jonw0224/PPMScope/Contributions/Dennis Waddell/Analog_Board.pdf

Analog Board

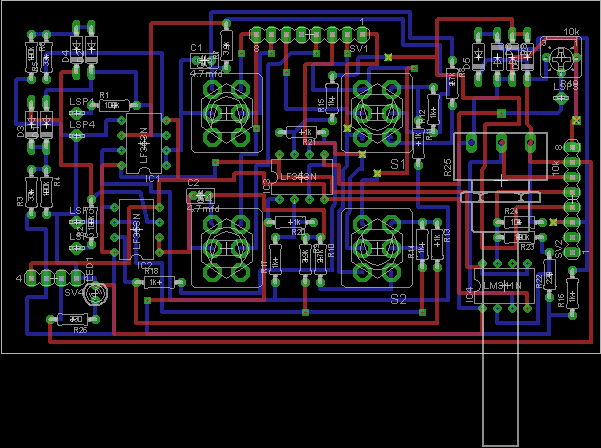
[picture p5: figure]

Note:
1. Board Size 4 x 2.35
2. Red traces on top side blue on bottom
3. R25 shows shaft horizontal is actually mounted vertical through front panel.
