jonw0224/PPMScope/Contributions/Dennis Waddell/Anlgsch.pdf

Analog Board Schematic

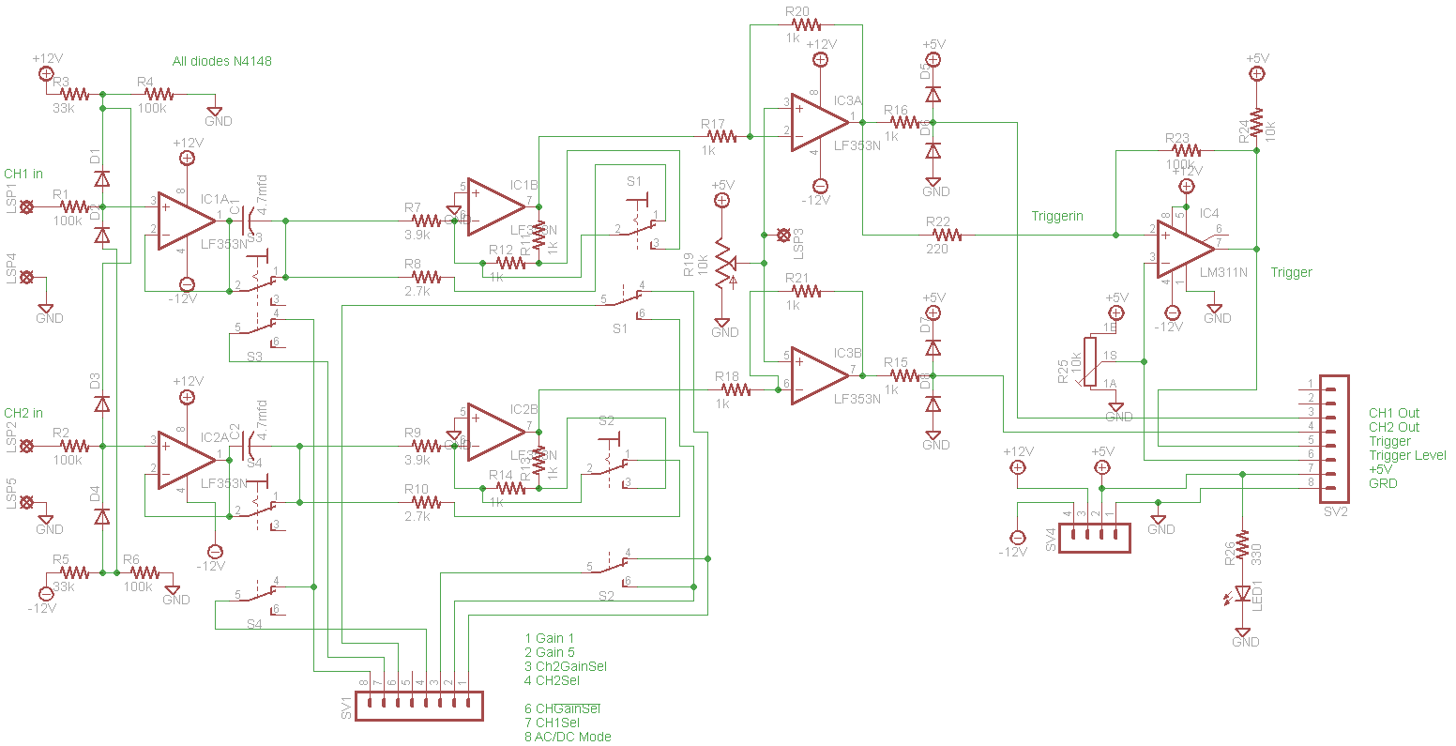
[picture p6: figure]

Note:
1. SV1 and SV2 headers mount on bottom side of board.
2. SV4 Rt. Angle header mount on top side of board.
