jonw0224/PPMScope/Contributions/Dennis Waddell/Power_Supply_Board.pdf

Power Supply Board

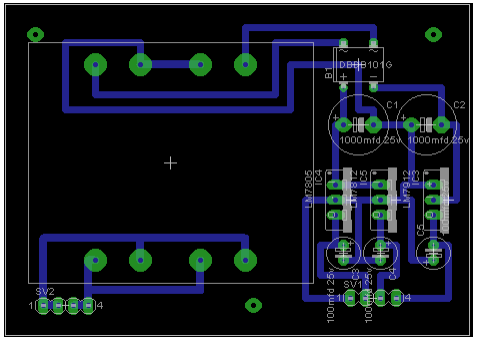
[picture p7: figure]
