jonw0224/PPMScope/Contributions/Dennis Waddell/Power_Supply_Schemati1.pdf

Power Supply Schematic

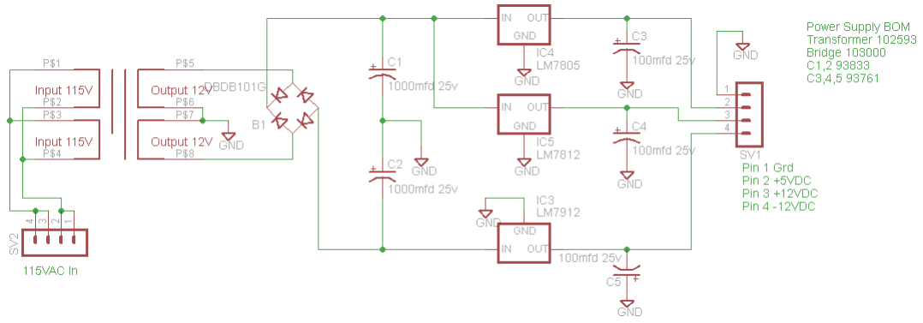
[picture p8: figure]
