jonw0224/PPMScope/Contributions/Dennis Waddell/Processor_Board.pdf

Processor Board

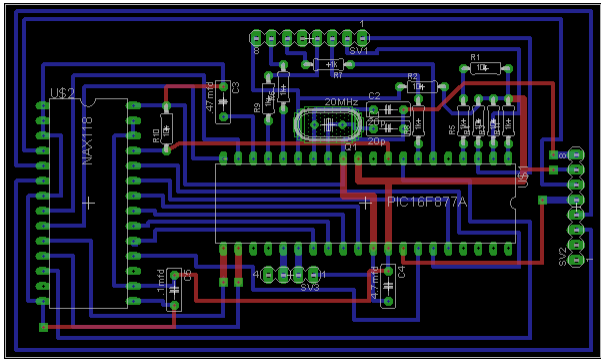
[picture p9: figure]

Note:
1. Board size 3.95 x 2.35
2. Red top side blue bottom.
