jonw0224/PPMScope/Contributions/Dennis Waddell/Processor_Board_Schemati1.pdf

Processor Board Schematic

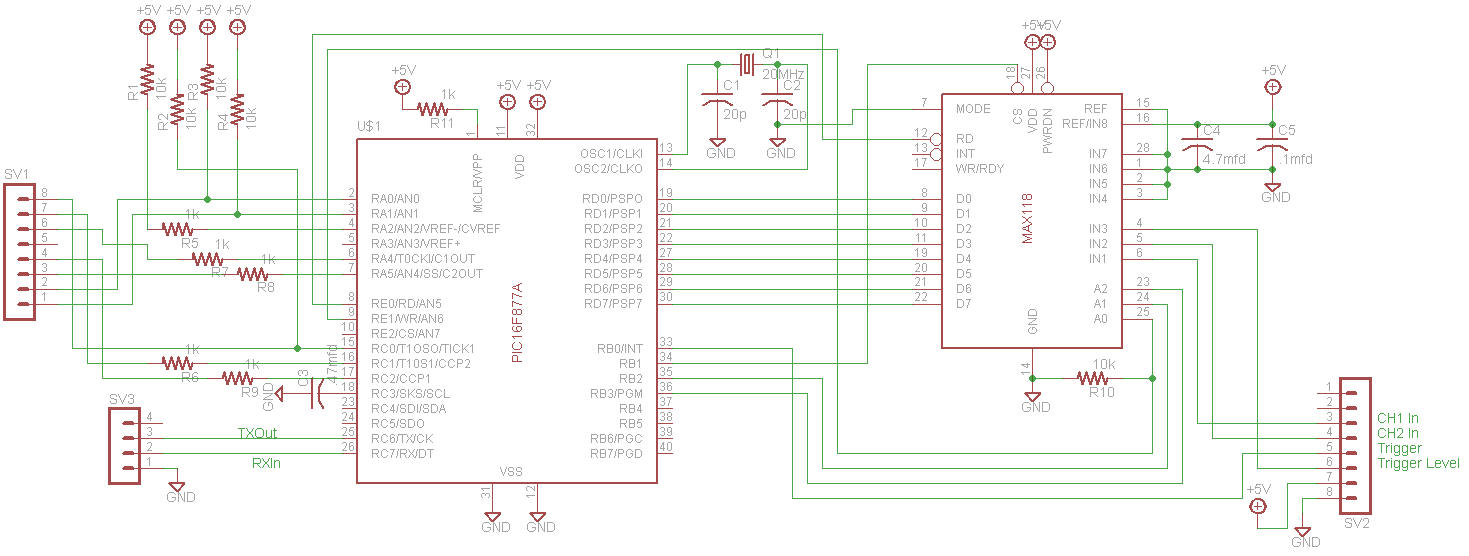
[picture p10: figure]
