jonw0224/PPMScope/PCB/Version 1.05/PCB.pdf

New_job (Current screen) Scale=1.00 Thu Dec 22 17:05:05 2011

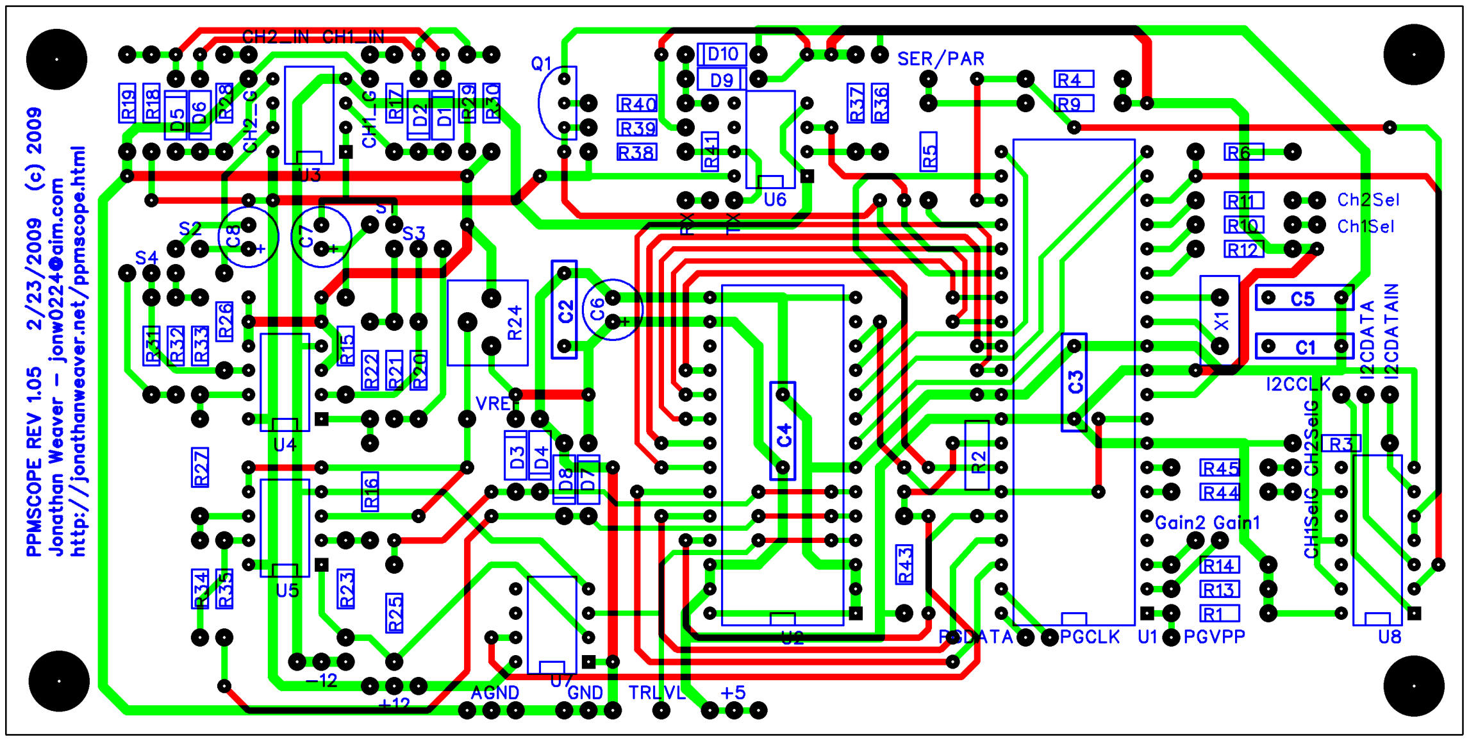
[picture p12: figure]
