jonw0224/PPMScope/PCB/Version 1.05/PCBBottom.pdf

New_job (Current screen) Scale=1.00 Thu Dec 22 17:06:14 2011

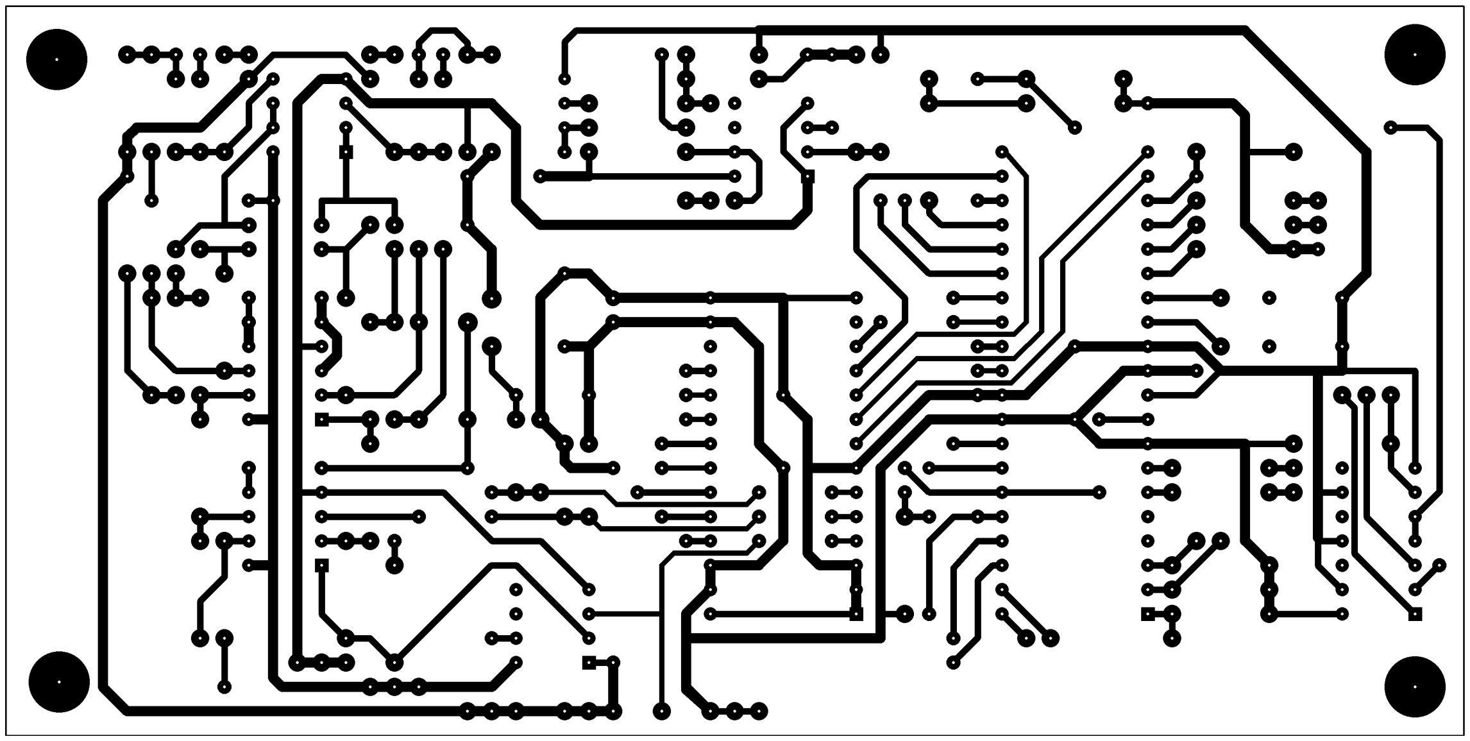
[picture p13: figure]
