jonw0224/PPMScope/PCB/Version 1.05/PCBTopMirrored.pdf

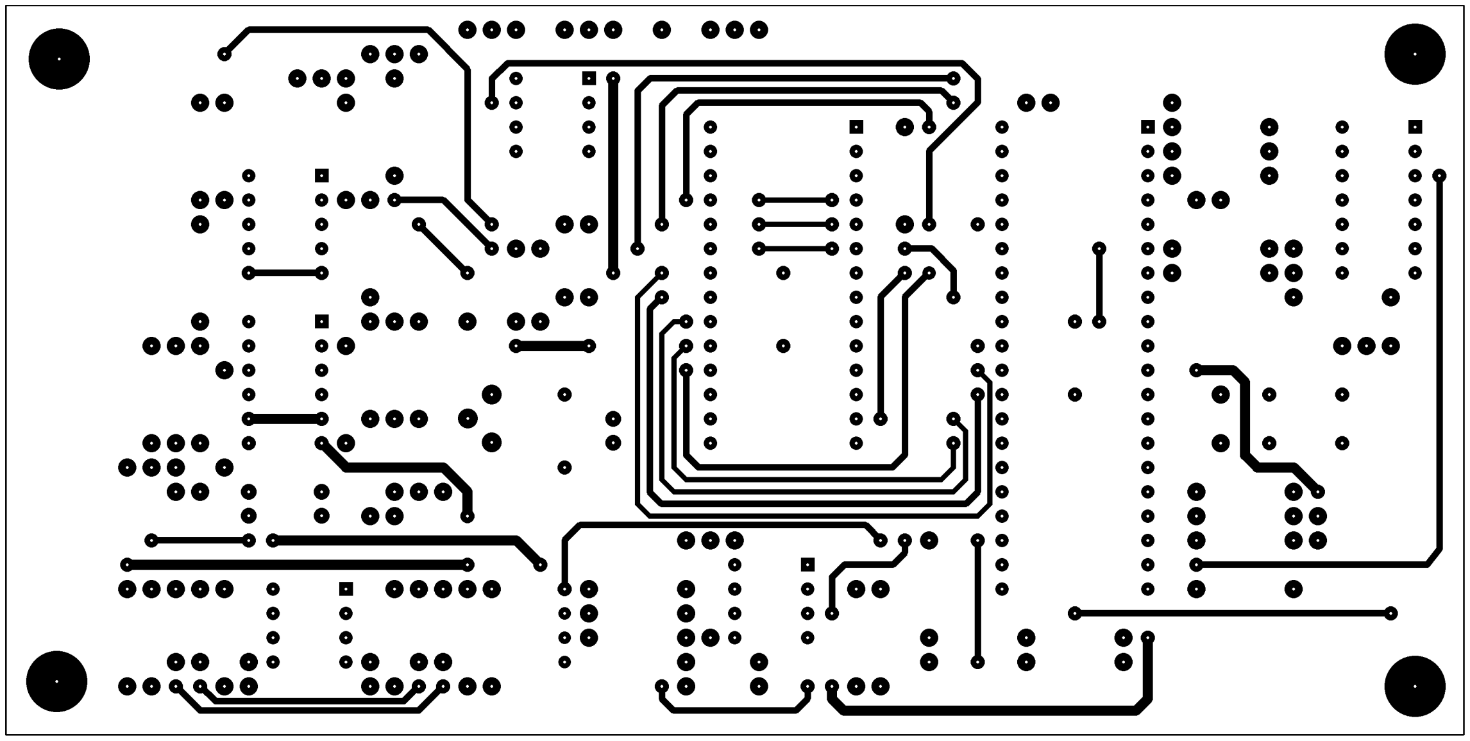
[picture p14: figure]

New_job (Current screen) Scale=1.00 Thu Dec 22 17:07:16 2011
