jonw0224/PPMScope/Contributions/Chris_PCB/bottom_copper.png

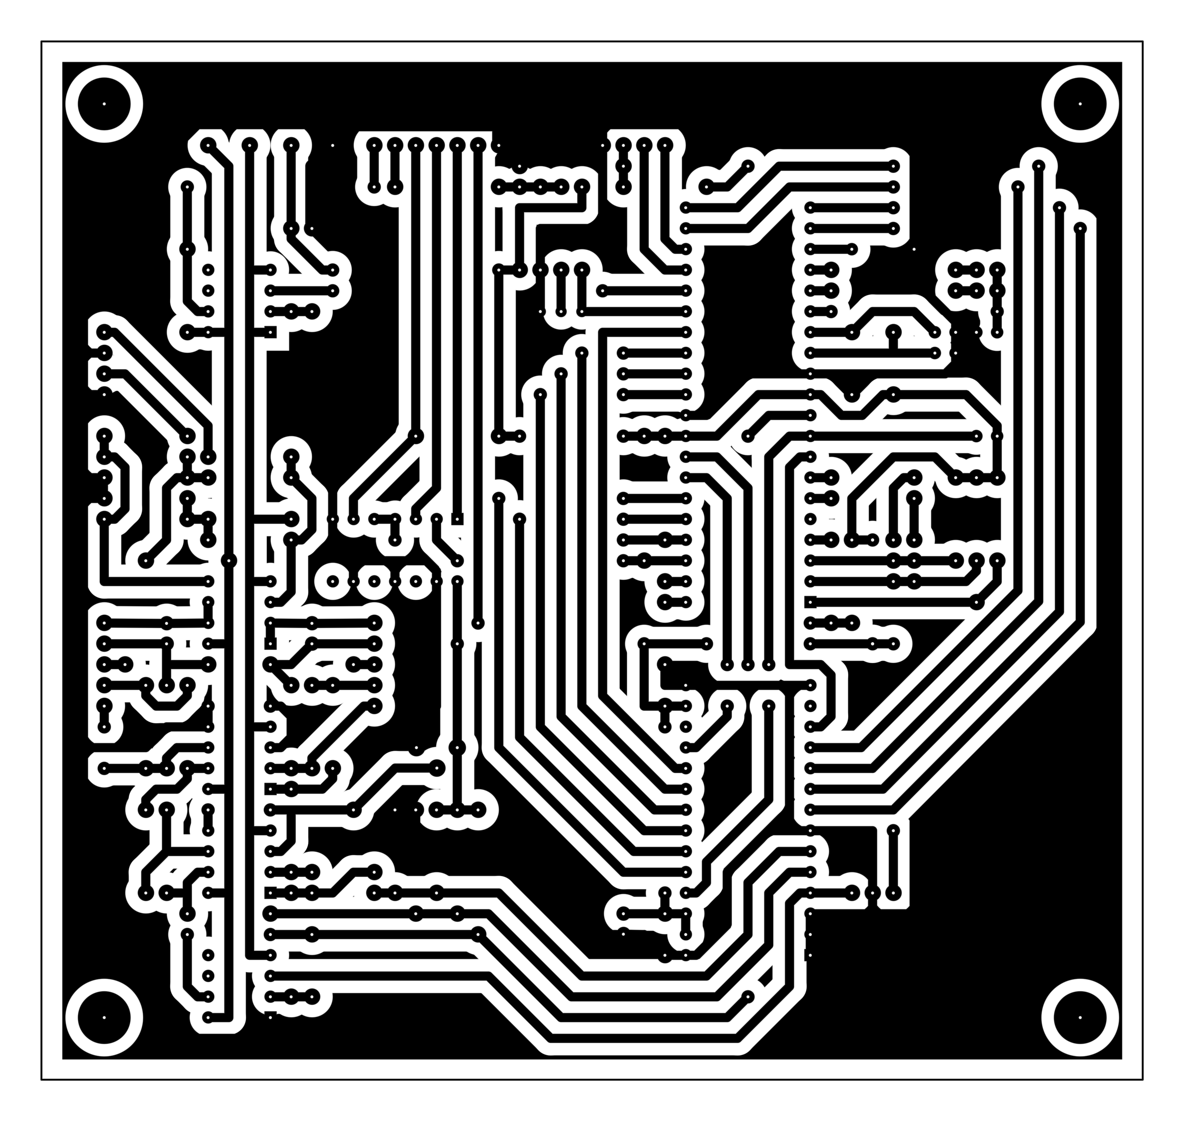
Contributions/Chris_PCB/bottom_copper.png
