jonw0224/PPMScope/Contributions/DaveDeBoer_Perfboard/PPmScope_1.05_bot.jpg

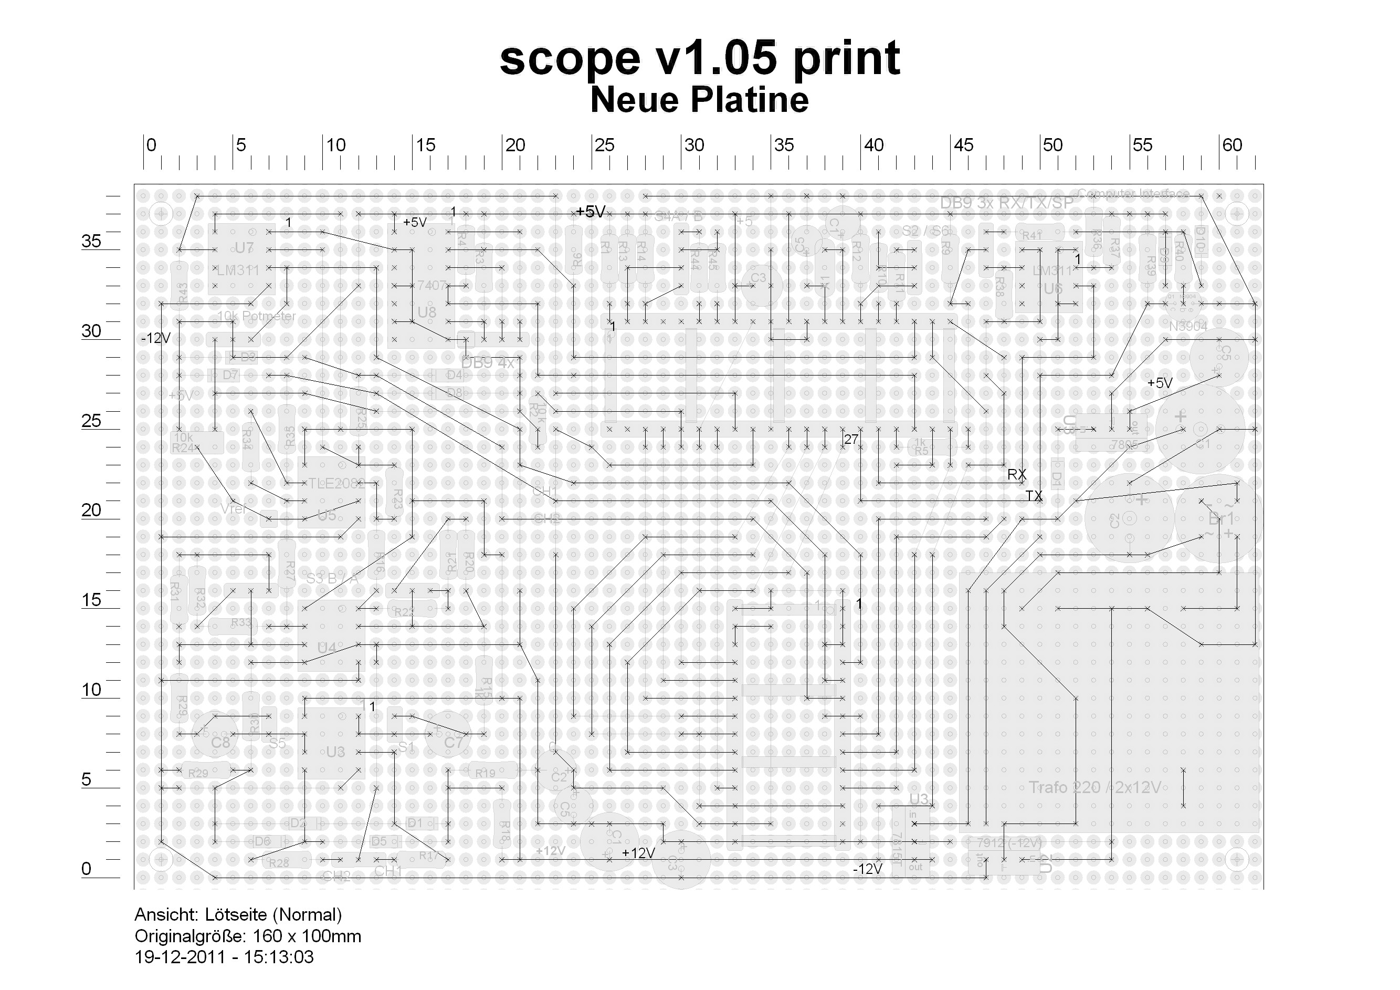
Contributions/DaveDeBoer_Perfboard/PPmScope_1.05_bot.jpg
