jonw0224/PPMScope/Contributions/DaveDeBoer_Perfboard/PPmScope_1.05_top.jpg

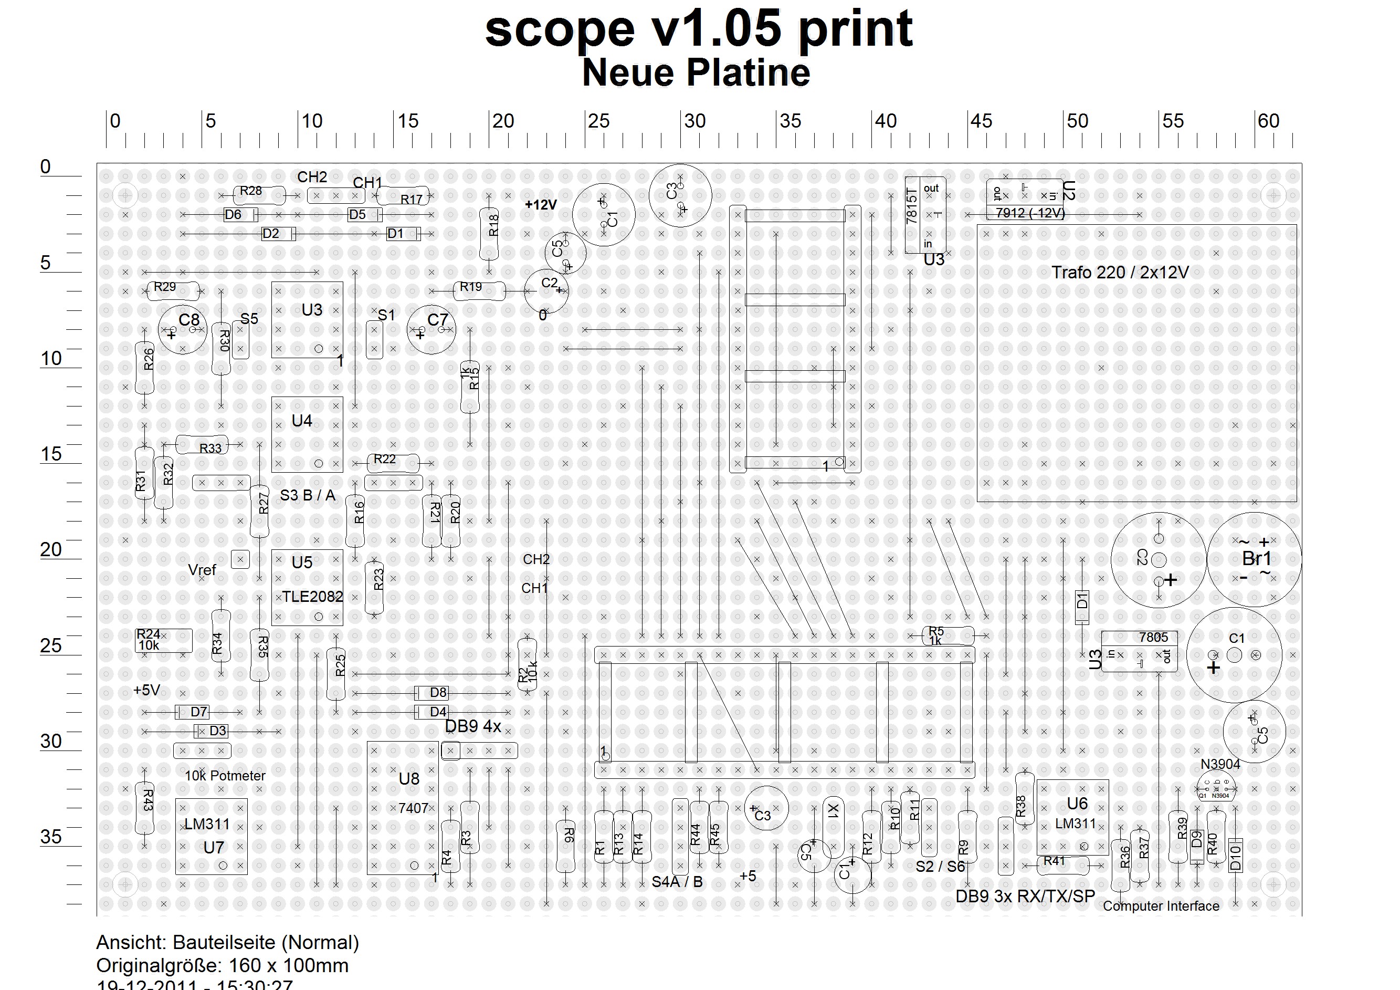
Contributions/DaveDeBoer_Perfboard/PPmScope_1.05_top.jpg
