jonw0224/PPMScope/Contributions/Dennis Waddell/01070001.JPG

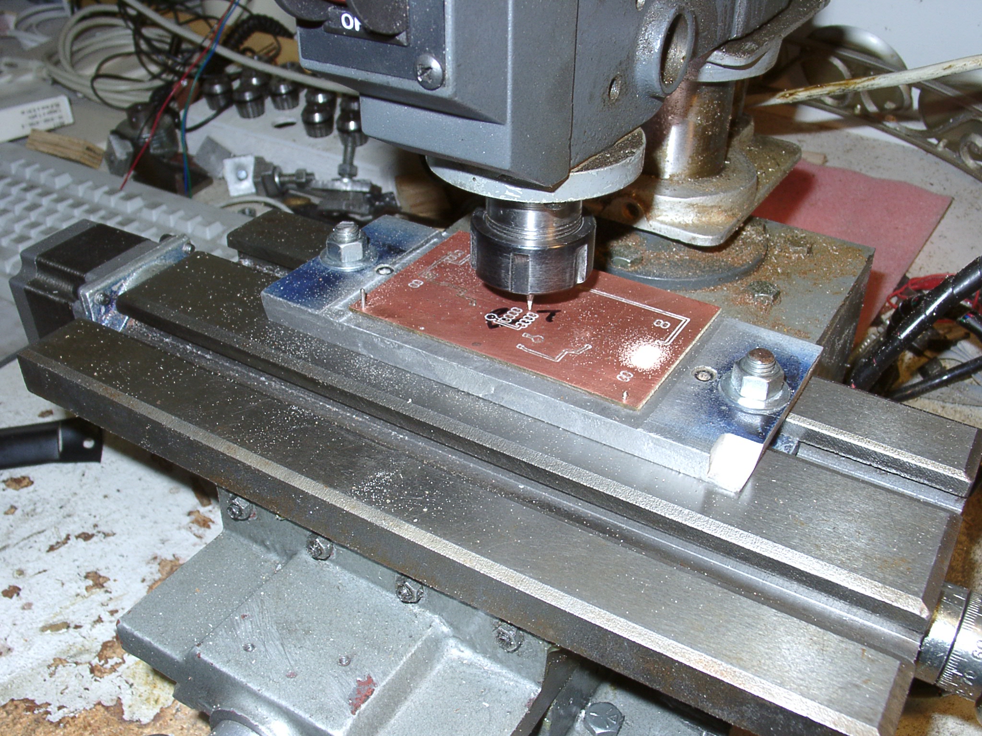
Contributions/Dennis Waddell/01070001.JPG
