jonw0224/PPMScope/Contributions/Dennis Waddell/01070002.JPG

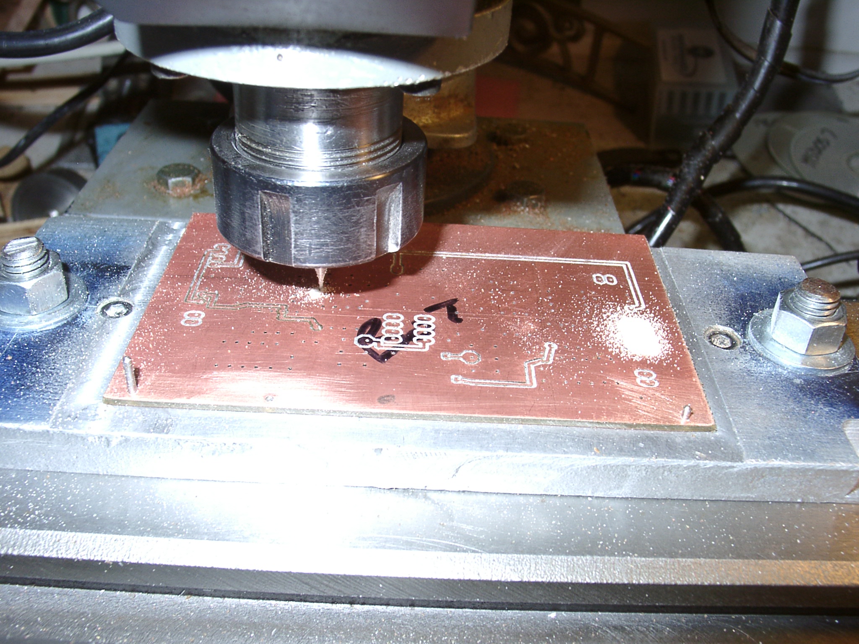
Contributions/Dennis Waddell/01070002.JPG
