jonw0224/PPMScope/Contributions/Dennis Waddell/02050001.JPG

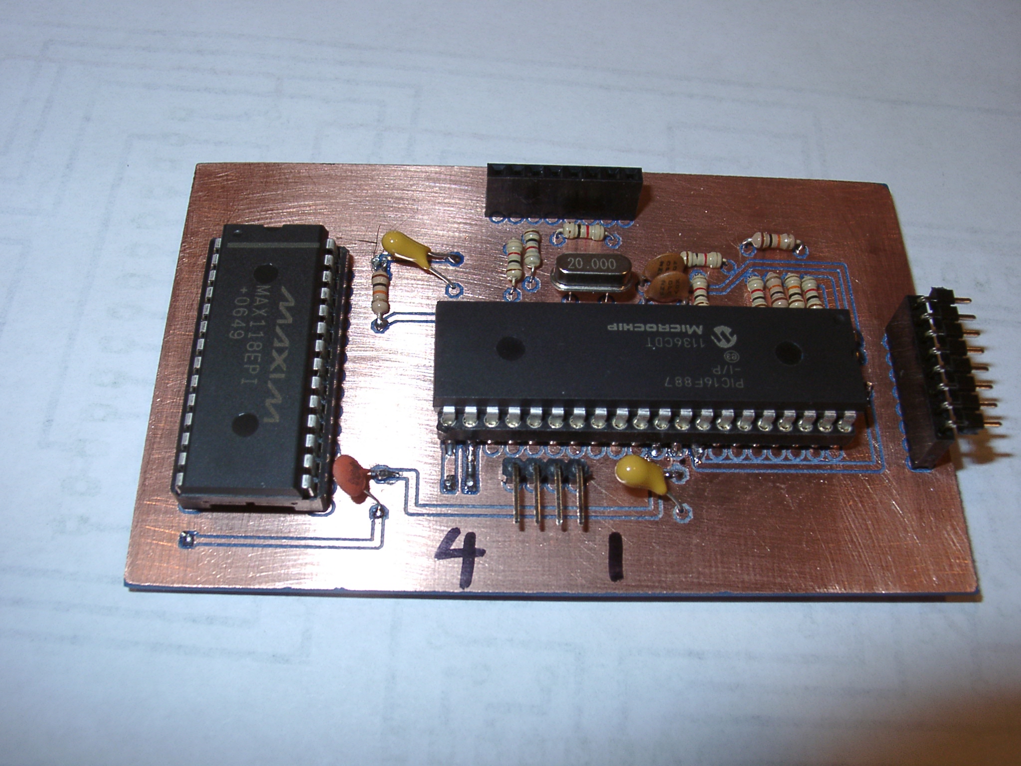
Contributions/Dennis Waddell/02050001.JPG
