jonw0224/PPMScope/Contributions/Dennis Waddell/02050003.JPG

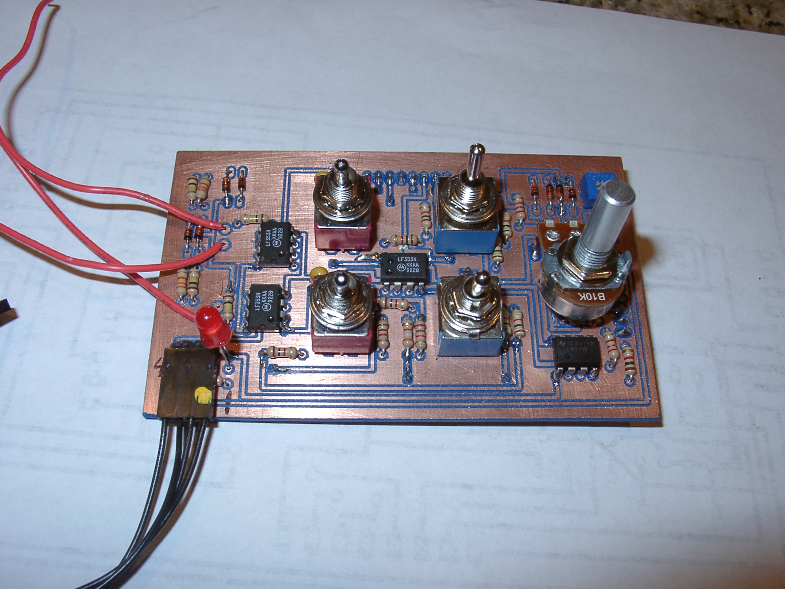
Contributions/Dennis Waddell/02050003.JPG
