jonw0224/PPMScope/Contributions/Dennis Waddell/02050004.JPG

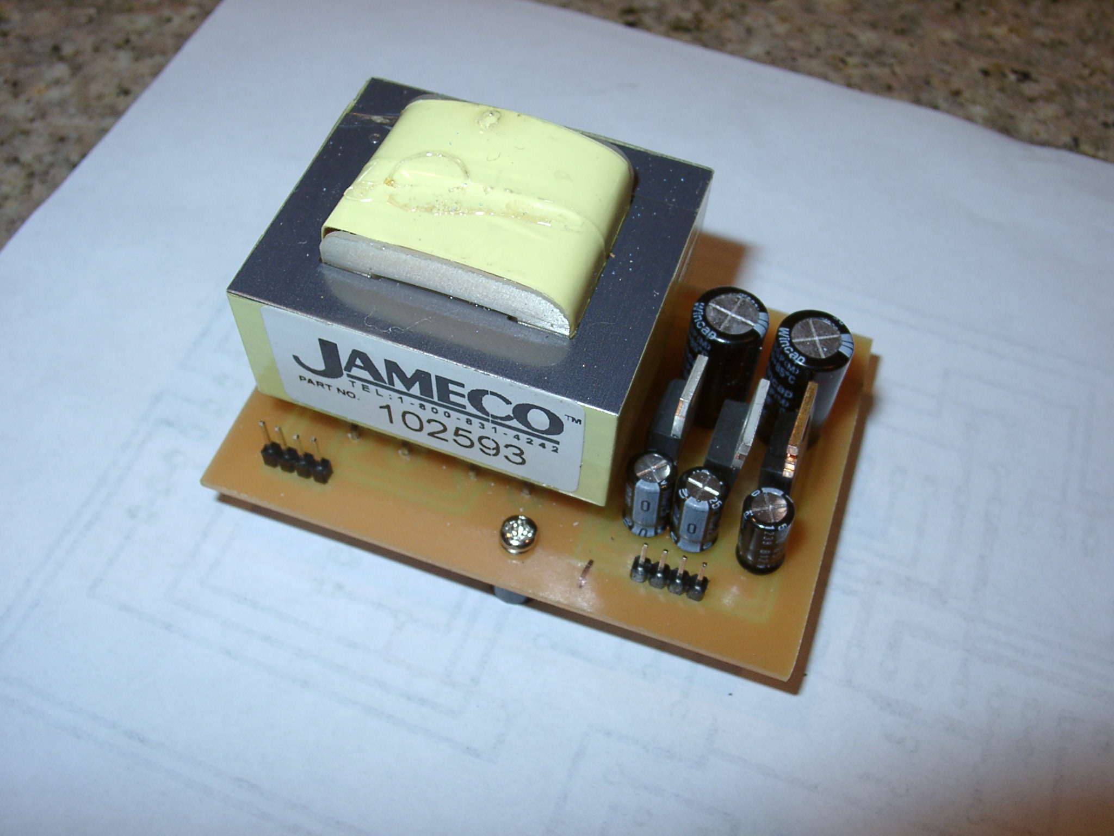
Contributions/Dennis Waddell/02050004.JPG
