jonw0224/PPMScope/Contributions/Dennis Waddell/02180001.JPG

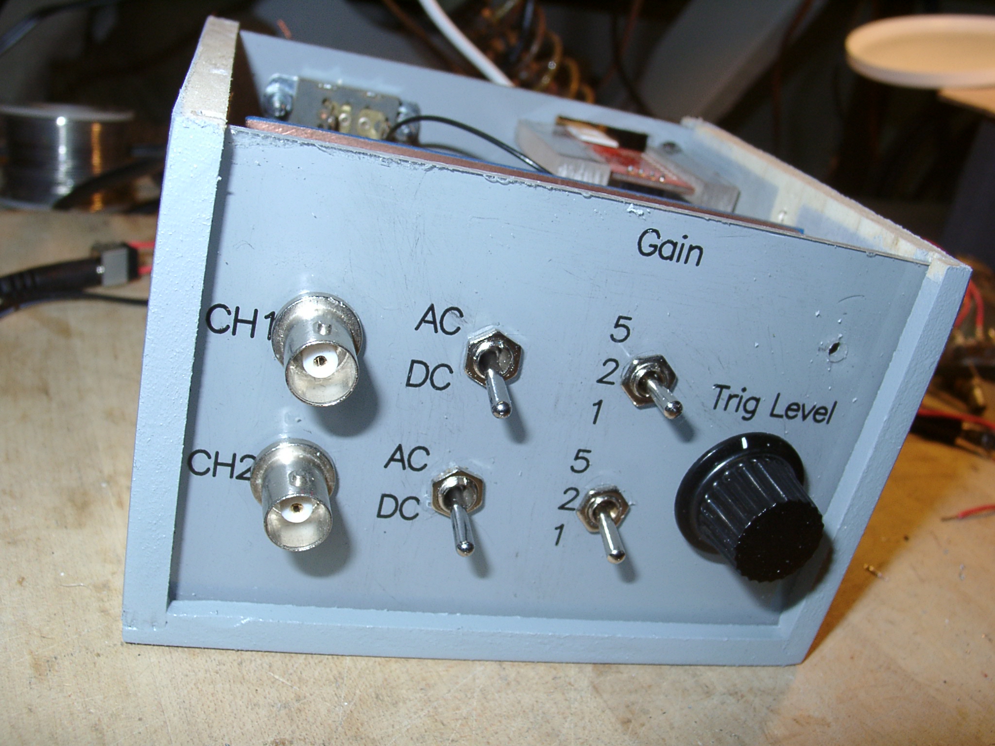
Contributions/Dennis Waddell/02180001.JPG
