jonw0224/PPMScope/Contributions/Dennis Waddell/02180002.JPG

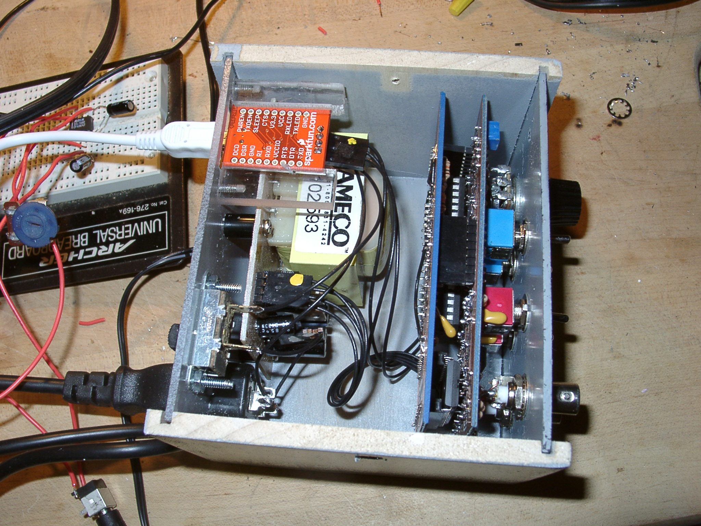
Contributions/Dennis Waddell/02180002.JPG
