jonw0224/PPMScope/Contributions/Dennis Waddell/02180003.JPG

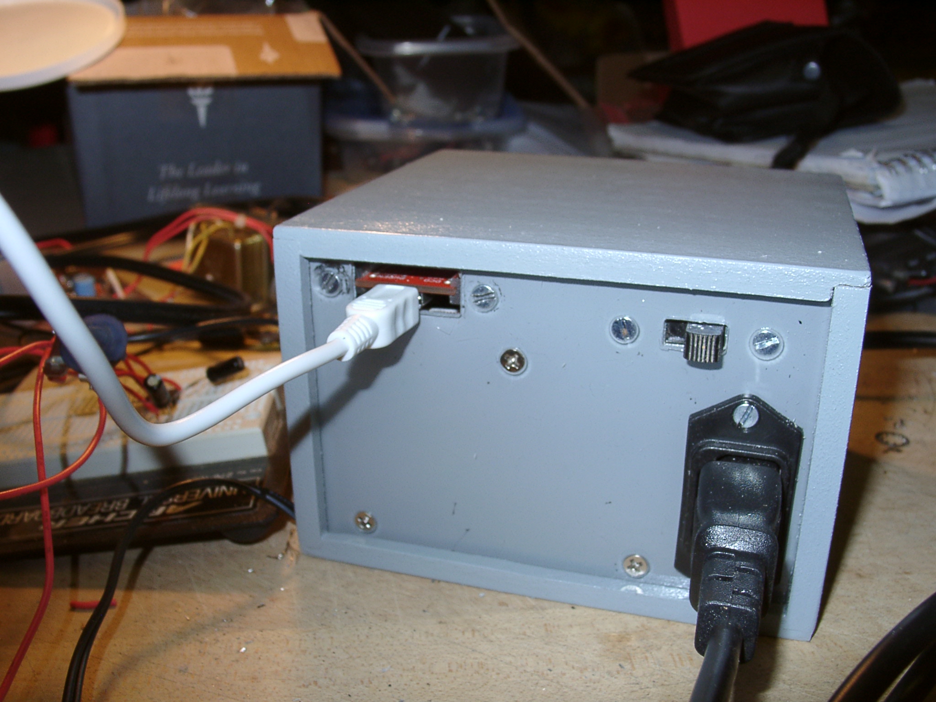
Contributions/Dennis Waddell/02180003.JPG
