jonw0224/PPMScope/Contributions/Dennis Waddell/02180005.JPG

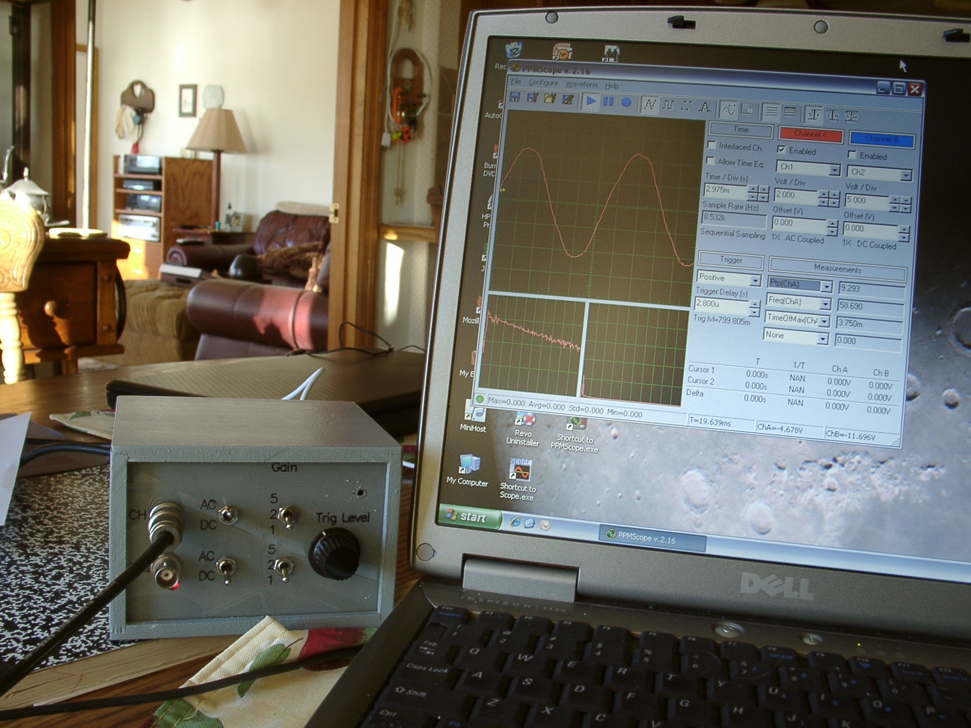
Contributions/Dennis Waddell/02180005.JPG
