jonw0224/PPMScope/Contributions/Paul Messer/DSOscope_A02/PCB/A02/CAM_DSOscope_AnalogBrd_A02/DSOscope_AnalogBrd_A02.JPG

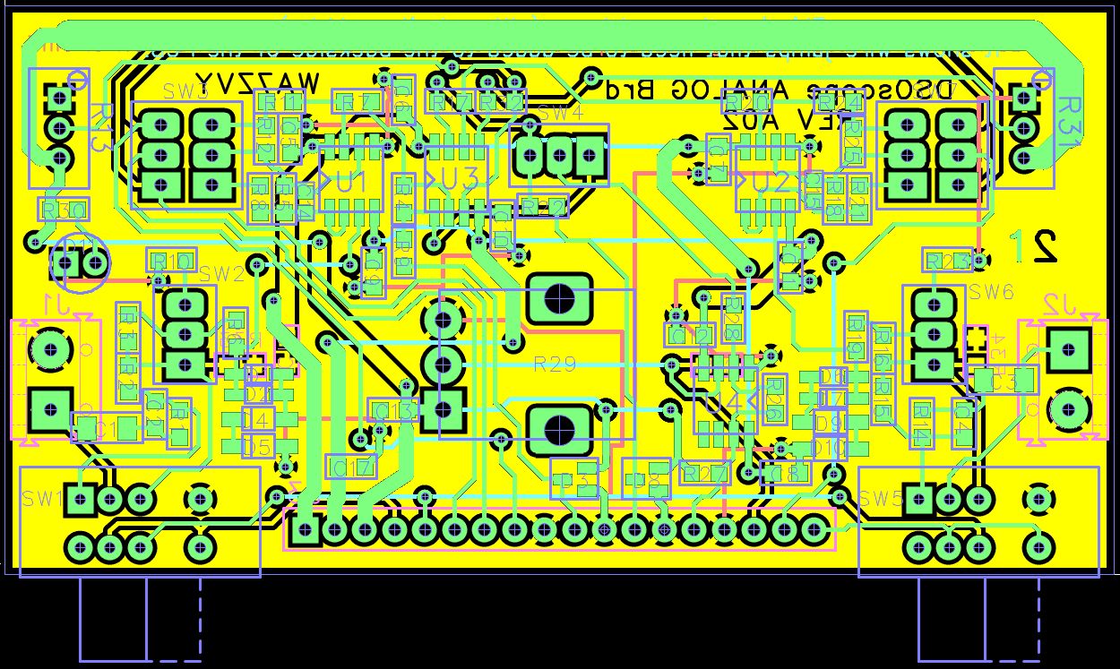
Contributions/Paul Messer/DSOscope_A02/PCB/A02/CAM_DSOscope_AnalogBrd_A02/DSOscope_AnalogBrd_A02.JPG
