jonw0224/PPMScope/Contributions/Paul Messer/DSOscope_A02/Photos/P1010014.JPG

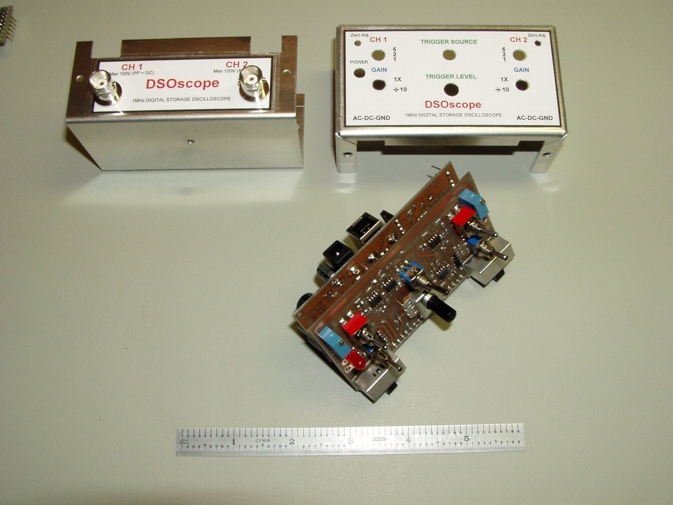
Contributions/Paul Messer/DSOscope_A02/Photos/P1010014.JPG
