jonw0224/PPMScope/Contributions/Paul Messer/DSOscope_A02/Photos/P1010017.JPG

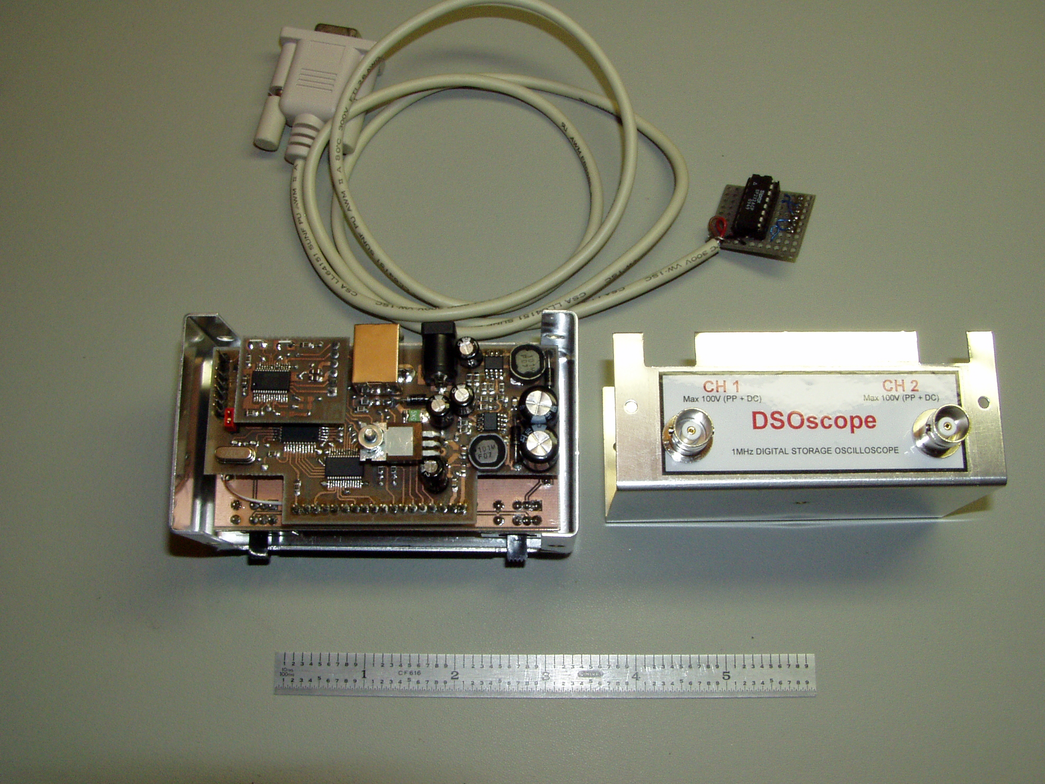
Contributions/Paul Messer/DSOscope_A02/Photos/P1010017.JPG
