jonw0224/PPMScope/Contributions/Paul Messer/DSOscope_A03/DSOscope_Rev_A03_20130113/PCB/A03/CAM_DSOscope_USBBrd_A03/DSOscope_USBBrd_A03_TOP.JPG

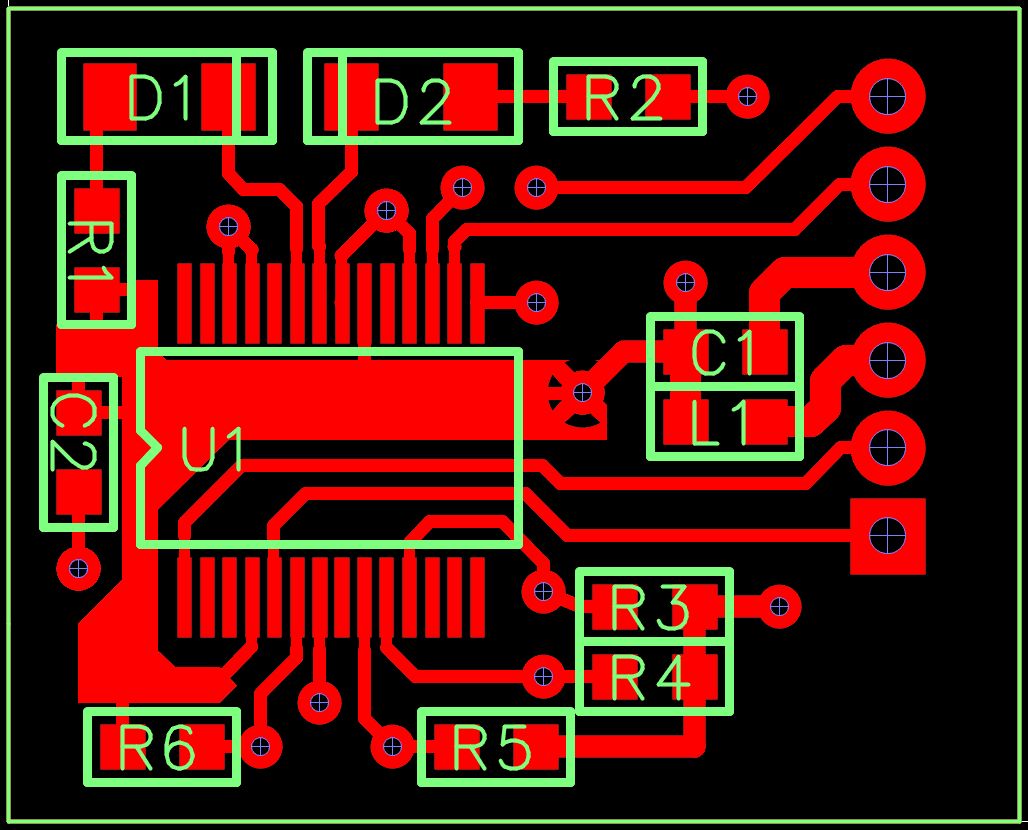
Contributions/Paul Messer/DSOscope_A03/DSOscope_Rev_A03_20130113/PCB/A03/CAM_DSOscope_USBBrd_A03/DSOscope_USBBrd_A03_TOP.JPG
