jonw0224/PPMScope/Contributions/Paul Messer/DSOscope_A03/DSOscope_Rev_A03_20130201/PCB/A03/AnalogBrd_A03_etch_bottom.jpg

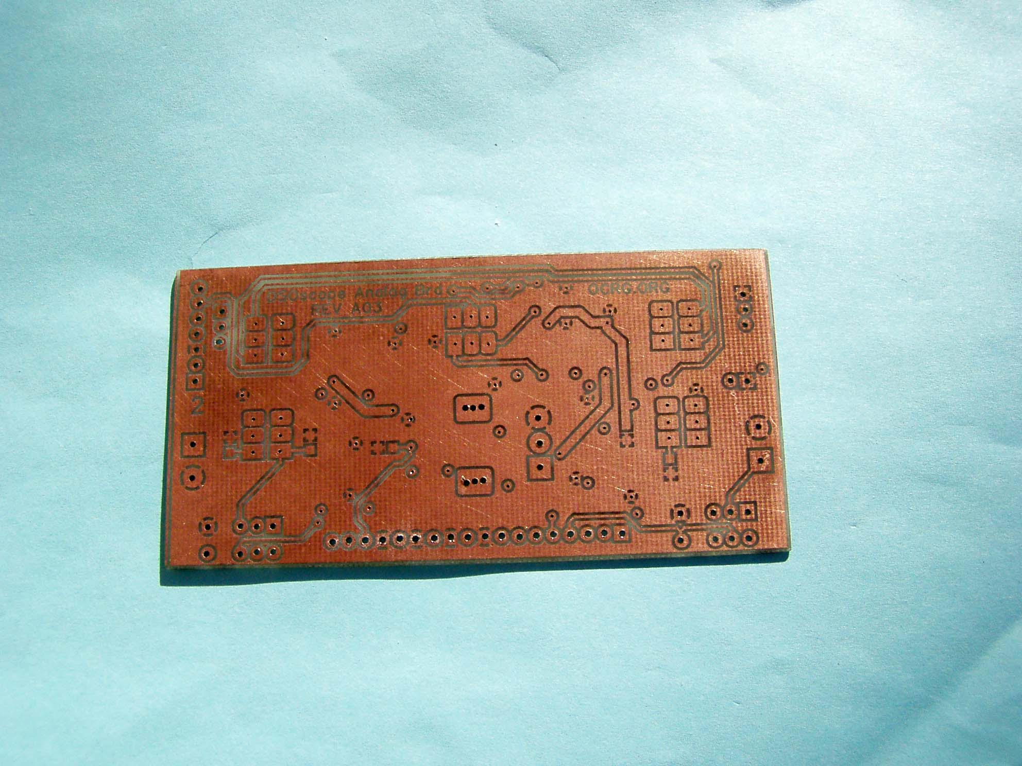
Contributions/Paul Messer/DSOscope_A03/DSOscope_Rev_A03_20130201/PCB/A03/AnalogBrd_A03_etch_bottom.jpg
