jonw0224/PPMScope/Contributions/Paul Messer/DSOscope_A03/DSOscope_Rev_A03_20130201/PCB/A03/CAM_DSOscope_AnalogBrd_A03/DSOscope_AnalogBrd_A03_TOP.JPG

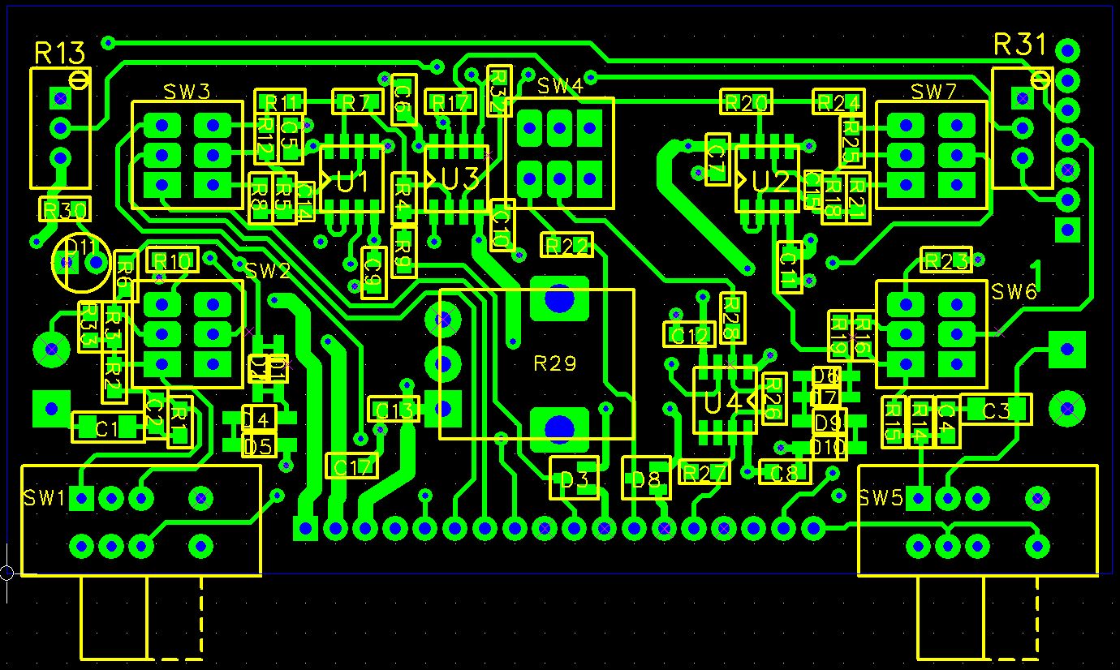
Contributions/Paul Messer/DSOscope_A03/DSOscope_Rev_A03_20130201/PCB/A03/CAM_DSOscope_AnalogBrd_A03/DSOscope_AnalogBrd_A03_TOP.JPG
