jonw0224/PPMScope/Contributions/Paul Messer/P1010008.JPG

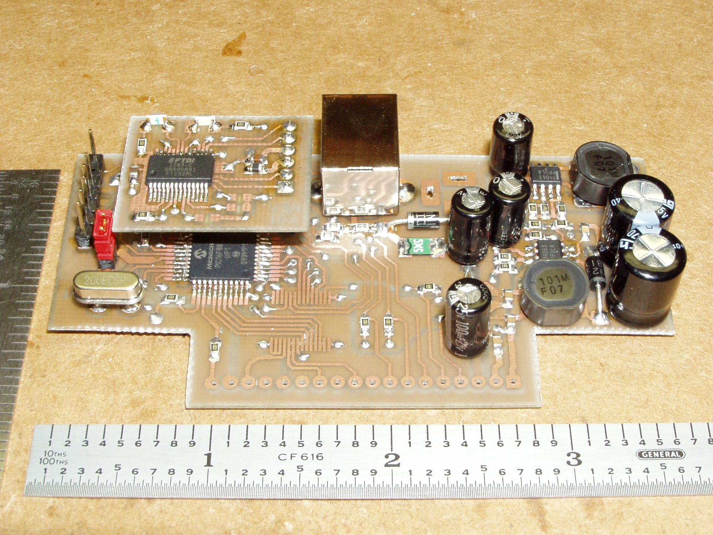
Contributions/Paul Messer/P1010008.JPG
