jonw0224/PPMScope/PCsource/Help/compile.jpg

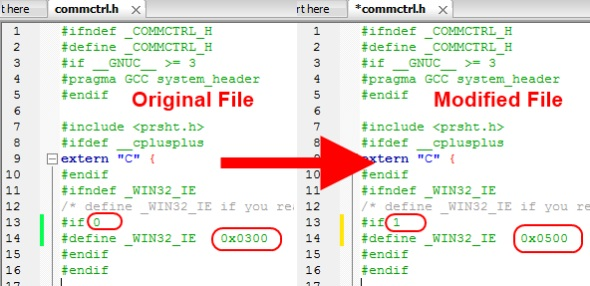
PCsource/Help/compile.jpg
