jonw0224/PPMScope/PCsource/Help/front.jpg

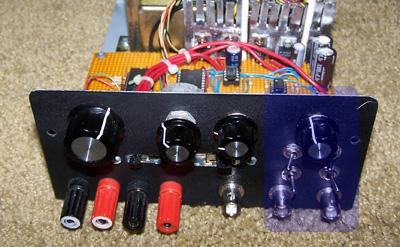
PCsource/Help/front.jpg
