jonw0224/PPMScope/PCsource/Help/library.jpg

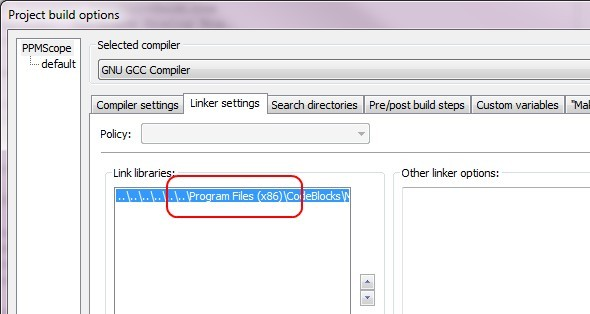
PCsource/Help/library.jpg
