jonw0224/PPMScope/PCsource/Help/parallel_conn_1.jpg

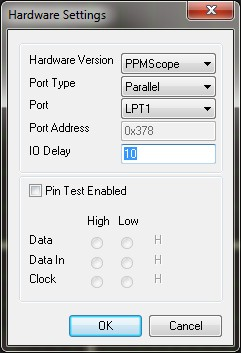
PCsource/Help/parallel_conn_1.jpg
