jonw0224/PPMScope/PCsource/Help/parallel_conn_2.jpg

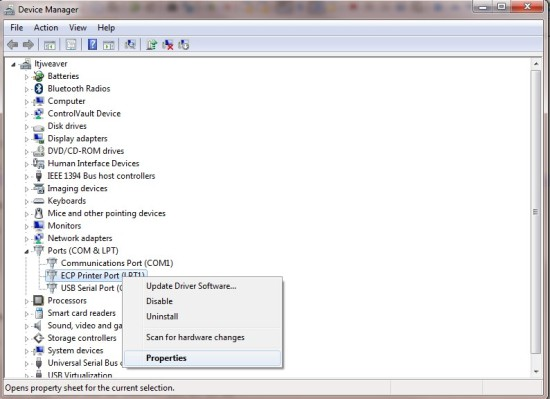
PCsource/Help/parallel_conn_2.jpg
