jonw0224/PPMScope/PCsource/Help/parallel_conn_3.jpg

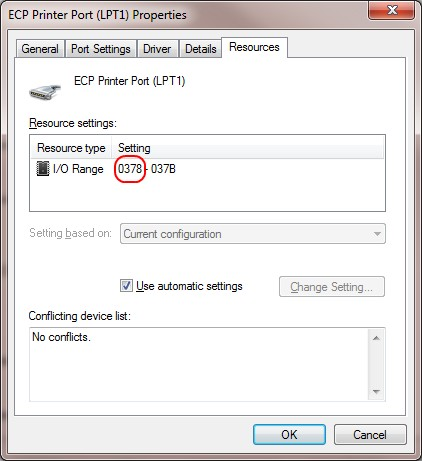
PCsource/Help/parallel_conn_3.jpg
