jonw0224/PPMScope/PCsource/Help/PCBBottom.jpg

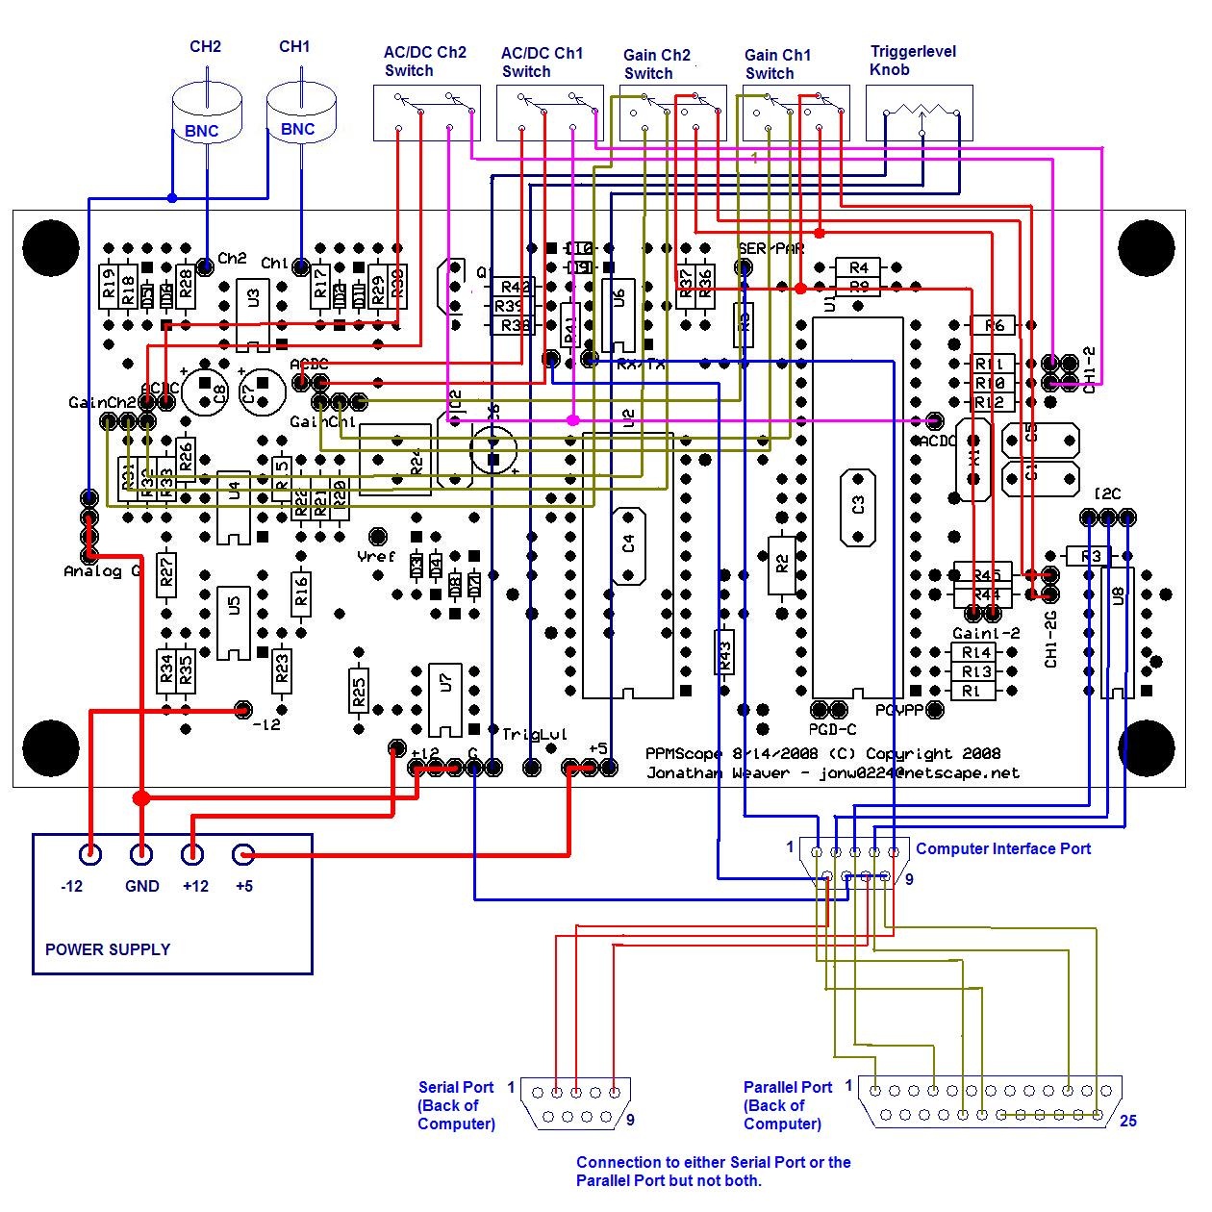
PCsource/Help/PCBBottom.jpg
