jonw0224/PPMScope/PCsource/Help/pp.gif

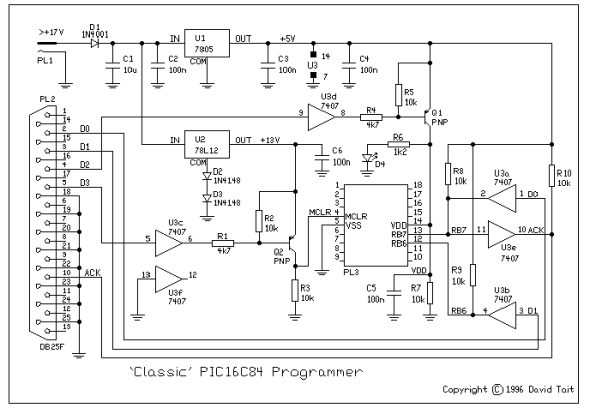
PCsource/Help/pp.gif
