jonw0224/PPMScope/PCsource/Help/proto.jpg

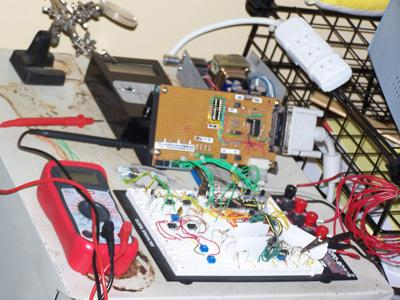
PCsource/Help/proto.jpg
