jonw0224/PPMScope/PCsource/Help/punchbd.jpg

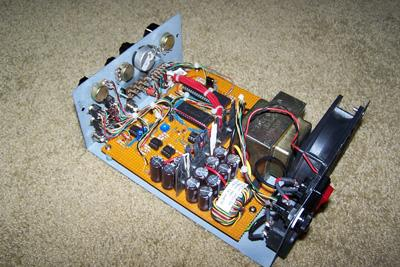
PCsource/Help/punchbd.jpg
