jonw0224/PPMScope/PCsource/Help/pwrsup.JPG

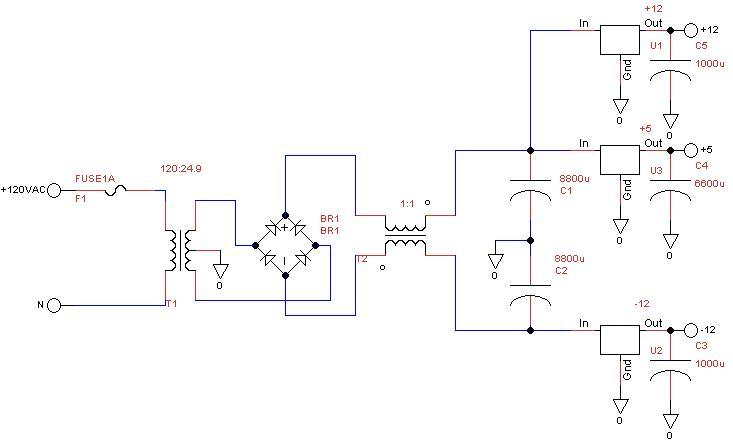
PCsource/Help/pwrsup.JPG
