jonw0224/PPMScope/PCsource/Help/screenkey.jpg

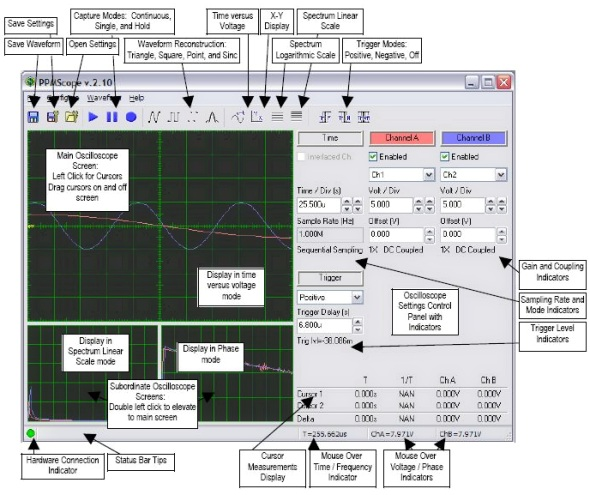
PCsource/Help/screenkey.jpg
