jonw0224/PPMScope/PCsource/Help/timeequsample.jpg

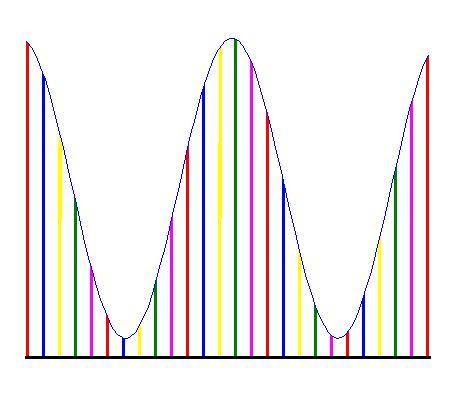
PCsource/Help/timeequsample.jpg
