jonw0224/PPMScope/PCsource/Help/usb_conn_1.jpg

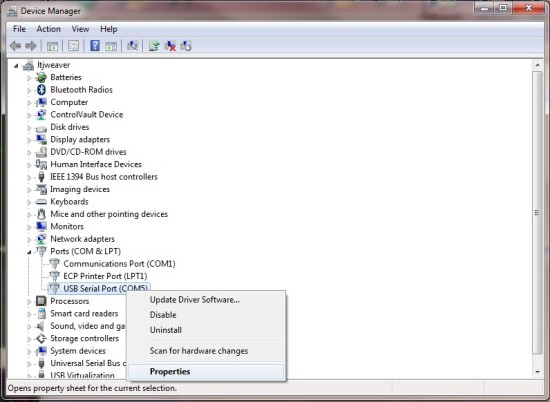
PCsource/Help/usb_conn_1.jpg
