jonw0224/PPMScope/PCsource/Help/usb_conn_2.jpg

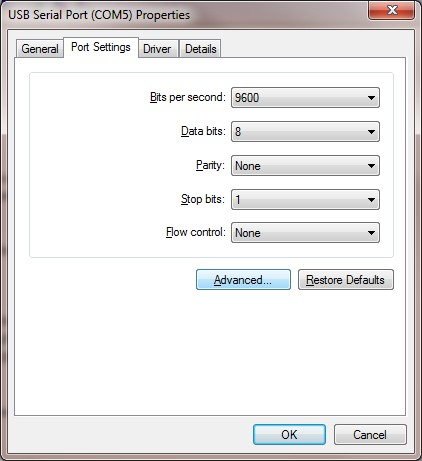
PCsource/Help/usb_conn_2.jpg
