jonw0224/PPMScope/PCsource/Help/usb_conn_3.jpg

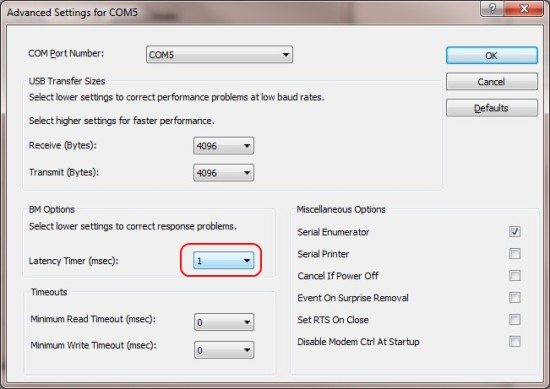
PCsource/Help/usb_conn_3.jpg
