jonw0224/PPMScope/PCsource/Help/WinPic800.gif

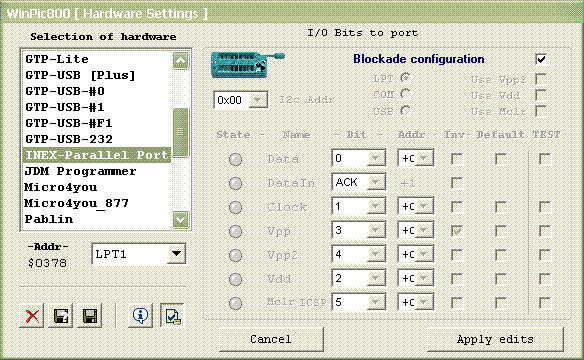
PCsource/Help/WinPic800.gif
