jonw0224/PPMScope/Pictures/20130627 AC to DC.jpg

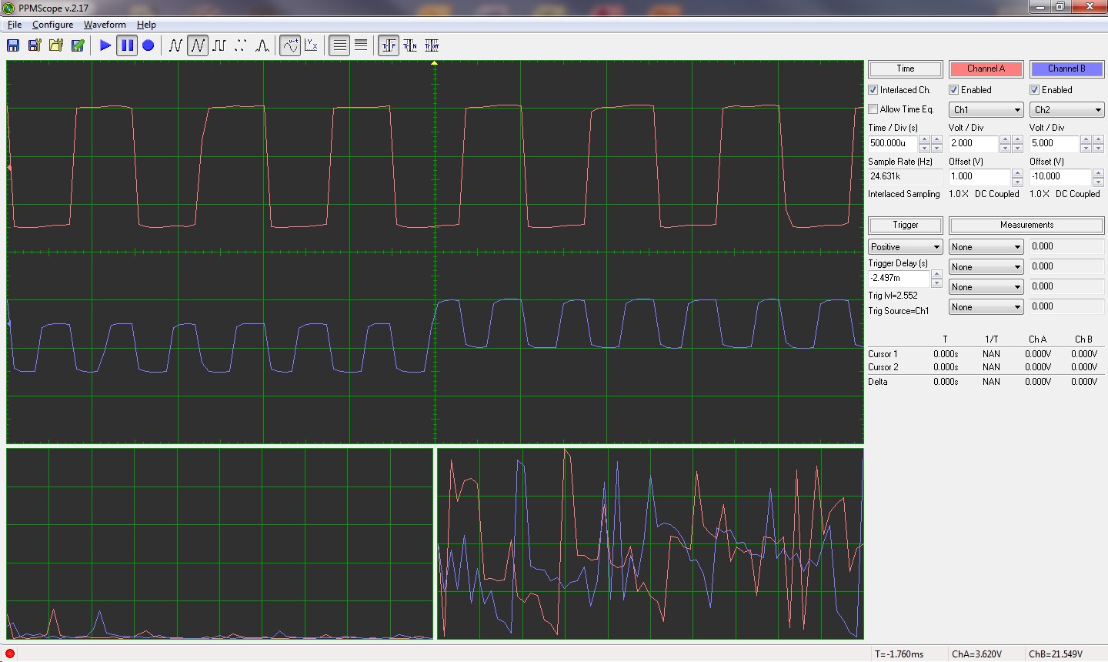
Pictures/20130627 AC to DC.jpg
