jonw0224/PPMScope/Pictures/20130627 GND to DC.jpg

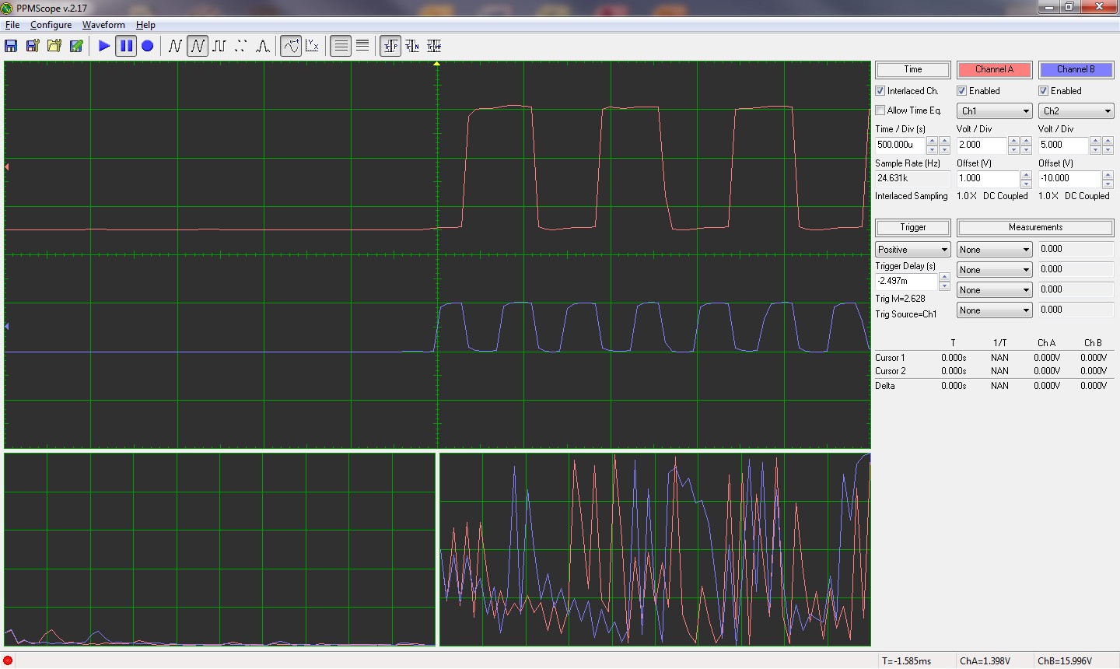
Pictures/20130627 GND to DC.jpg
