jonw0224/PPMScope/Pictures/0401112337-01.jpg

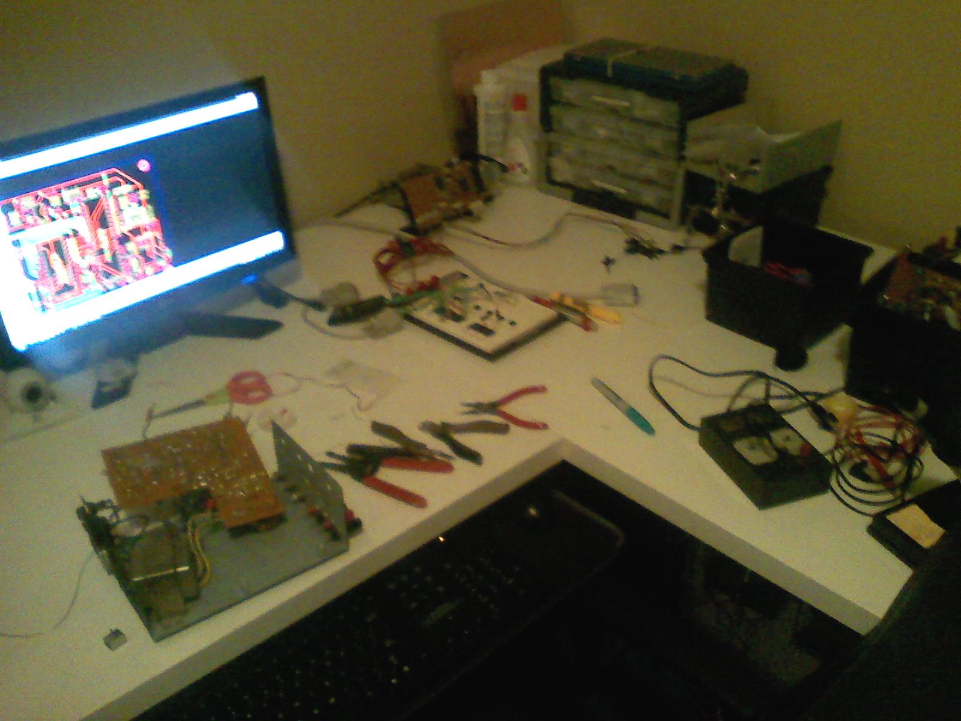
Pictures/0401112337-01.jpg
