jonw0224/PPMScope/Pictures/0426112234-00.jpg

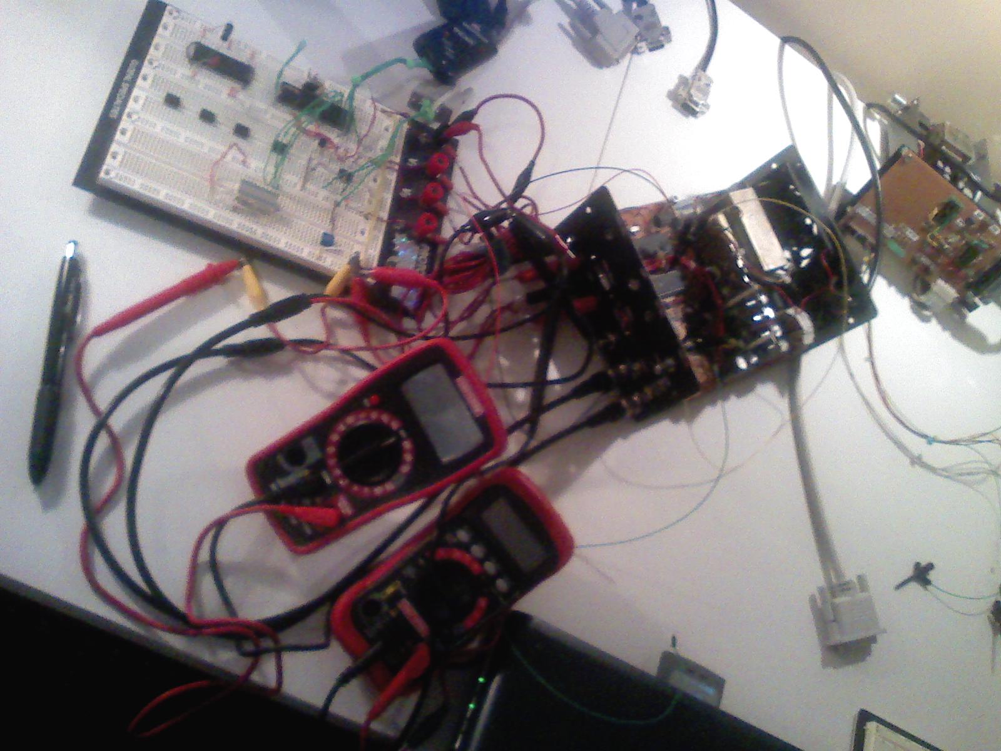
Pictures/0426112234-00.jpg
