jonw0224/PPMScope/Pictures/DavidDeBoer1.jpg

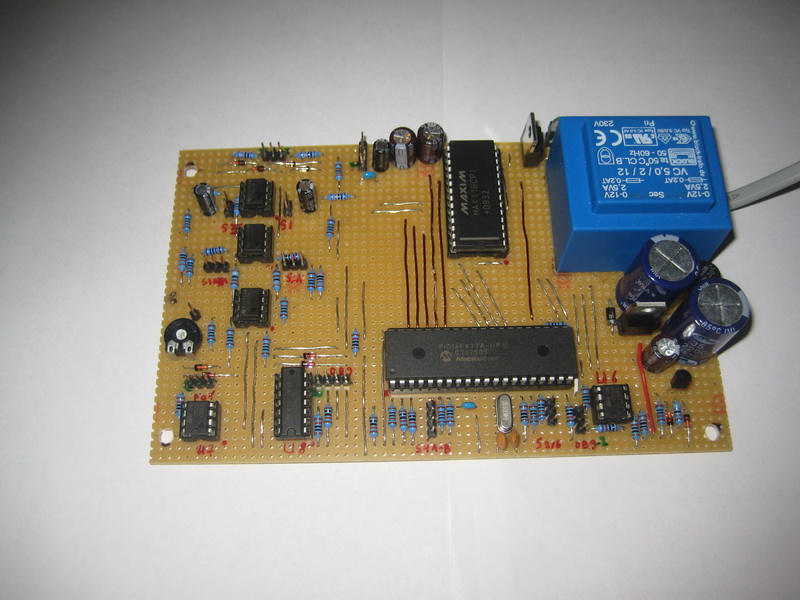
Pictures/DavidDeBoer1.jpg
