jonw0224/PPMScope/Pictures/DavidDeBoer3.jpg

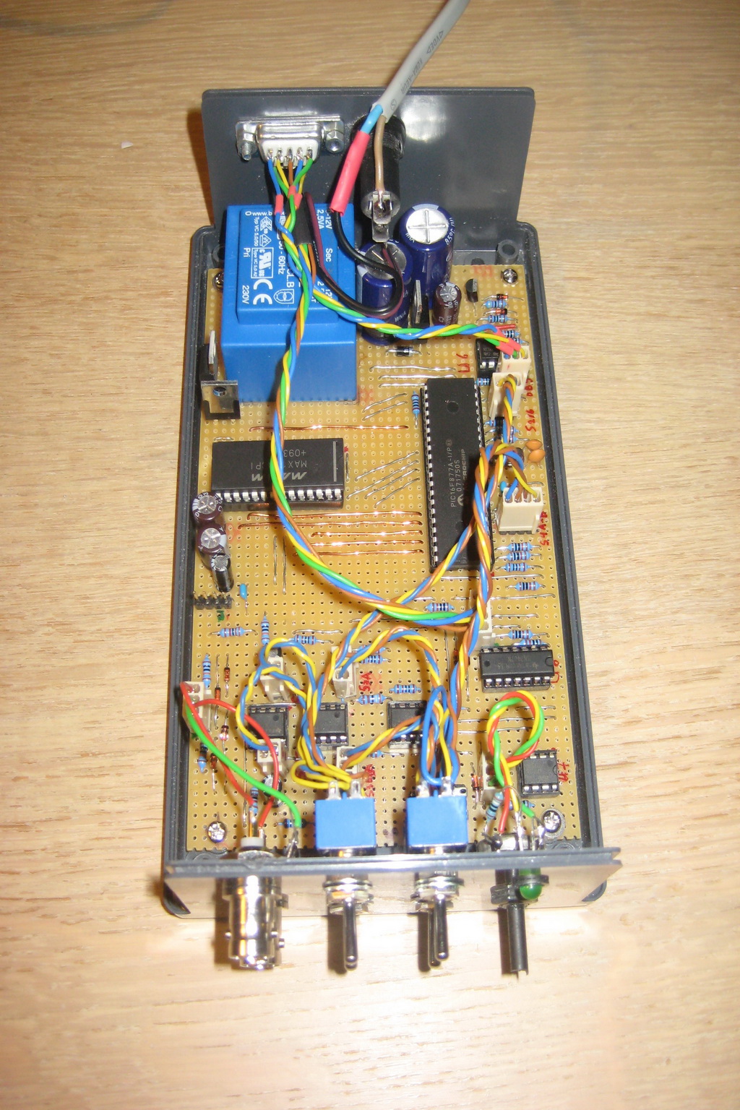
Pictures/DavidDeBoer3.jpg
