jonw0224/PPMScope/Pictures/GerVanDenHoek1.jpg

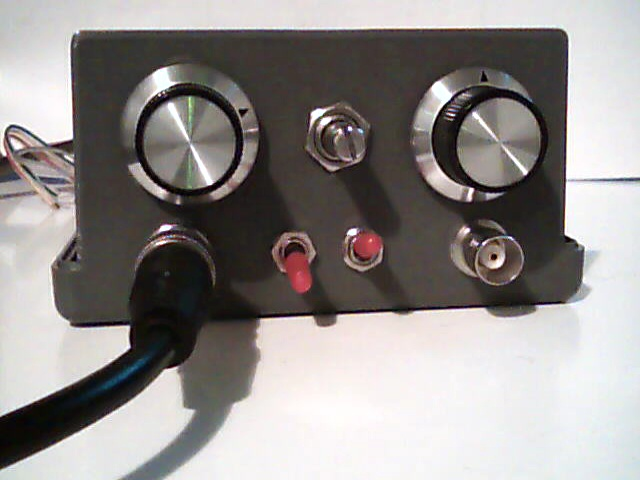
Pictures/GerVanDenHoek1.jpg
