jonw0224/PPMScope/Pictures/GerVanDenHoek2.jpg

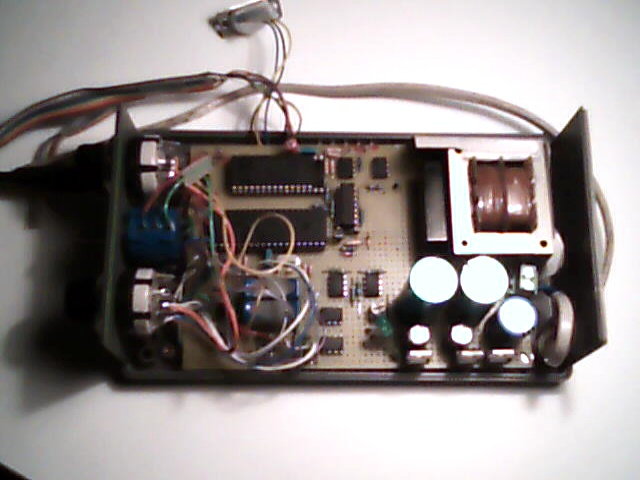
Pictures/GerVanDenHoek2.jpg
