jonw0224/PPMScope/Pictures/GerVanDenHoek3.jpg

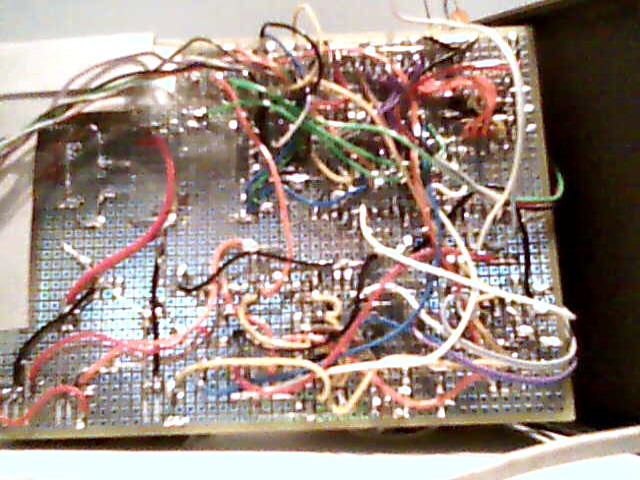
Pictures/GerVanDenHoek3.jpg
