jonw0224/PPMScope/Pictures/High Res Off Gain 1.jpg

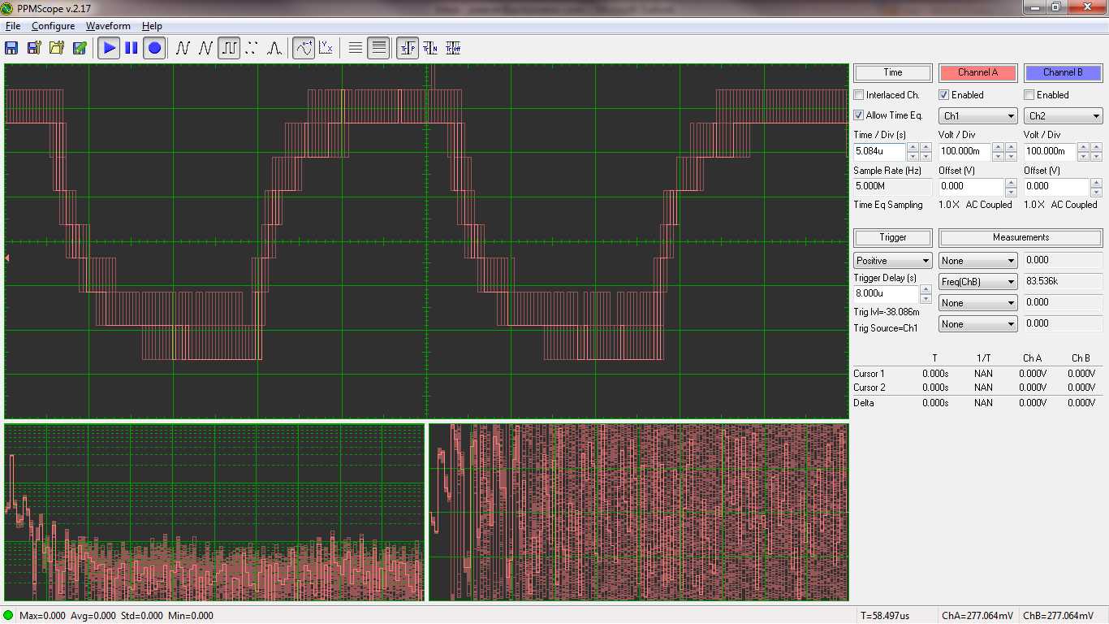
Pictures/High Res Off Gain 1.jpg
