jonw0224/PPMScope/Pictures/High Res Off Gain 5.jpg

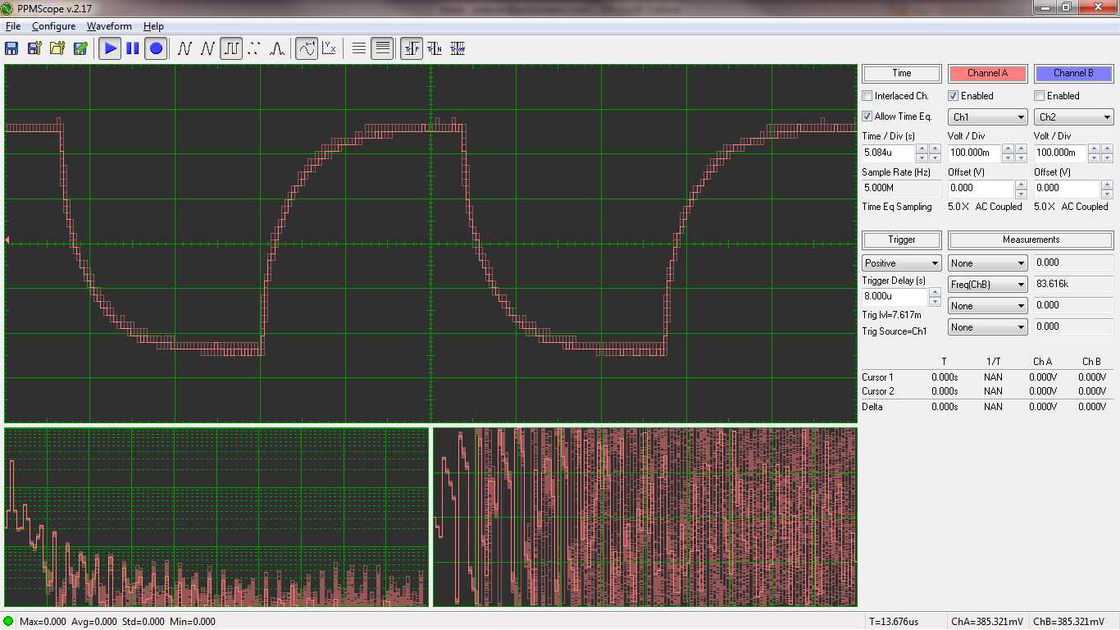
Pictures/High Res Off Gain 5.jpg
