jonw0224/PPMScope/Pictures/High Res On Gain 1.jpg

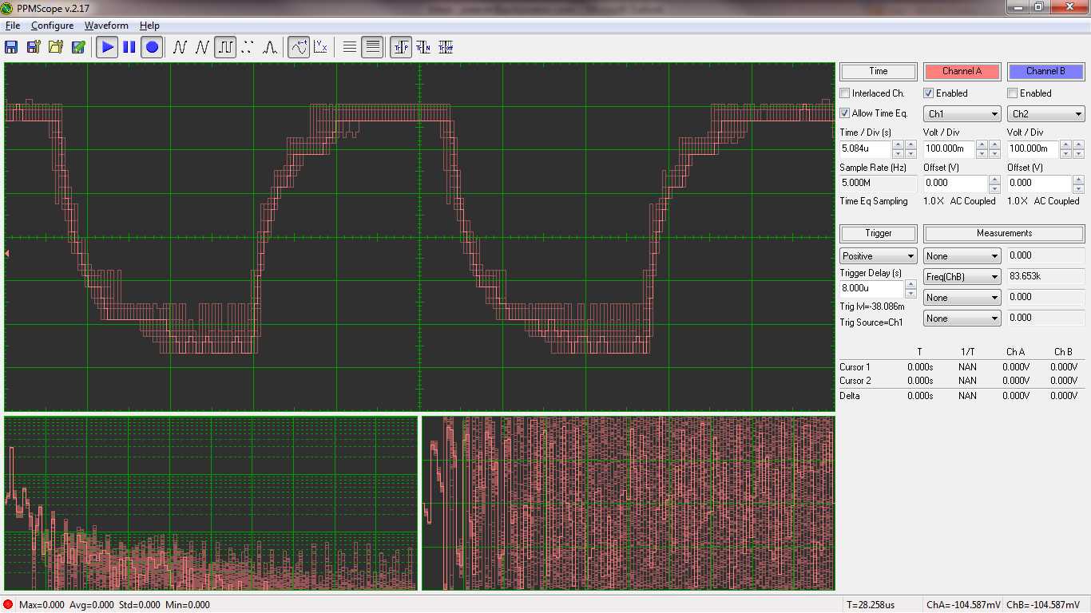
Pictures/High Res On Gain 1.jpg
