jonw0224/PPMScope/Pictures/High Res On Gain 5 Spline.jpg

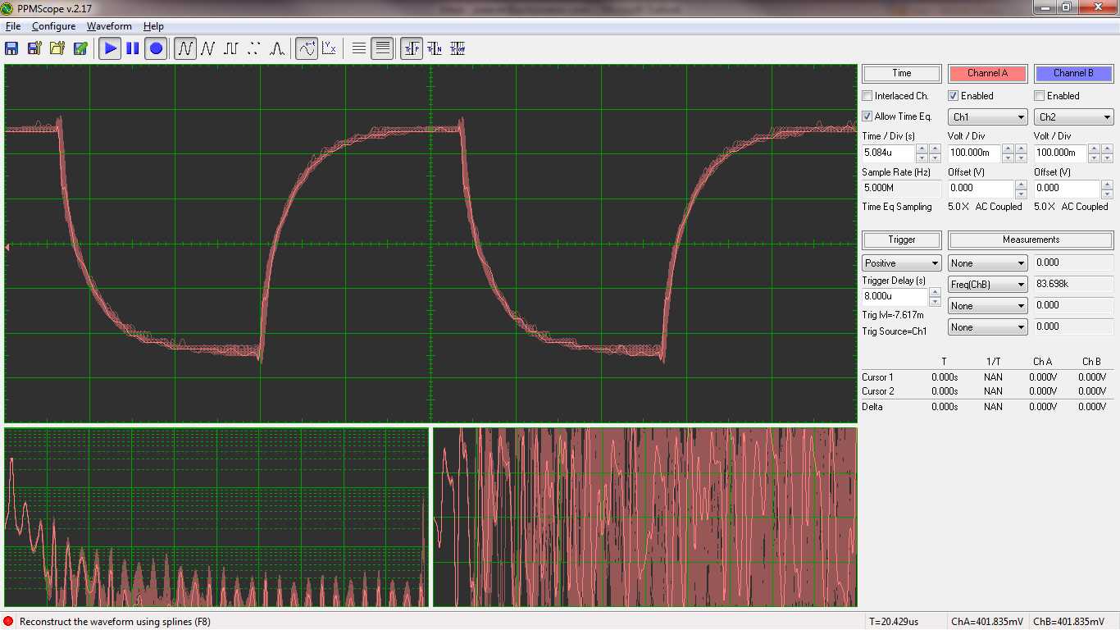
Pictures/High Res On Gain 5 Spline.jpg
