jonw0224/PPMScope/Pictures/IMG_0154.JPG

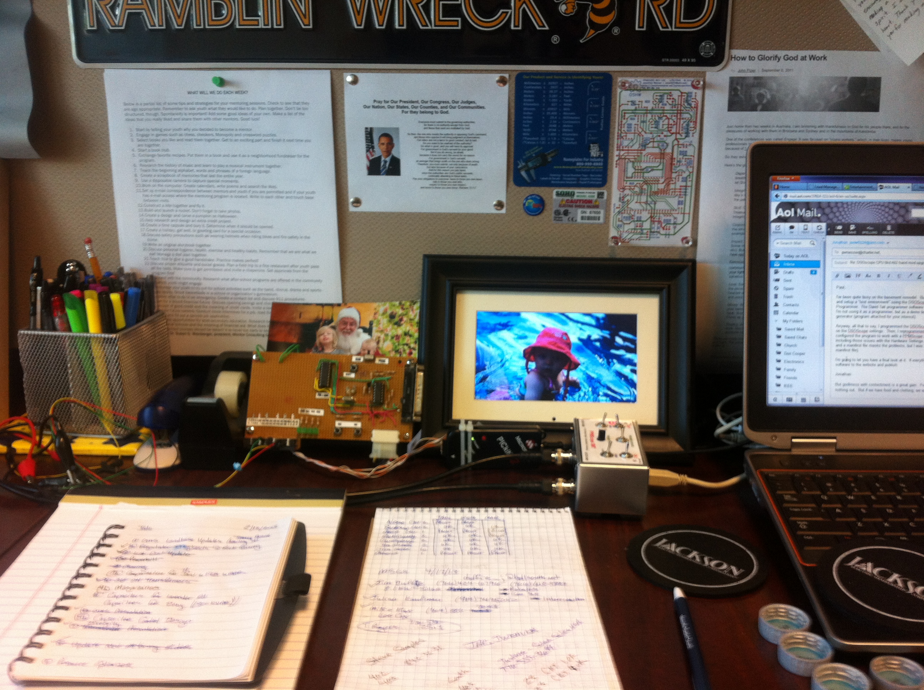
Pictures/IMG_0154.JPG
