jonw0224/PPMScope/Pictures/IMG_0191.JPG

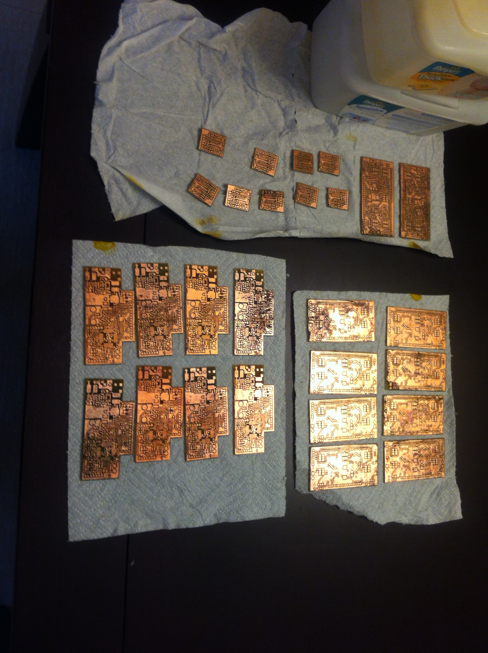
Pictures/IMG_0191.JPG
