jonw0224/PPMScope/Pictures/IMG_0192.JPG

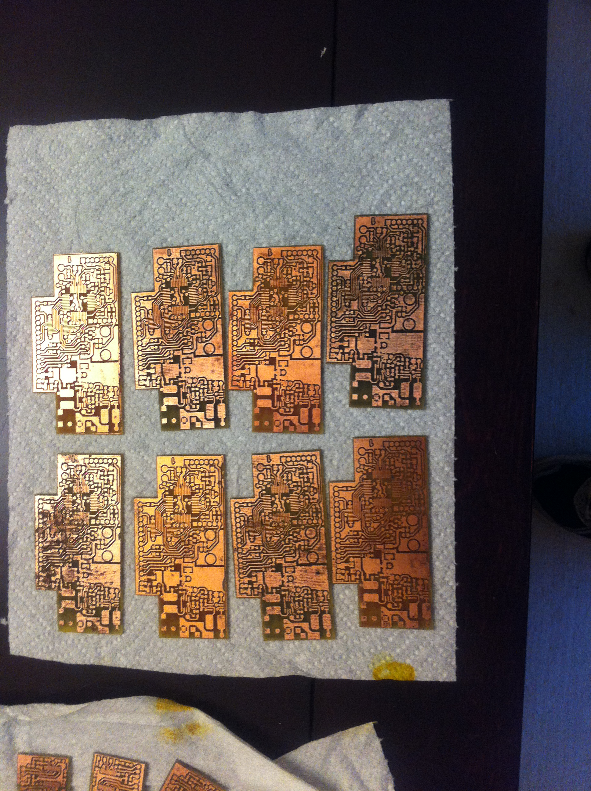
Pictures/IMG_0192.JPG
