jonw0224/PPMScope/Pictures/IMG_0193.JPG

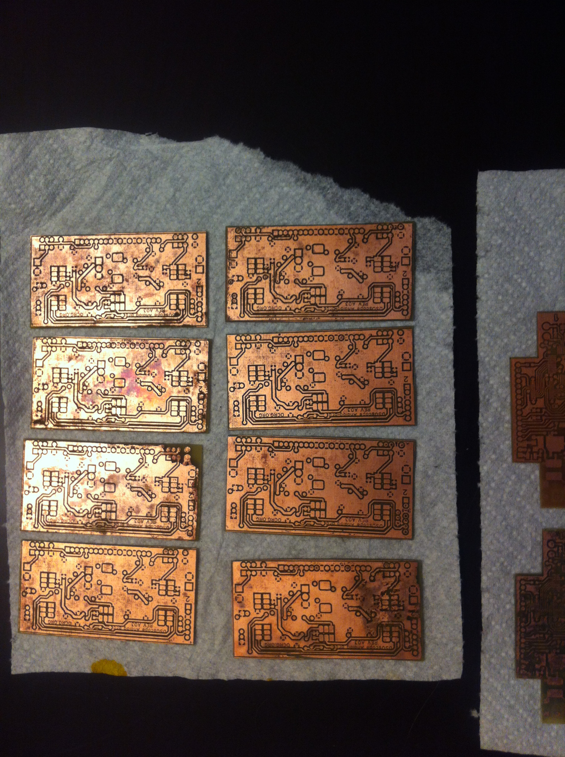
Pictures/IMG_0193.JPG
