jonw0224/PPMScope/Pictures/IMG_0194.JPG

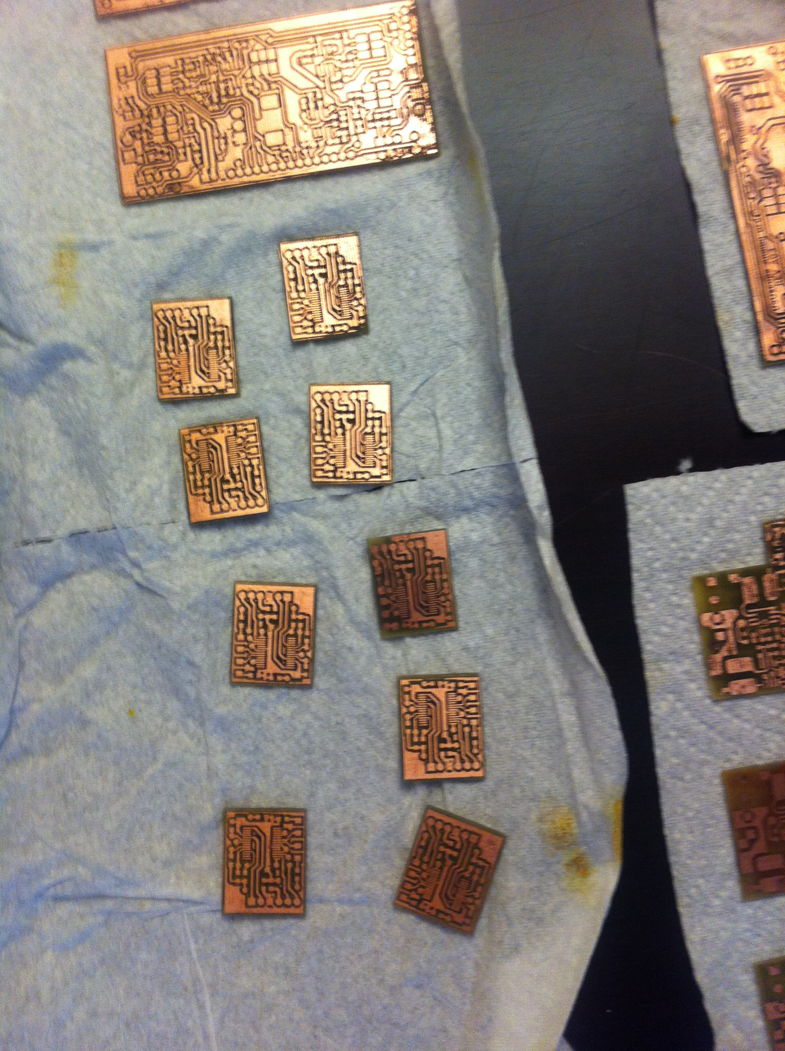
Pictures/IMG_0194.JPG
