jonw0224/PPMScope/Pictures/IMG_0195.JPG

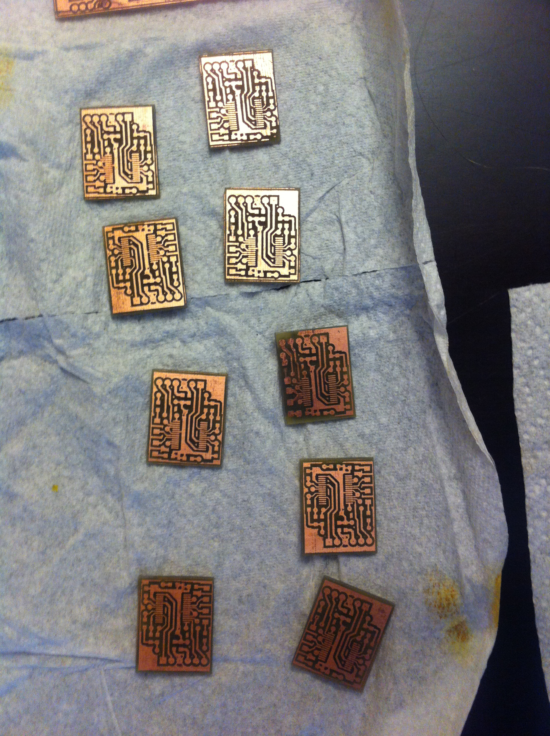
Pictures/IMG_0195.JPG
