jonw0224/PPMScope/Pictures/IMG_0230.JPG

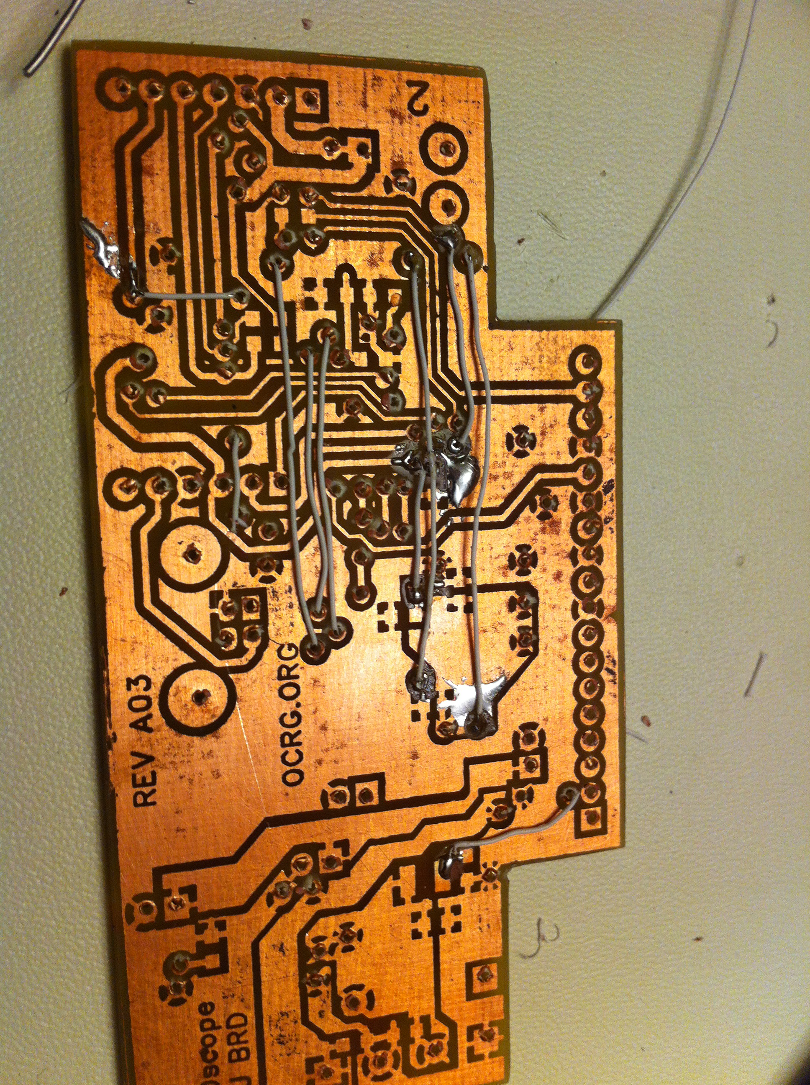
Pictures/IMG_0230.JPG
