jonw0224/PPMScope/Pictures/IMG_0278.JPG

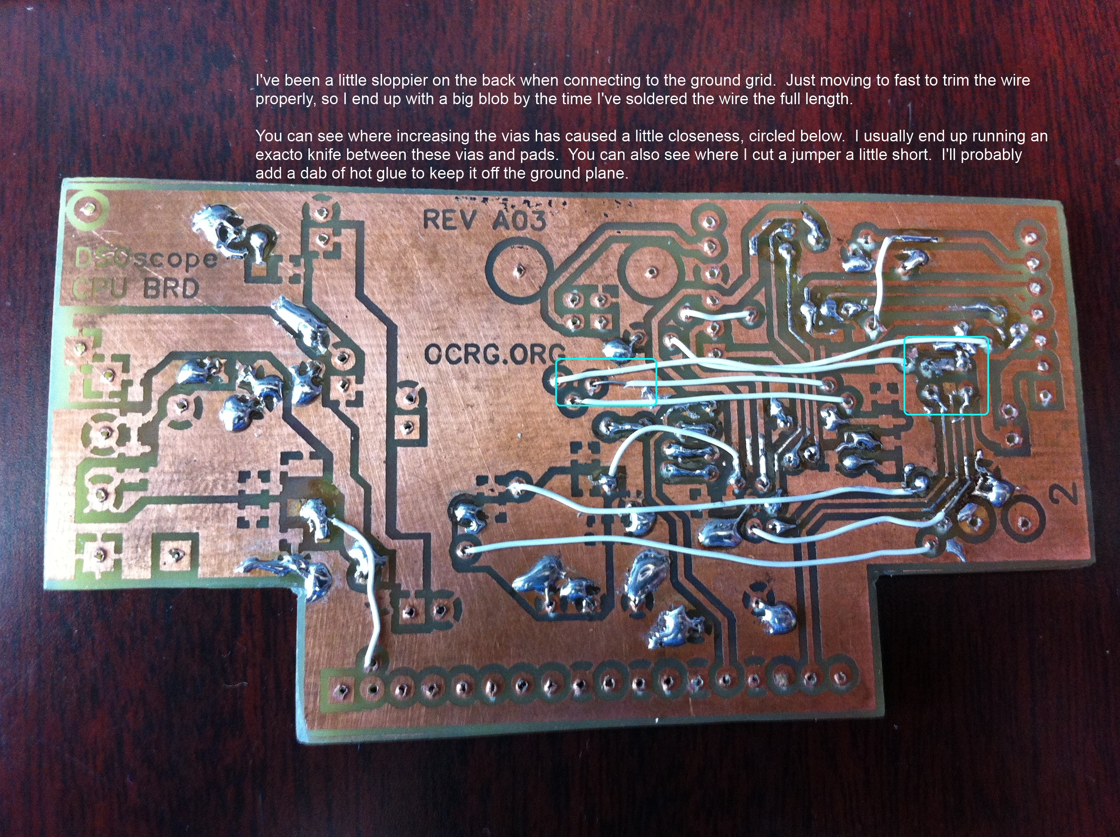
Pictures/IMG_0278.JPG
