jonw0224/PPMScope/Pictures/IMG_0279.JPG

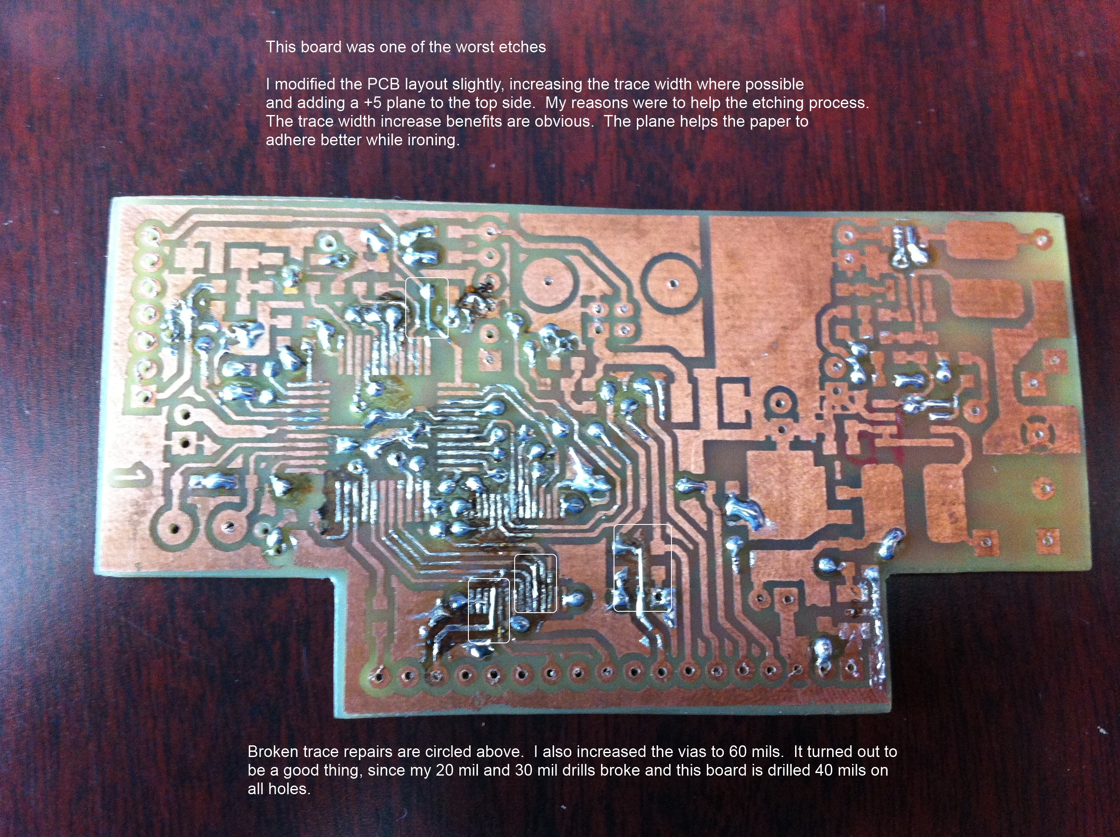
Pictures/IMG_0279.JPG
