jonw0224/PPMScope/Pictures/IMG_0402.JPG

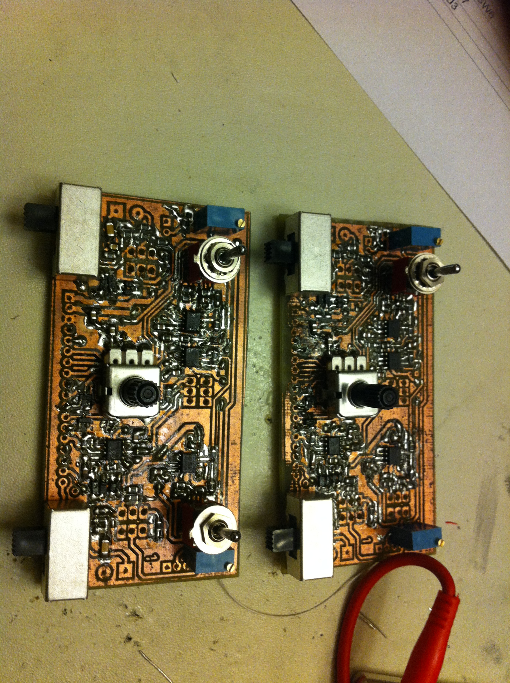
Pictures/IMG_0402.JPG
