jonw0224/PPMScope/Pictures/IvanAtlas1.jpg

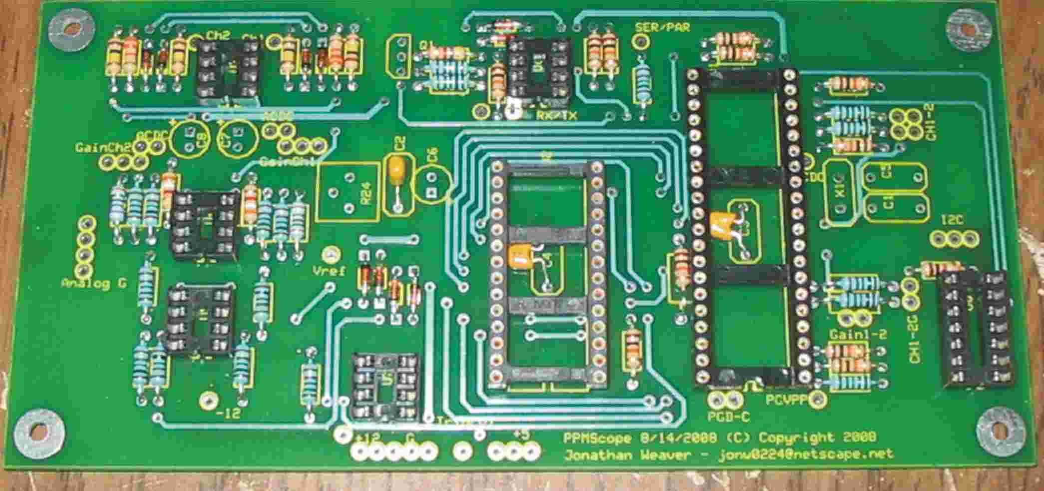
Pictures/IvanAtlas1.jpg
