jonw0224/PPMScope/Pictures/IvanAtlas2.jpg

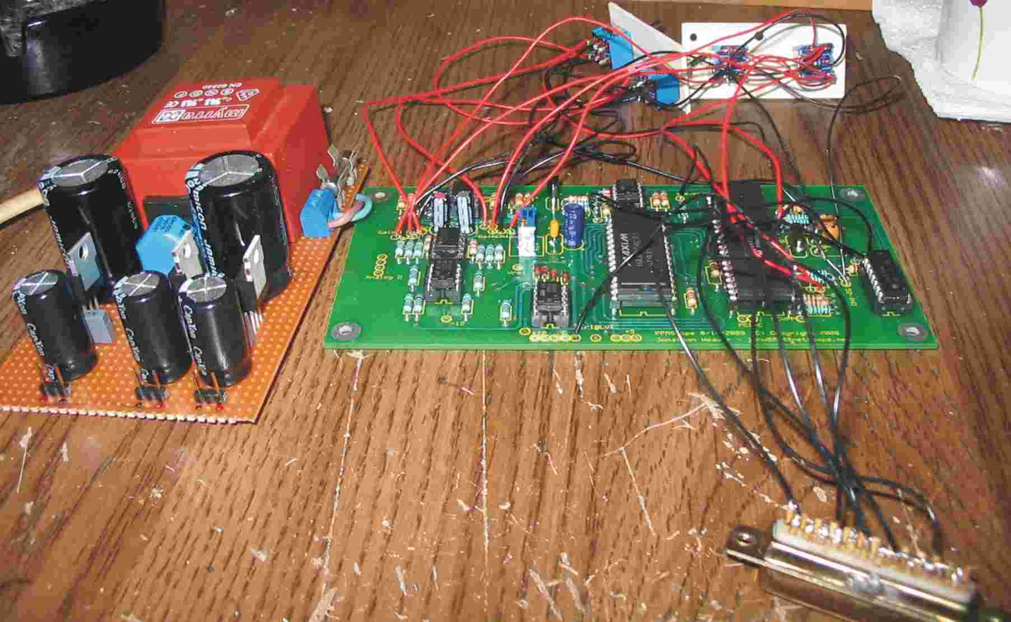
Pictures/IvanAtlas2.jpg
