jonw0224/PPMScope/Pictures/jonathanweaver1.JPG

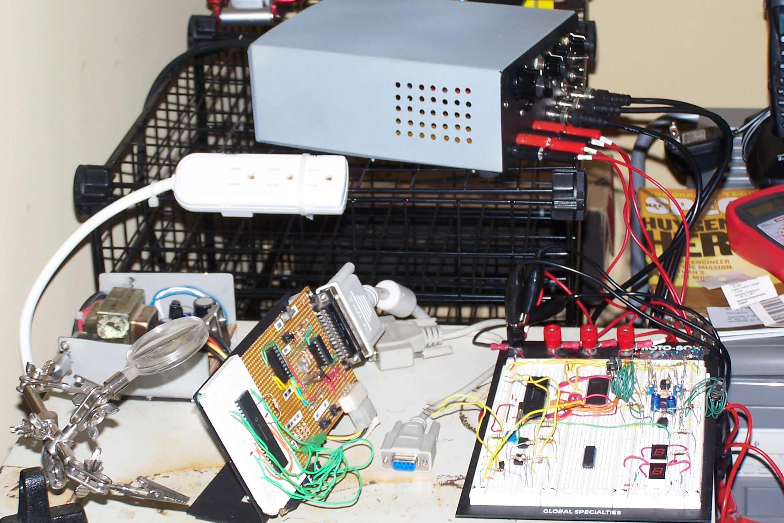
Pictures/jonathanweaver1.JPG
