jonw0224/PPMScope/Pictures/jonathanweaver3.jpg

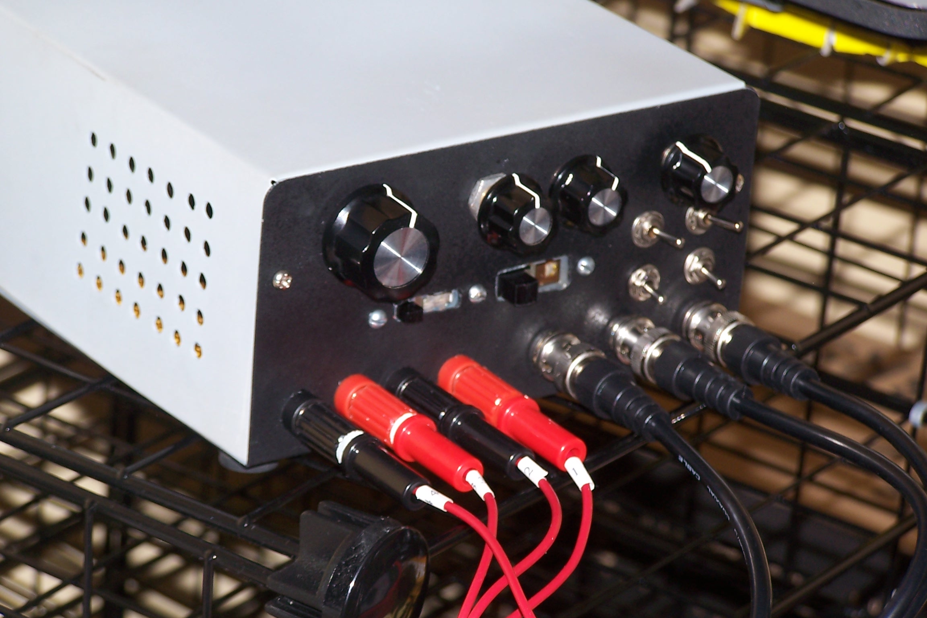
Pictures/jonathanweaver3.jpg
