jonw0224/PPMScope/Pictures/jonathanweaver4.jpg

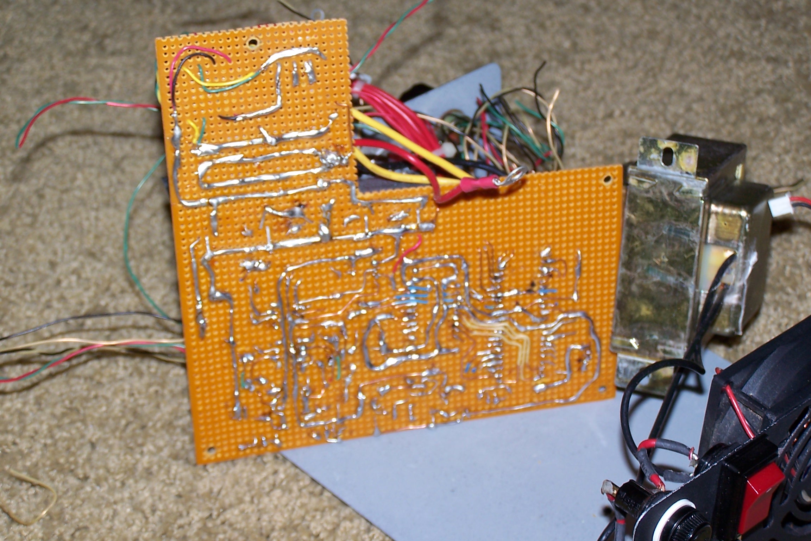
Pictures/jonathanweaver4.jpg
