jonw0224/PPMScope/Pictures/jonathanweaver5.jpg

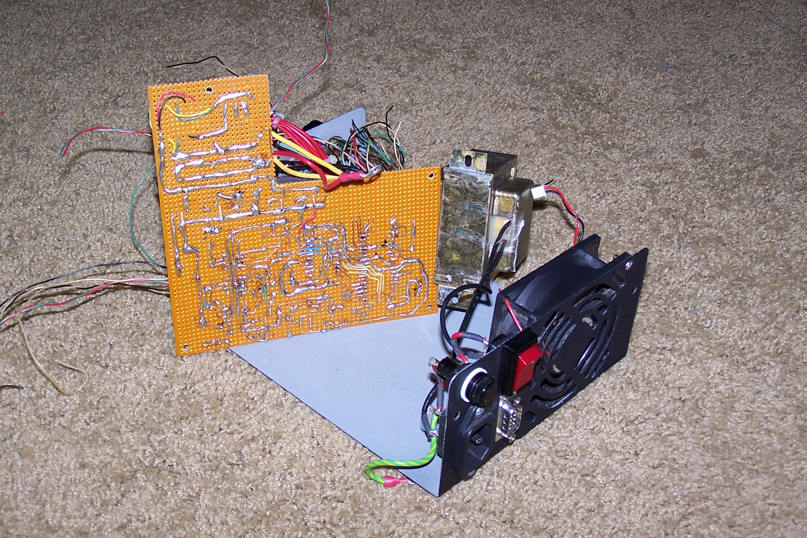
Pictures/jonathanweaver5.jpg
