jonw0224/PPMScope/Pictures/jonathanweaver6.jpg

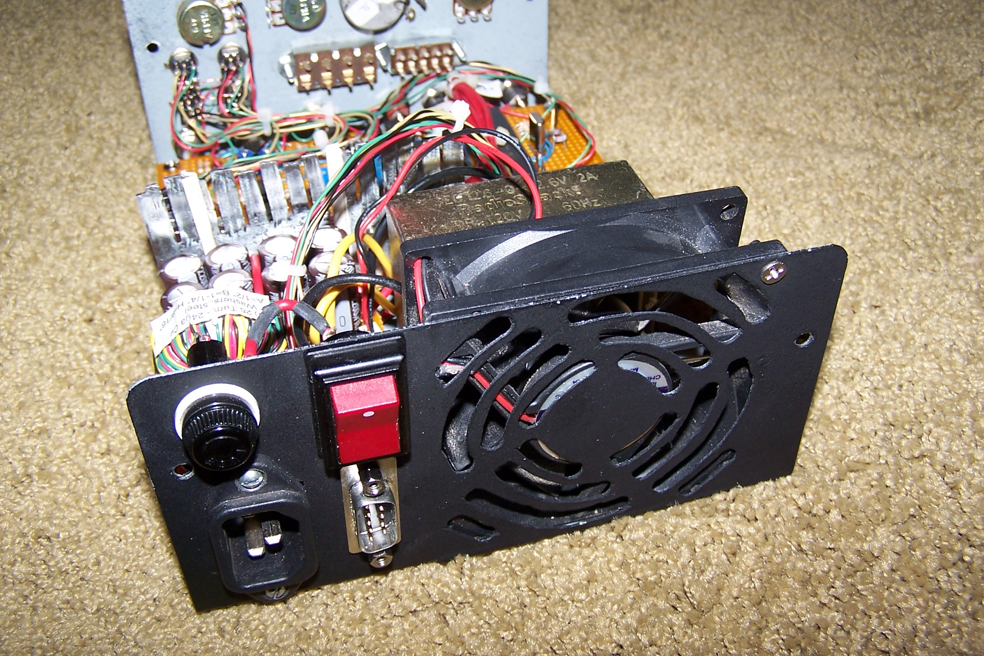
Pictures/jonathanweaver6.jpg
