jonw0224/PPMScope/Pictures/jonathanweaver8.jpg

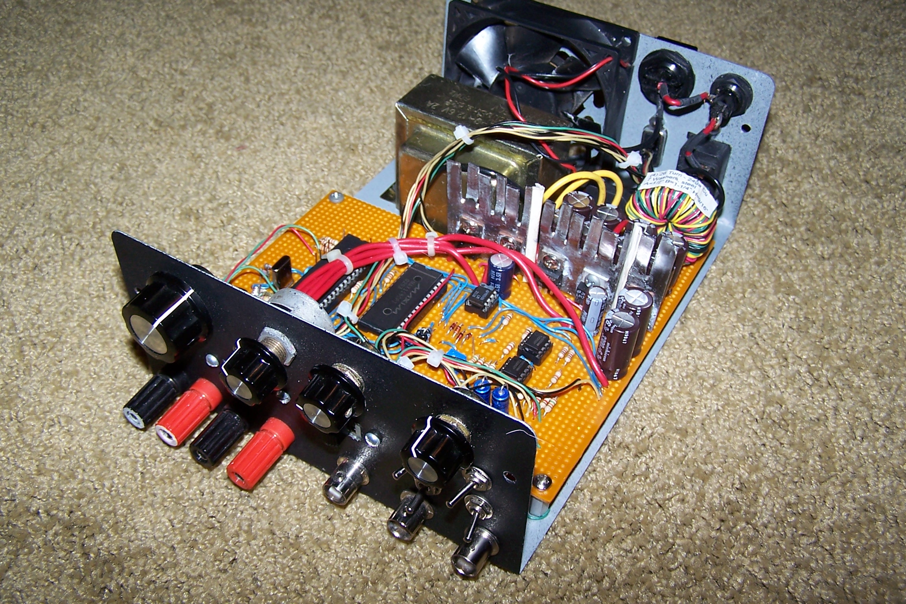
Pictures/jonathanweaver8.jpg
