jonw0224/PPMScope/Pictures/jonathanweaver9.jpg

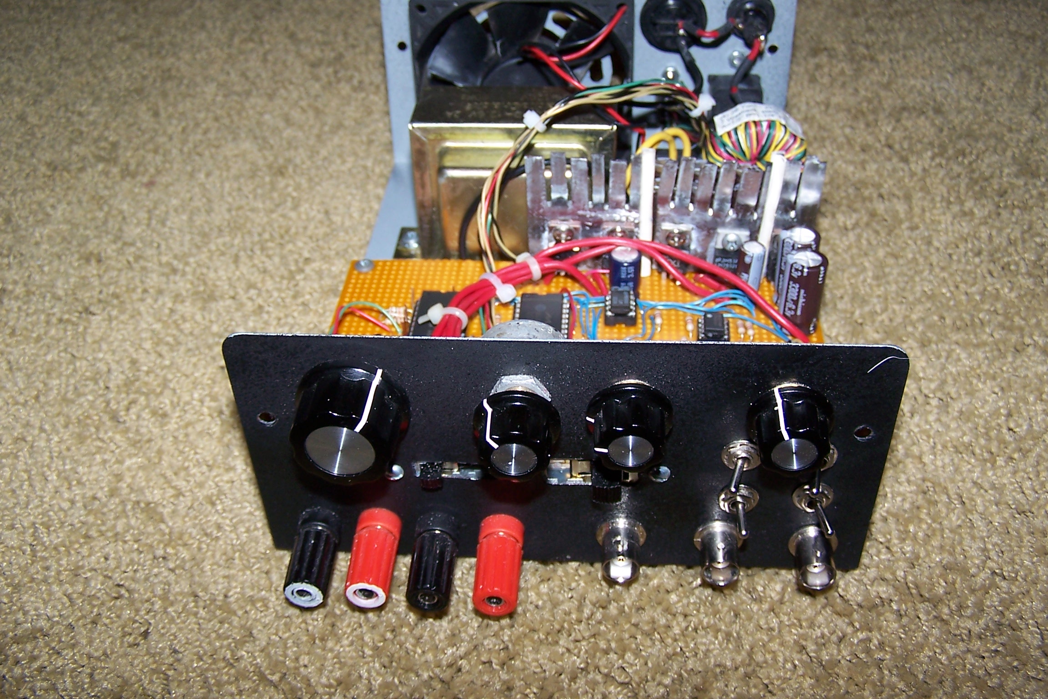
Pictures/jonathanweaver9.jpg
