jonw0224/PPMScope/Pictures/karolysimon1.JPG

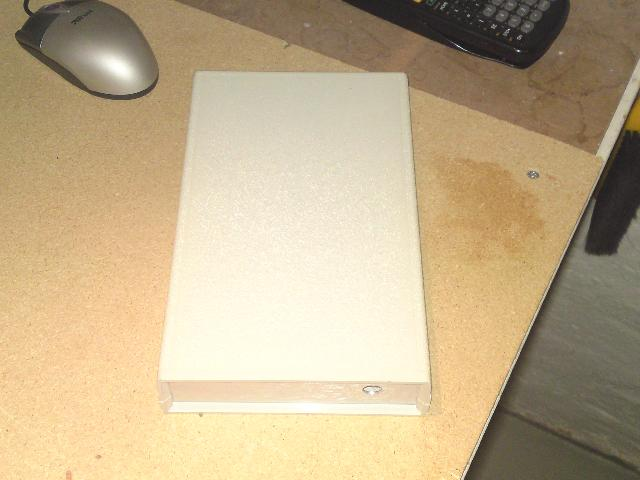
Pictures/karolysimon1.JPG
