jonw0224/PPMScope/Pictures/karolysimon2.jpg

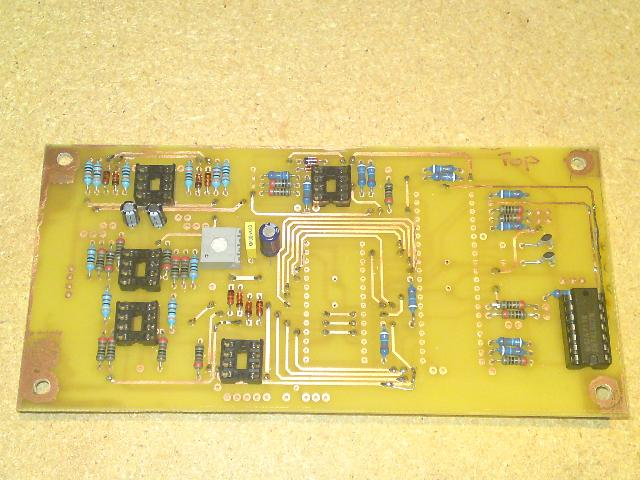
Pictures/karolysimon2.jpg
