jonw0224/PPMScope/Pictures/karolysimon4.jpg

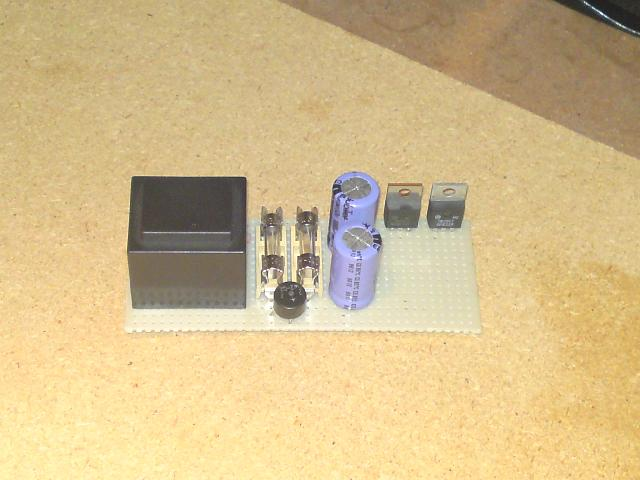
Pictures/karolysimon4.jpg
