jonw0224/PPMScope/Pictures/karolysimon5.JPG

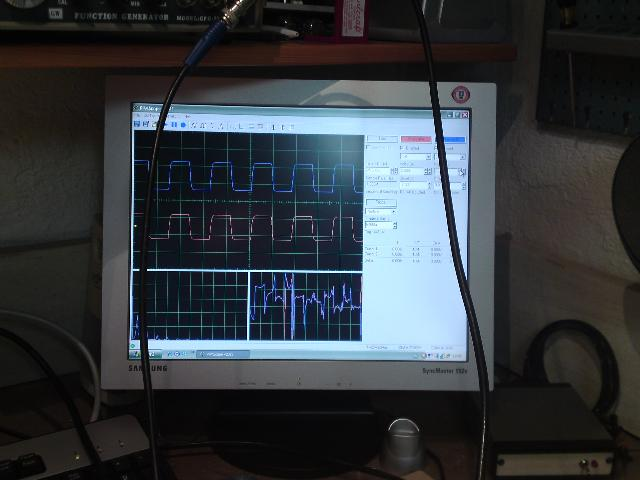
Pictures/karolysimon5.JPG
