jonw0224/PPMScope/Pictures/karolysimon6.JPG

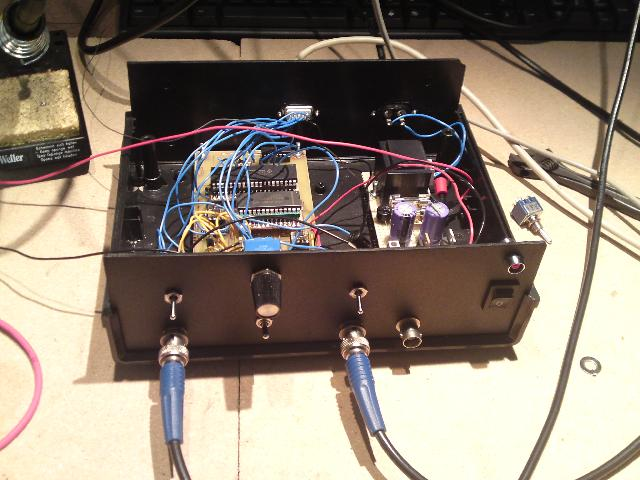
Pictures/karolysimon6.JPG
