jonw0224/PPMScope/Pictures/karolysimon7.jpg

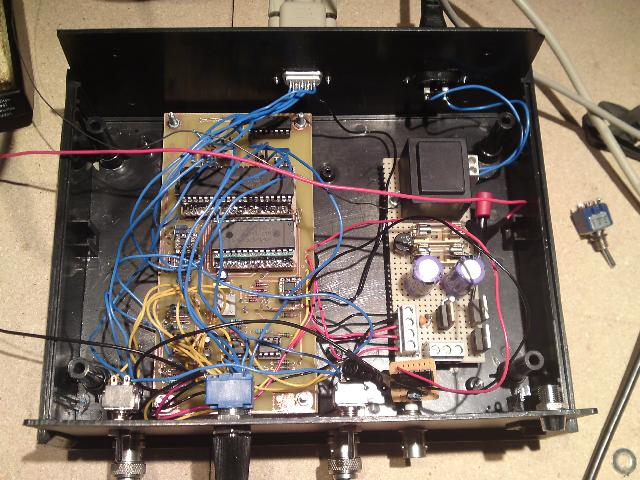
Pictures/karolysimon7.jpg
