jonw0224/PPMScope/Pictures/karolysimon8.jpg

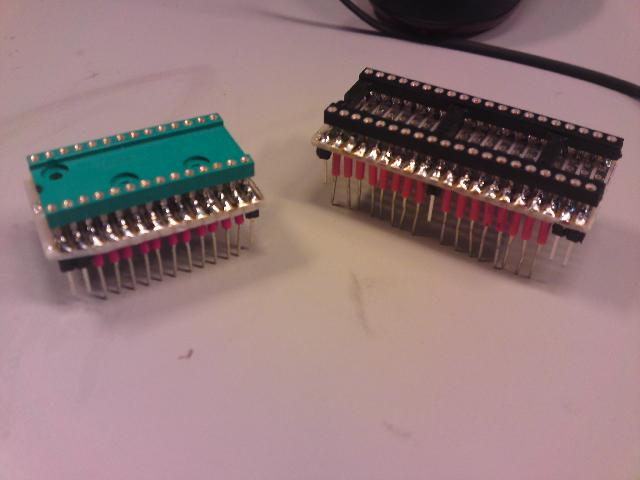
Pictures/karolysimon8.jpg
