jonw0224/PPMScope/Pictures/karolysimon9.jpg

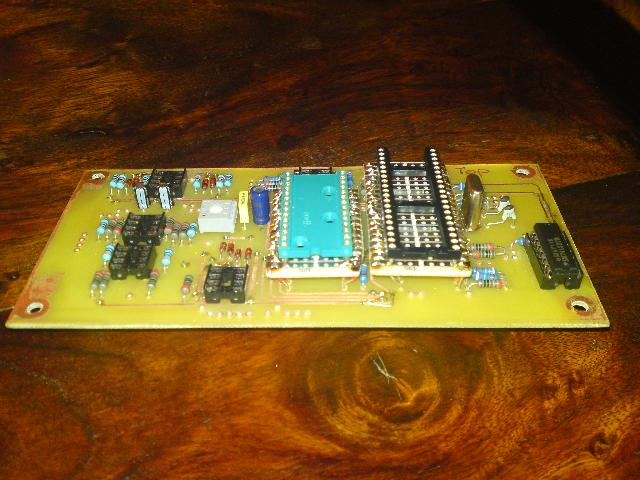
Pictures/karolysimon9.jpg
