jonw0224/PPMScope/Pictures/Mark Burton 2013118.JPG

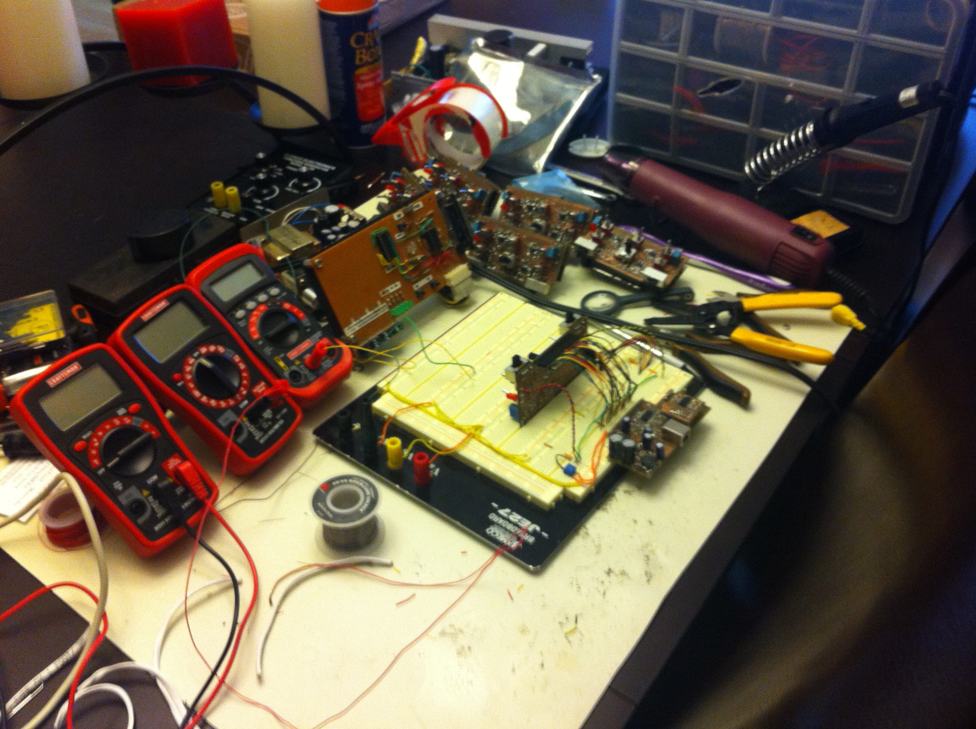
Pictures/Mark Burton 2013118.JPG
