jonw0224/PPMScope/Pictures/Mark Burton 20131015 083042.jpg

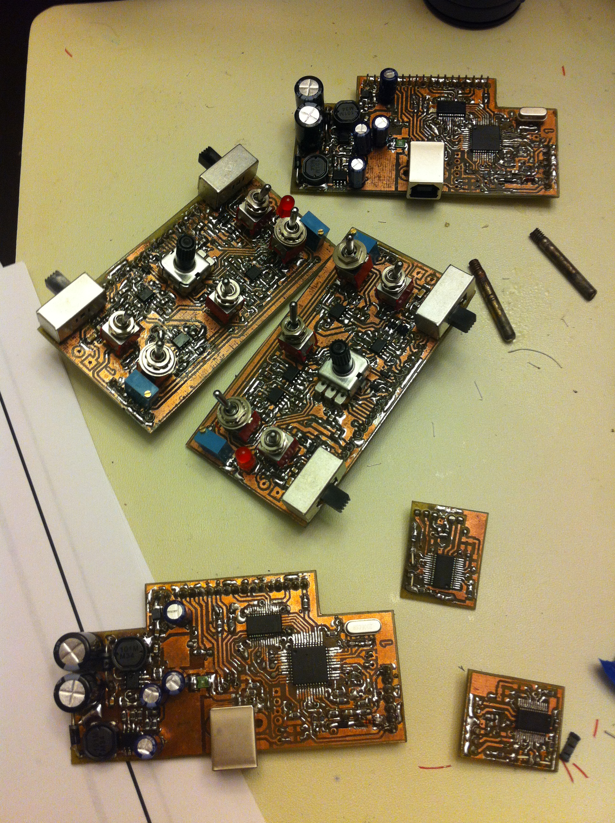
Pictures/Mark Burton 20131015 083042.jpg
