jonw0224/PPMScope/Pictures/Mark Burton 20131015 083113.jpg

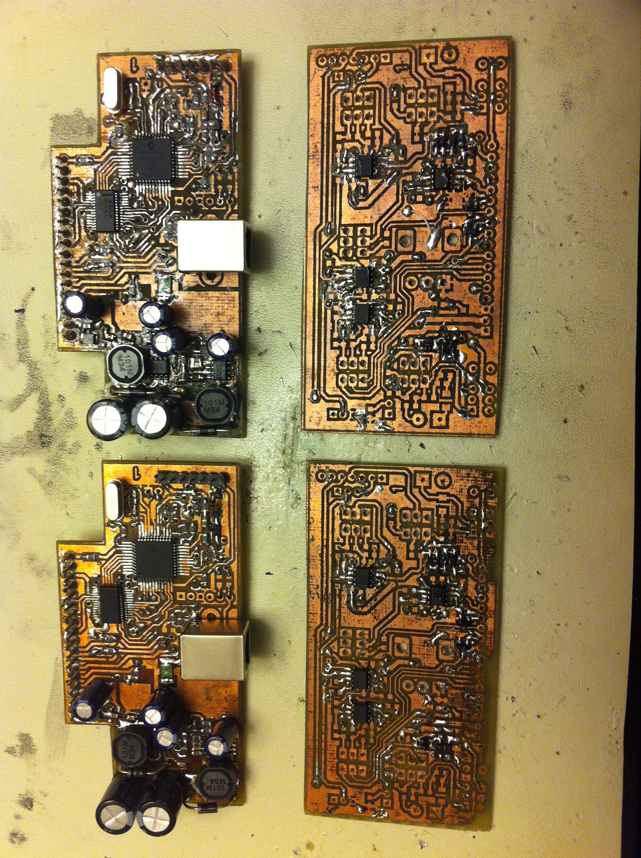
Pictures/Mark Burton 20131015 083113.jpg
