jonw0224/PPMScope/Pictures/Mark Burton 20131015 083131.jpg

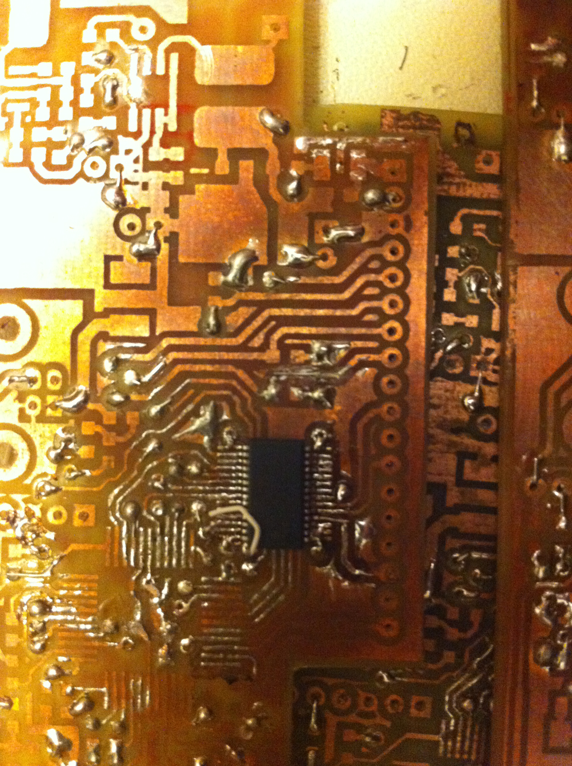
Pictures/Mark Burton 20131015 083131.jpg
