jonw0224/PPMScope/Pictures/Mark Burton 20131015 083154.jpg

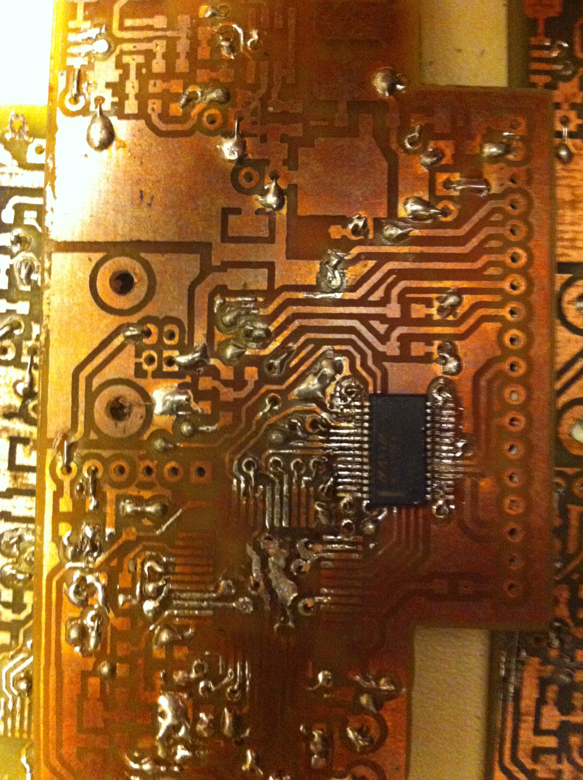
Pictures/Mark Burton 20131015 083154.jpg
