jonw0224/PPMScope/Pictures/photo.JPG

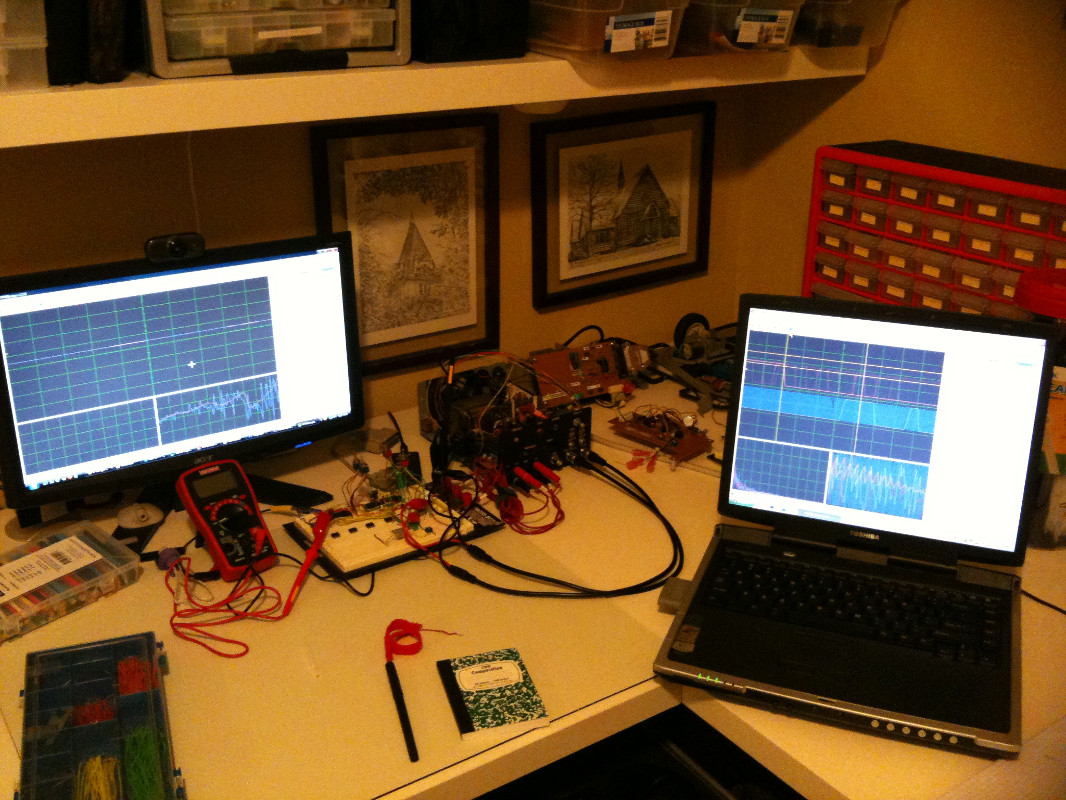
Pictures/photo.JPG
