jonw0224/PPMScope/Pictures/PPMScope on Fedora.PNG

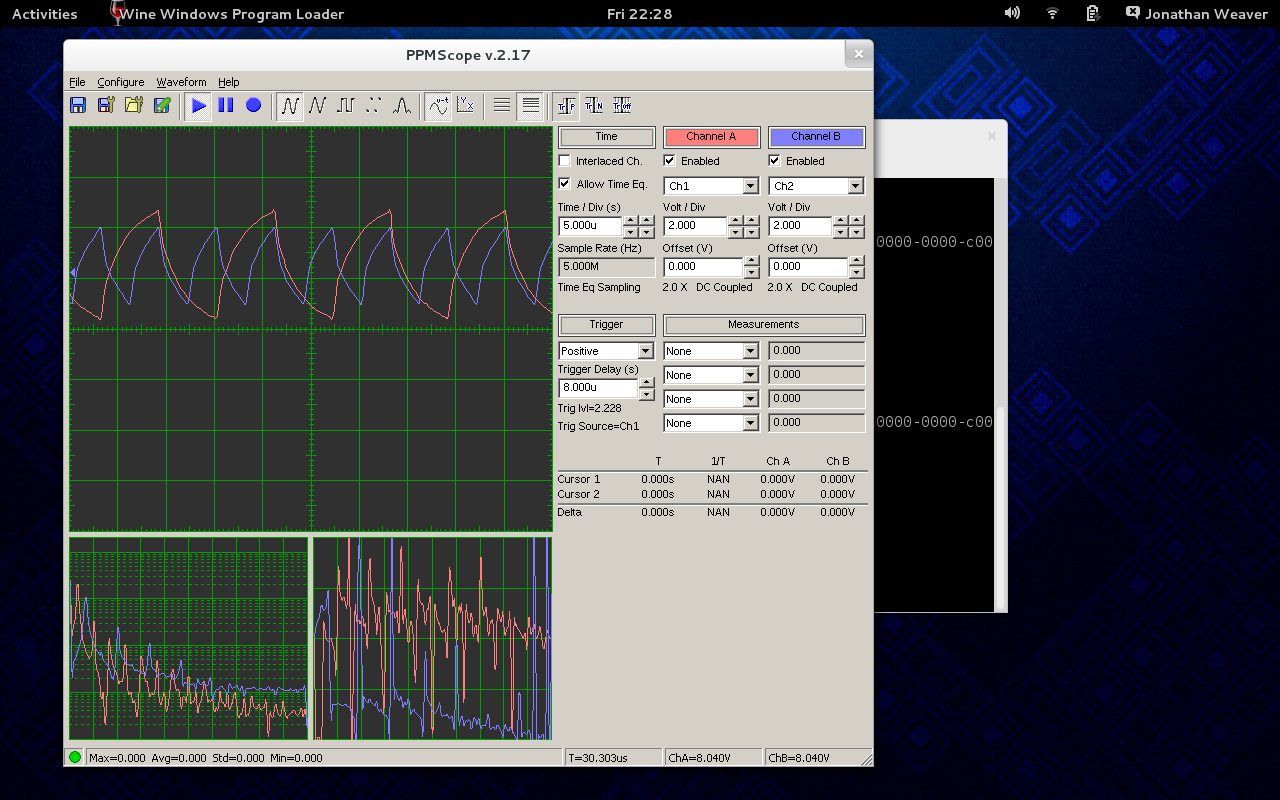
Pictures/PPMScope on Fedora.PNG
