jonw0224/PPMScope/Pictures/ScopeProg1.jpg

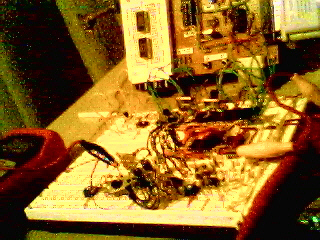
Pictures/ScopeProg1.jpg
