jonw0224/PPMScope/Pictures/TiagoRocha1.jpg

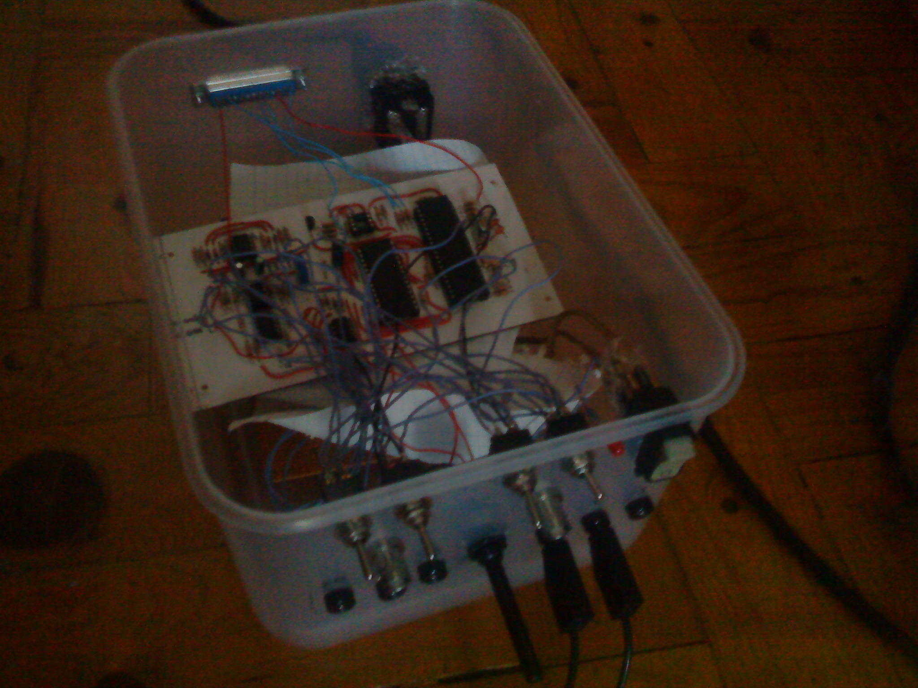
Pictures/TiagoRocha1.jpg
