jonw0224/PPMScope/Pictures/TiagoRocha2.JPG

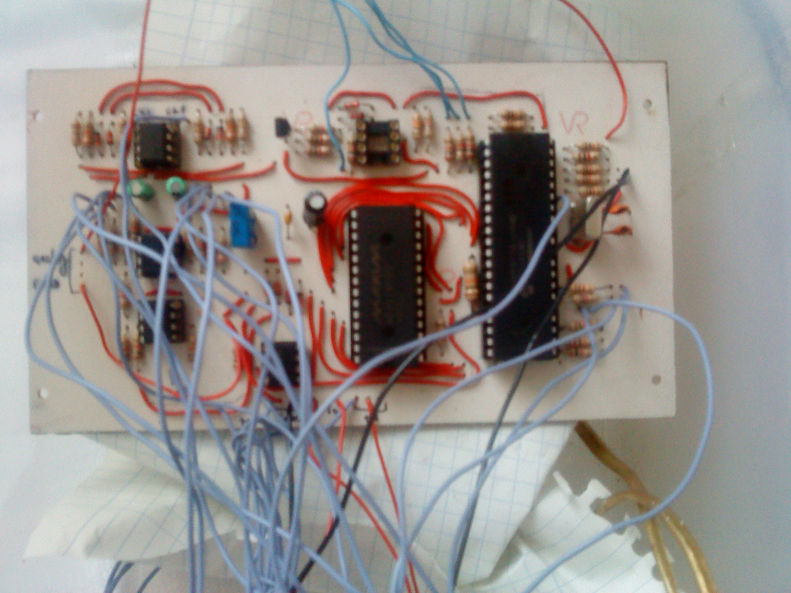
Pictures/TiagoRocha2.JPG
