jonw0224/PPMScope/PCsource/Help/testa.jpg

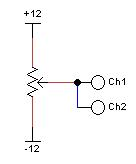
PCsource/Help/testa.jpg
