jonw0224/PPMScope/PCsource/Help/testb.jpg

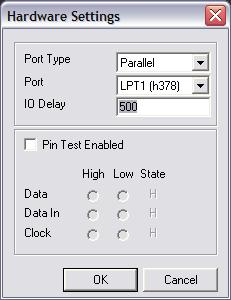
PCsource/Help/testb.jpg
