jonw0224/PPMScope/PCsource/Help/testc.jpg

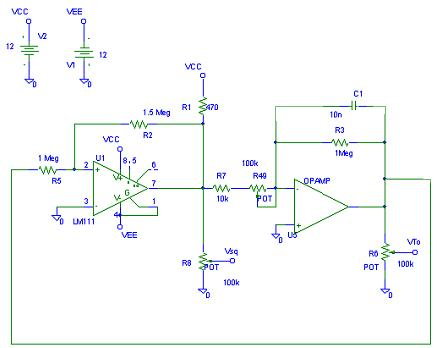
PCsource/Help/testc.jpg
