jonw0224/PPMScope/Pictures/PPMScope_SW_Debug_20130606_1.jpg

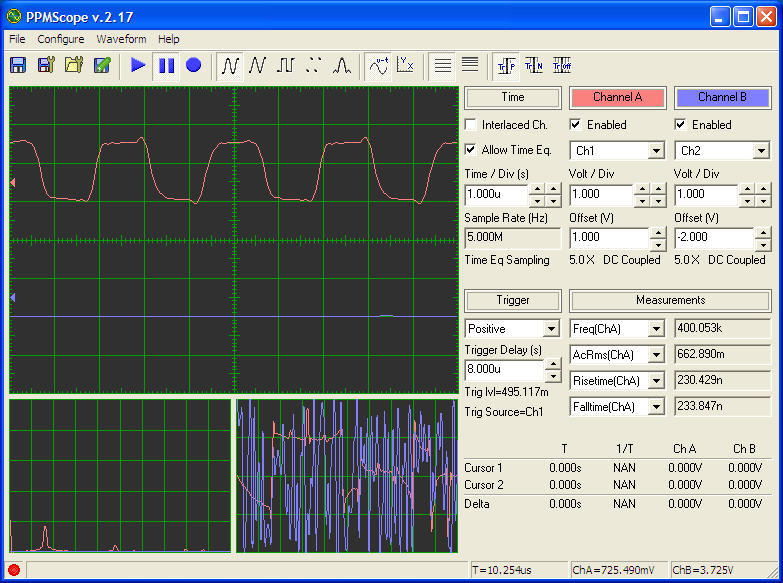
Pictures/PPMScope_SW_Debug_20130606_1.jpg
