jonw0224/PPMScope/Contributions/Paul Messer/DSOscope_A02/Schematic/A02/DSOscope_USBBrd_A02.pdf

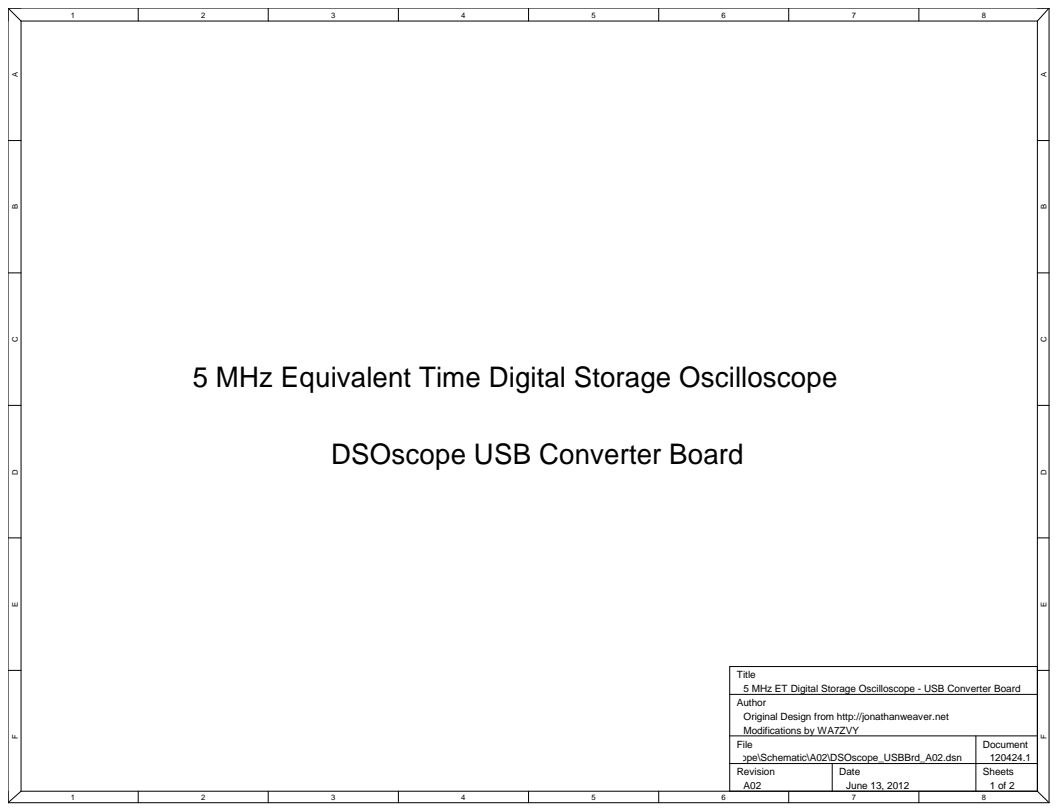
[picture p147: page 1]

5 MHz Equivalent Time Digital Storage Oscilloscope

DSOscope USB Converter Board

Title
5 MHz ET Digital Storage Oscilloscope - USB Converter Board
Author
Original Design from http://jonathanweaver.net
Modifications by WA7ZVY

File USBBrd_A02.dsn | Document 120424.1

Revision A02 | Date June 13, 2012 | Sheets 1 of 2

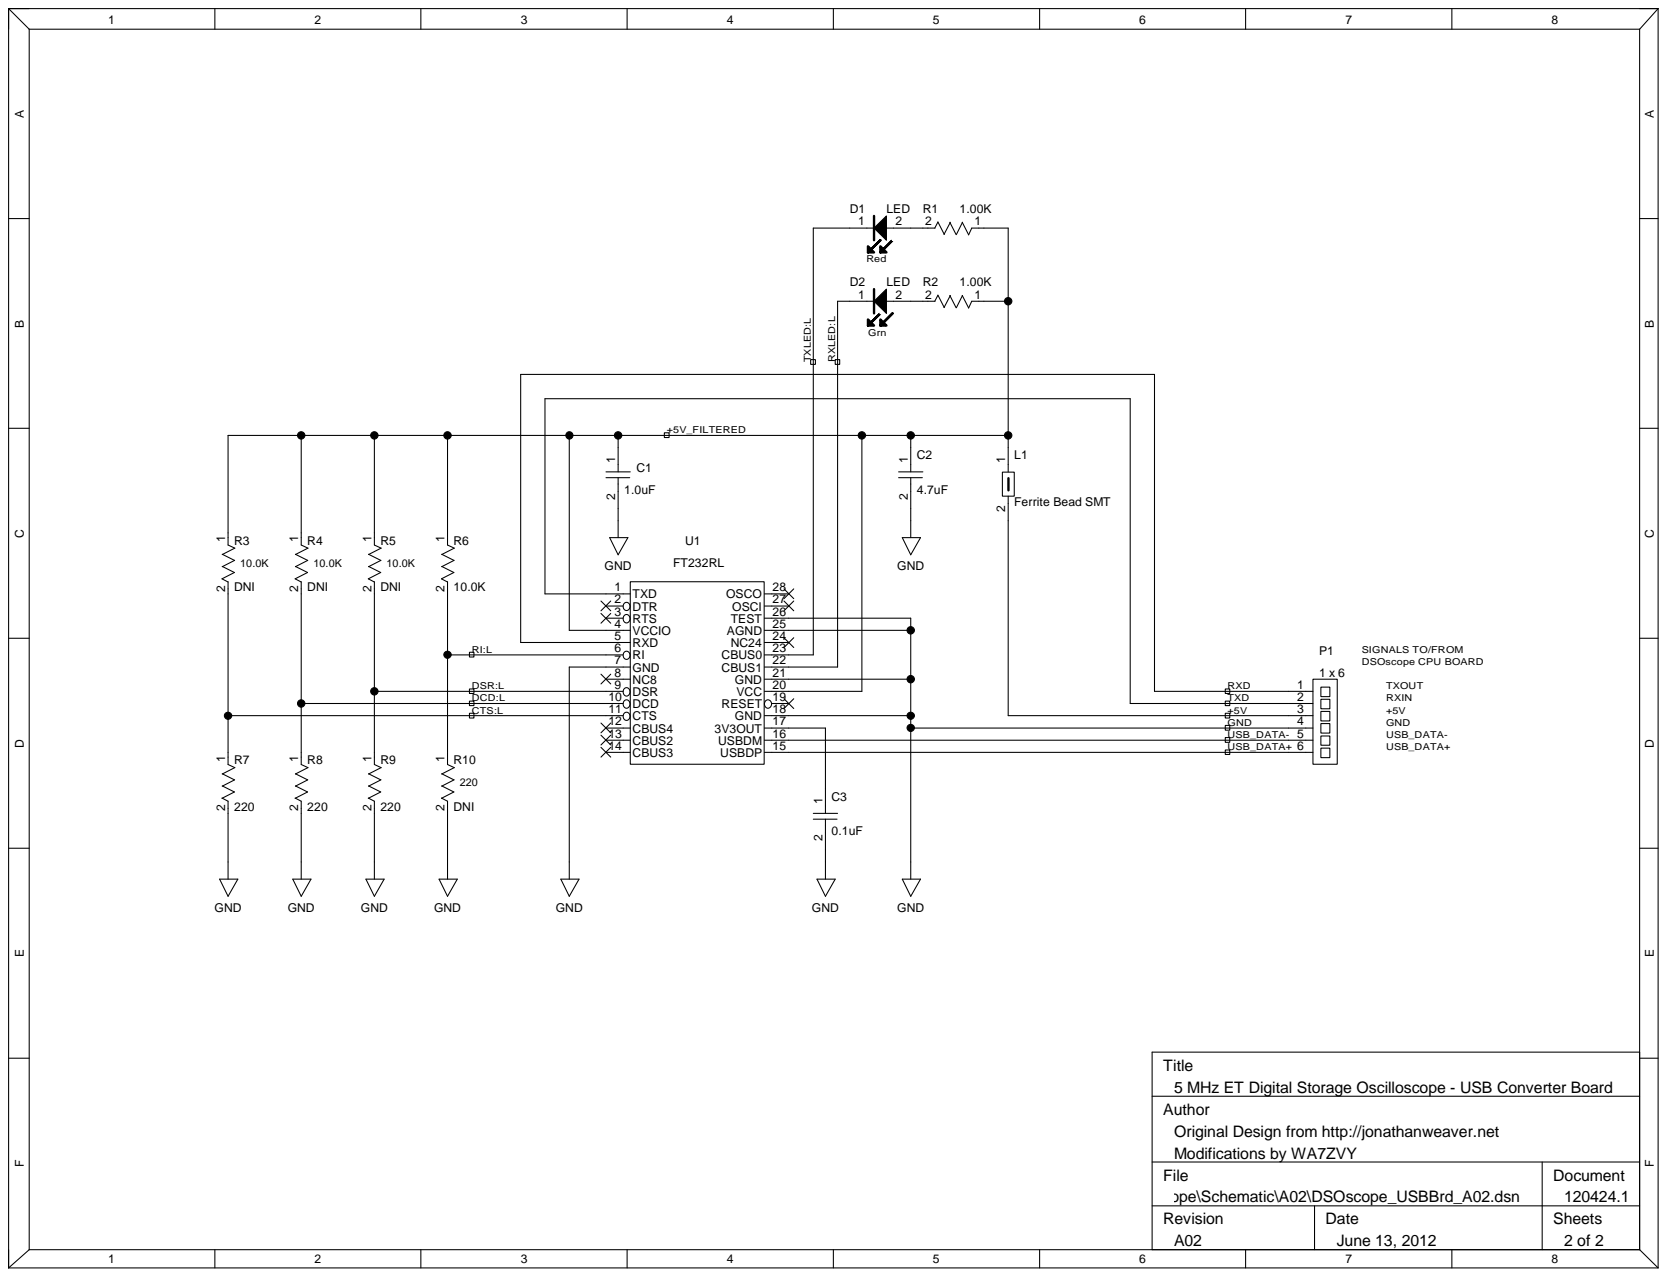
[picture p148: page 2]

+5V_FILTERED

GND

DCD:L
CTS:L

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

File USBBrd_A02.dsn | Document 120424.1

Revision A02 | Date June 13, 2012 | Sheets 2 of 2
