jonw0224/PPMScope/Contributions/Paul Messer/DSOscope_A03/DSOscope_Rev_A03_20130113/Mechanical/A03/CAB-PCB.pdf

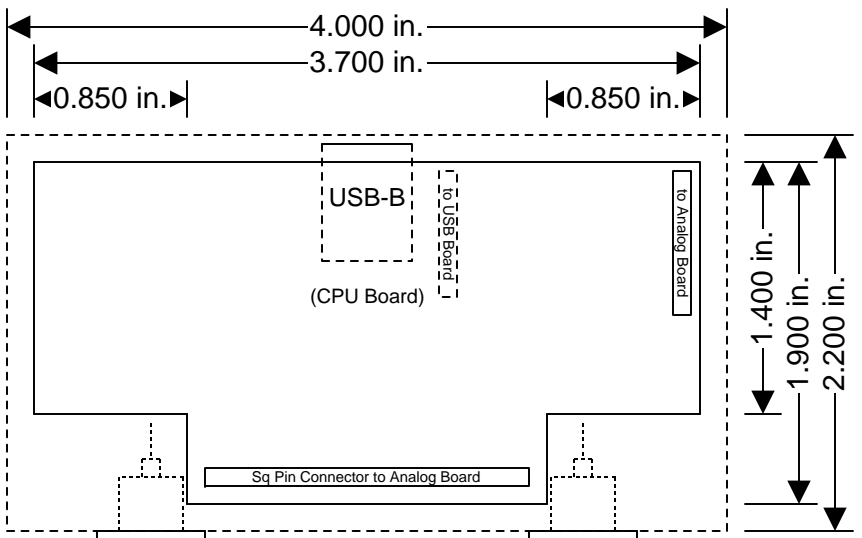
[picture p149: figure]
Sq Pin Connector to Analog Board; (CPU Board); USB-B; to USB Board; to Analog Board

Cabinet = Hammond 1411GU, DigiKey P/N = HM609-ND. Cabinet size is 4" wide x 2.2" deep x 1.6" high.

Analog Board has the switches directly soldered to the PCB. The individual switch bushings and nuts are then used to mount the Analog Board to the cabinet top panel.

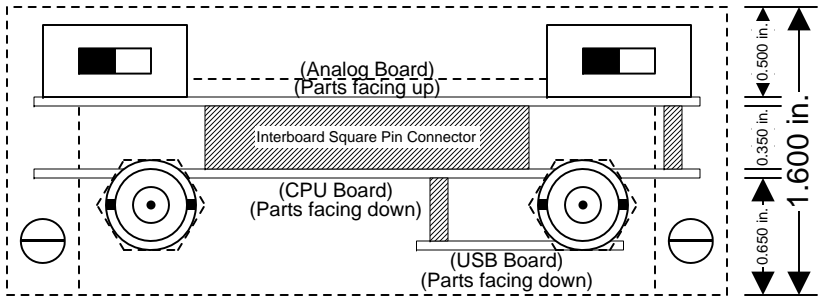
[picture p150: figure]
(Analog Board); (CPU Board); (Parts facing down); (Parts facing up); Interboard Square Pin Connector; (USB Board) (Parts facing down)

The BNC connectors are bolted to the cabinet front panel and
a short length wire/coax connects them to the Analog Board.

The CPU Board plugs into the Analog Board with an 18 pin square pin connector/header and a 7 pin square pin connector/header and is located parallel and below the Analog Board. Components on the CPU PCB face downward.

The USB Board plugs into the CPU Board with a 6 pin square pin connector/header and is located parallel and below
the CPU Board. Components on the USB PCB face downward.
Checked by: | Date: | Size: | Revision:

Mechanical Designer:

# DSOscope

## Circuit Board and Cabinet Configuration

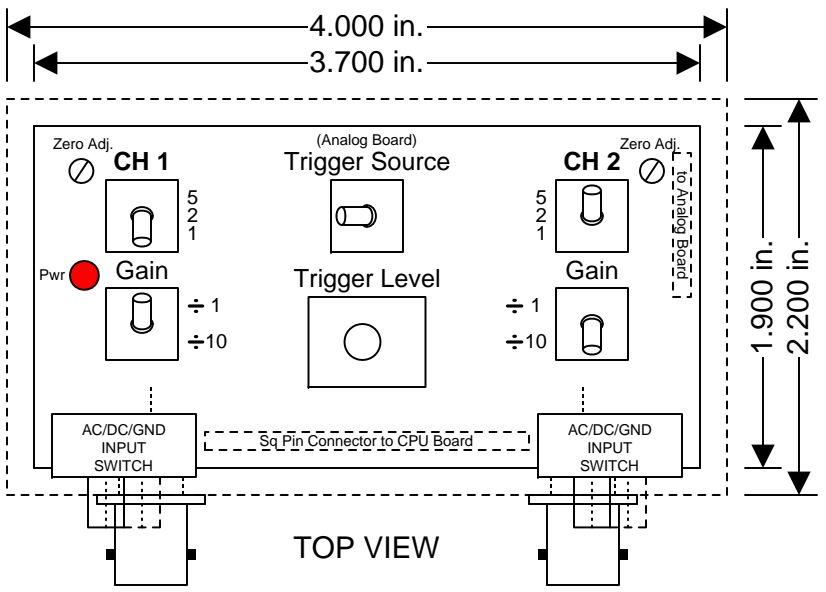
[picture p151: figure]
Sq Pin Connector to CPU Board; Gain; Zero Adj.; Pwr; (Analog Board); Trigger Source; Trigger Level; TOP VIEW; AC/DC/GND INPUT SWITCH; to Analog Board

Jan. 12, 2013 | A | A03 DOC MECH | Page: 1 of 4 Scale: 1 : 1
1 | 2 | 3 | 4 | 5

D

C

B

A

D

C

B

Electrical Designer: | A

## FRONT VIEW

WA7ZVY | WA7ZVY

## LEVEL 2 VIEW

Electrical design based upon the original
design work of Jonathan Weaver.
http://jonathanweaver.net/ppmscope.html | WA7ZVY

4.000 in.

0.750 in.

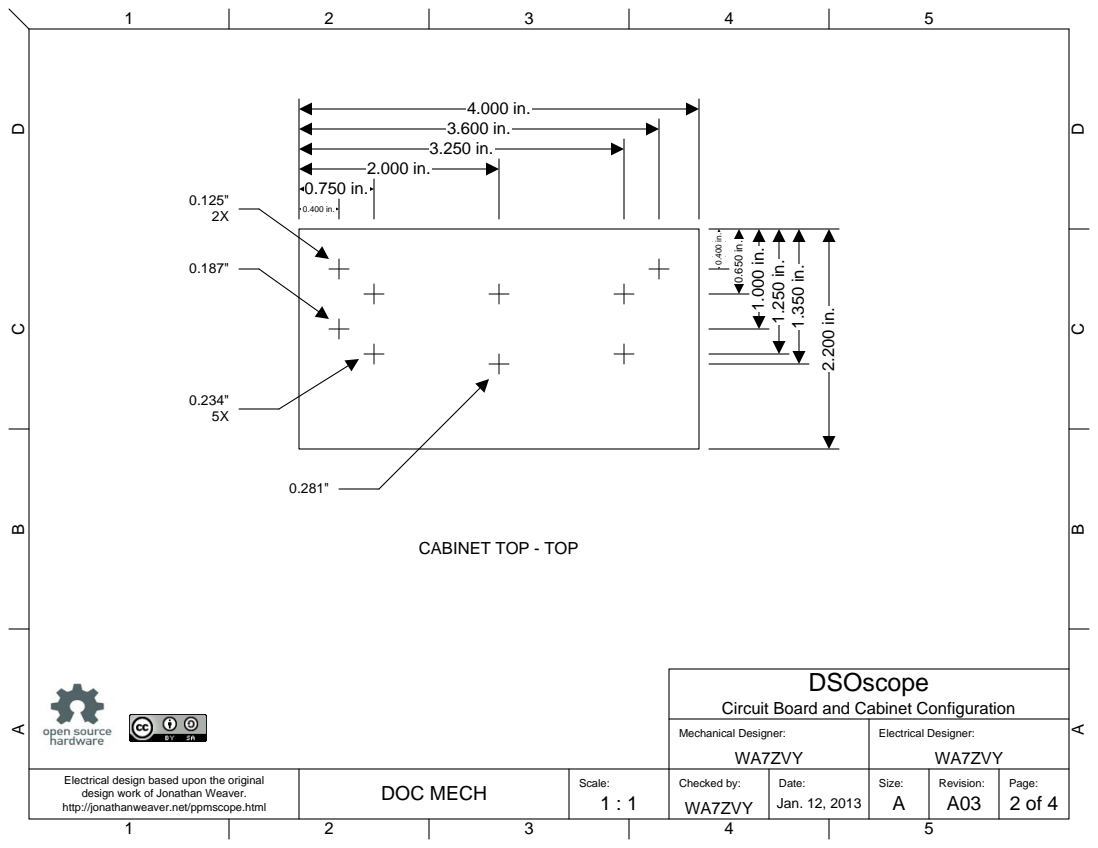
[picture p152: page 2]
Mechanical Designer:; DSOscope; Jan. 12, 2013; A03 DOC MECH; Page: 2 of 4 Scale: 1 : 1; Electrical Designer:; WA7ZVY

CABINET TOP - TOP

Circuit Board and Cabinet Configuration

http://jonathanweaver.net/ppmscope.html

3.900 in.

0.800 in.

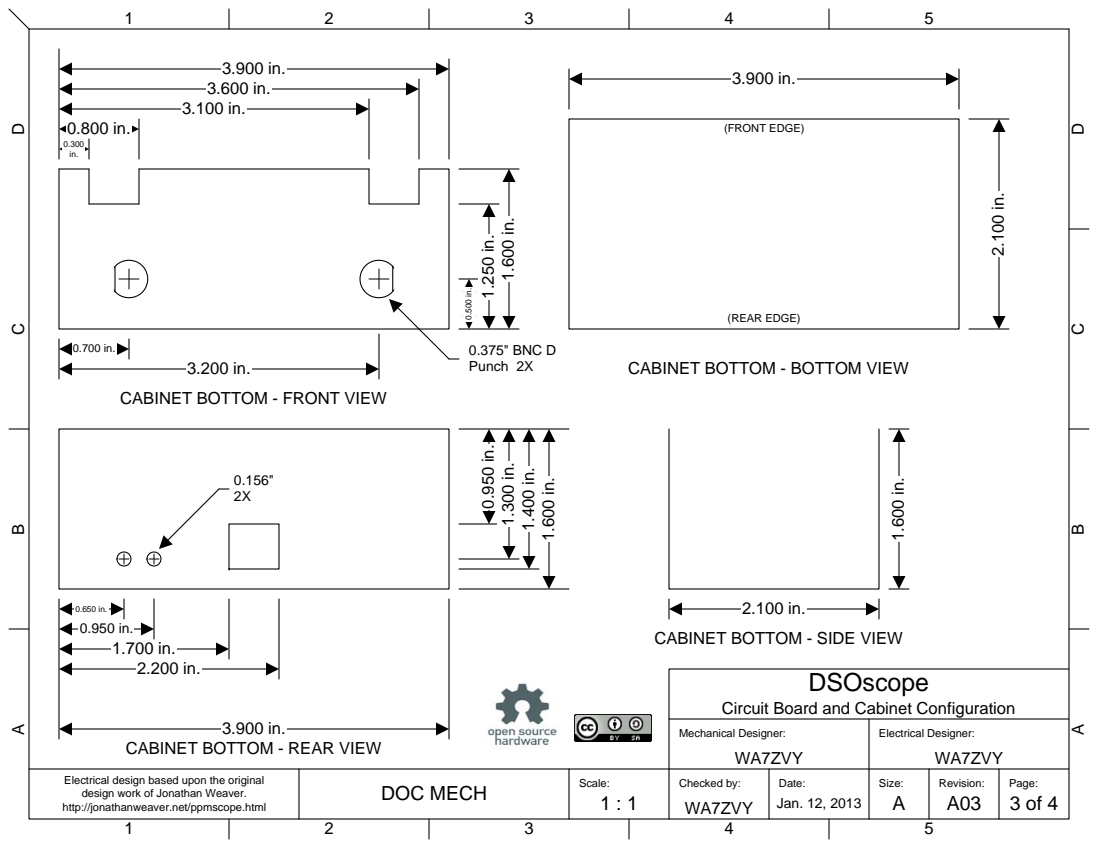
[picture p153: page 3]
Mechanical Designer:; DSOscope; Jan. 12, 2013; A03 DOC MECH; Page: 3 of 4 Scale: 1 : 1; Electrical Designer:; WA7ZVY; 0.375" BNC D Punch 2X; (FRONT EDGE); (REAR EDGE)

CABINET BOTTOM - BOTTOM VIEW

CABINET BOTTOM - FRONT VIEW

CABINET BOTTOM - SIDE VIEW

Circuit Board and Cabinet Configuration

CABINET BOTTOM - REAR VIEW

3.700 in.

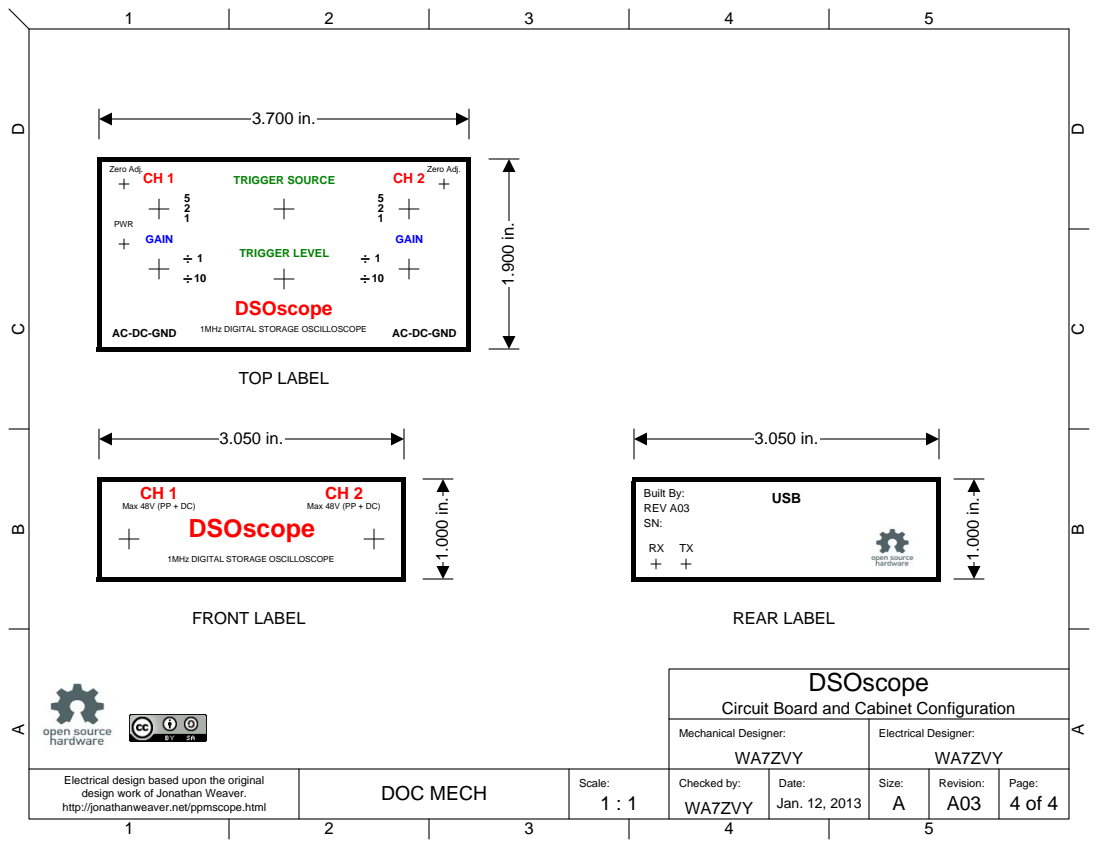
[picture p154: page 4]
GAIN; Zero Adj.; PWR; Mechanical Designer:; DSOscope; Jan. 12, 2013; A03 DOC MECH; Page: 4 of 4 Scale: 1 : 1; Electrical Designer:; TRIGGER SOURCE; TRIGGER LEVEL; TOP LABEL; FRONT LABEL; WA7ZVY; AC-DC-GND; AC-DC-GND ¹MHz DIGITAL STORAGE OSCILLOSCOPE; REAR LABEL

Max 48V (PP + DC)
DSOscope

USB Built By:
REV A03

1MHz DIGITAL STORAGE OSCILLOSCOPE

Circuit Board and Cabinet Configuration
