jonw0224/PPMScope/Contributions/Paul Messer/DSOscope_A03/DSOscope_Rev_A03_20130113/Schematic/A03/DSOscope_AnalogBrd_A03.pdf

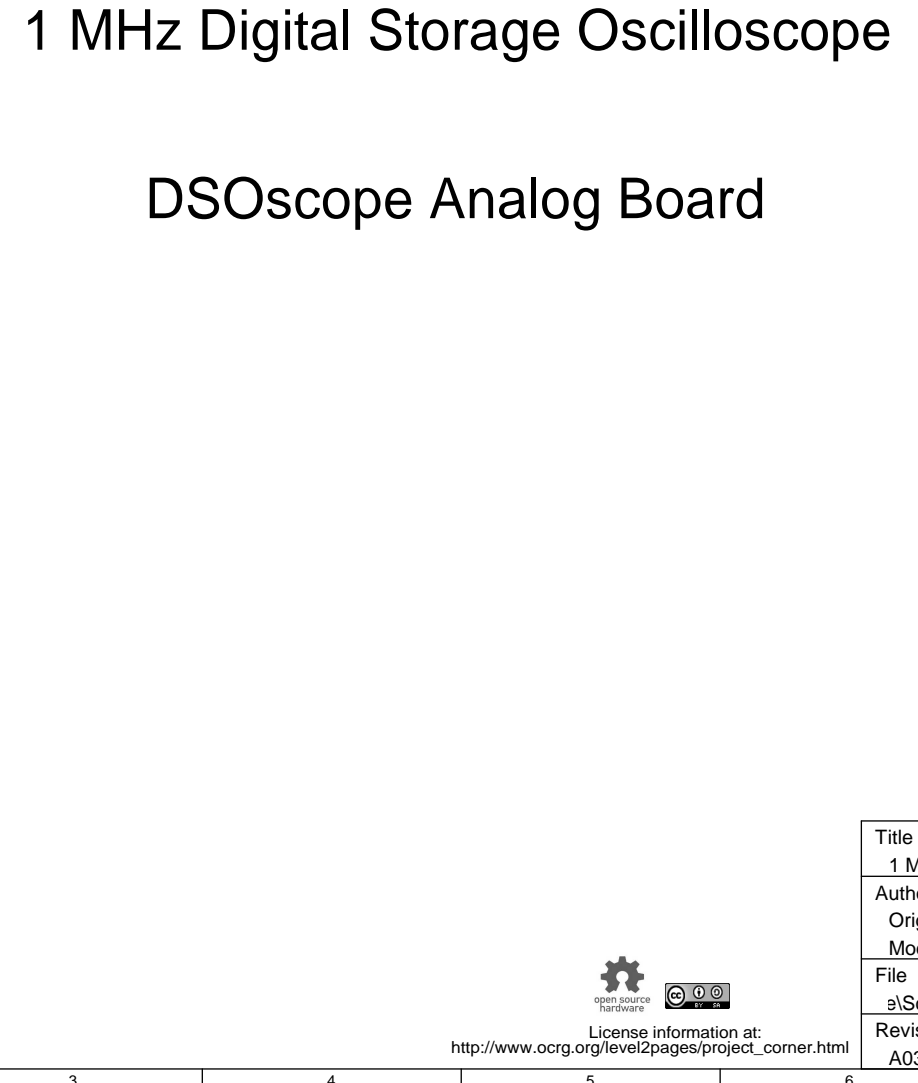
[picture p155: page 1]

1 MHz Digital Storage Oscilloscope

DSOscope Analog Board

Title
1 MHz Digital Storage Oscilloscope - Analog Board
Author
Original Design from http://jonathanweaver.net
Modifications by WA7ZVY - www.ocrg.org

File AnalogBrd_A03.dsn | Document 120402.2

License information at:

Revision A03 | Date January 10, 2013 | Sheets 1 of 2

http://www.ocrg.org/level2pages/project_corner.html

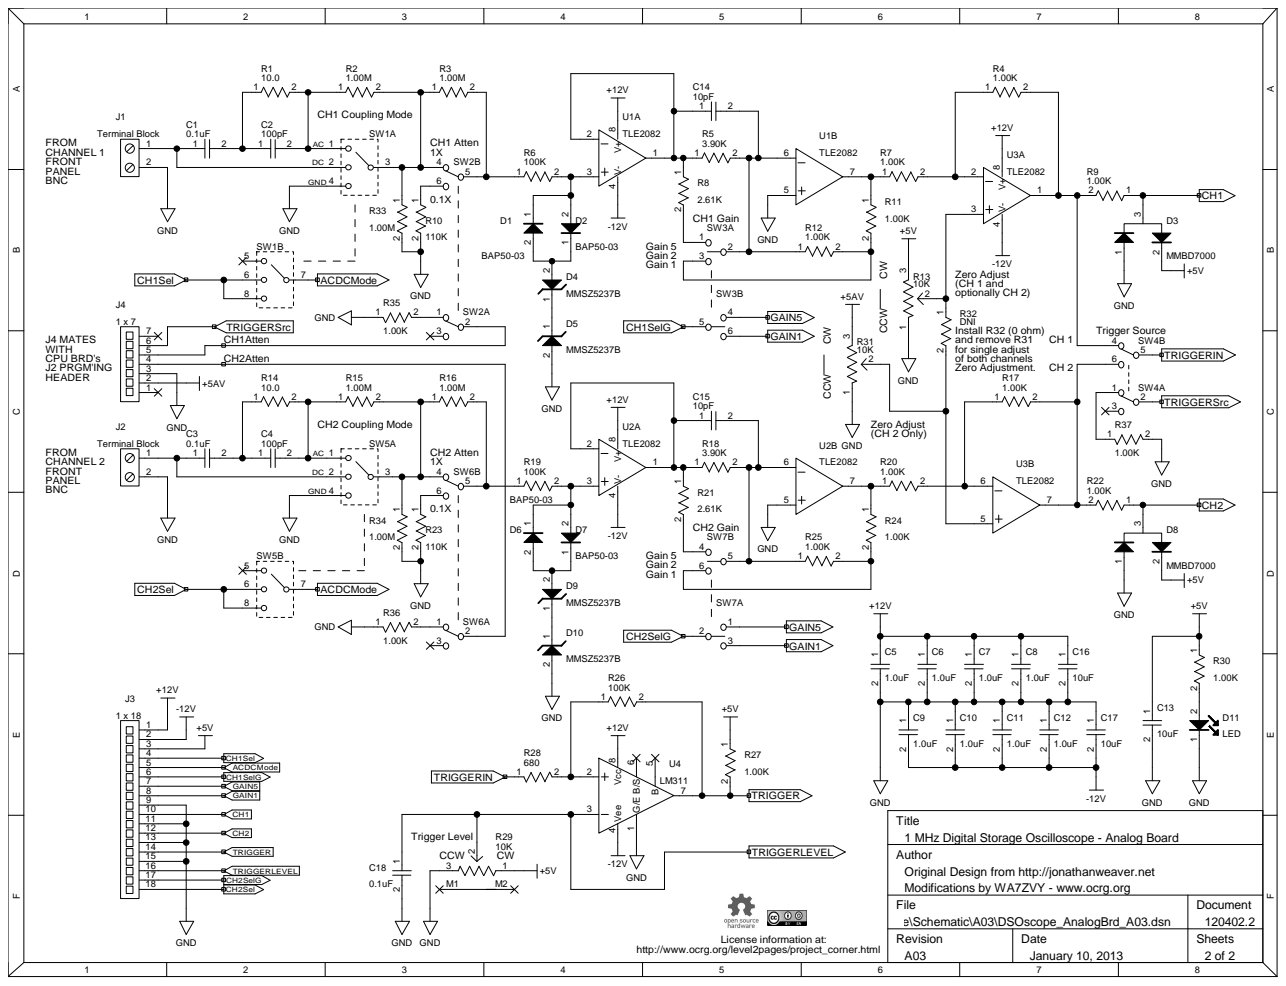
[picture p156: page 2]

Zero Adjust
(CH 1 and optionally CH 2)

1 2 R32 DNI
Install R32 (0 ohm) and remove R31
for single adjust of both channels
Zero Adjustment.

Zero Adjust (CH 2 Only)

-12V GND
Title
1 MHz Digital Storage Oscilloscope - Analog Board
Author
Original Design from http://jonathanweaver.net
Modifications by WA7ZVY - www.ocrg.org

File AnalogBrd_A03.dsn | Document 120402.2

Revision A03 | Date January 10, 2013 | Sheets 2 of 2

http://www.ocrg.org/level2pages/project_corner.html
