jonw0224/PPMScope/Contributions/Paul Messer/DSOscope_A03/DSOscope_Rev_A03_20130113/Schematic/A03/DSOscope_CPUBrd_A03.pdf

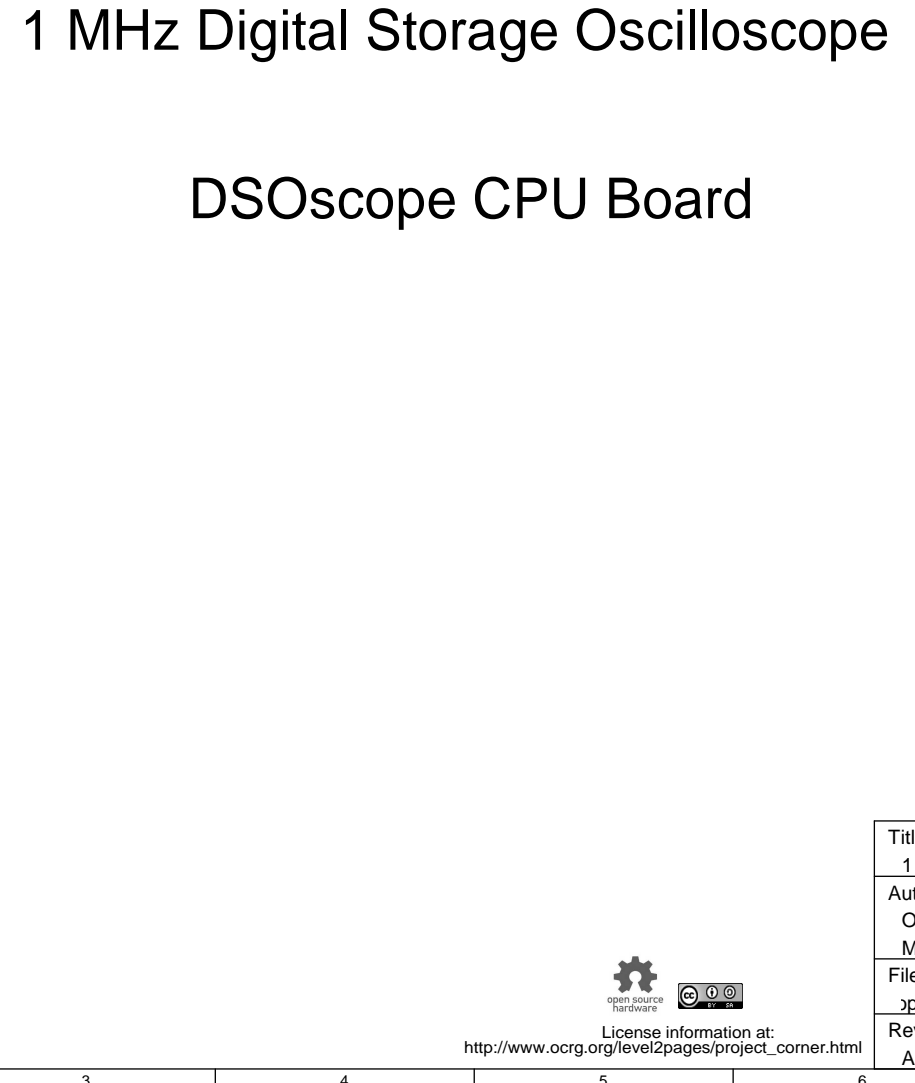
[picture p157: page 1]

1 MHz Digital Storage Oscilloscope

DSOscope CPU Board

Title
1 MHz Digital Storage Oscilloscope - CPU Board
Author
Original Design from http://jonathanweaver.net
Modifications by WA7ZVY - www.ocrg.org

File CPUBrd_A03.dsn | Document 120402.2

License information at:

Revision A03 | Date January 10, 2013 | Sheets 1 of 4

http://www.ocrg.org/level2pages/project_corner.html

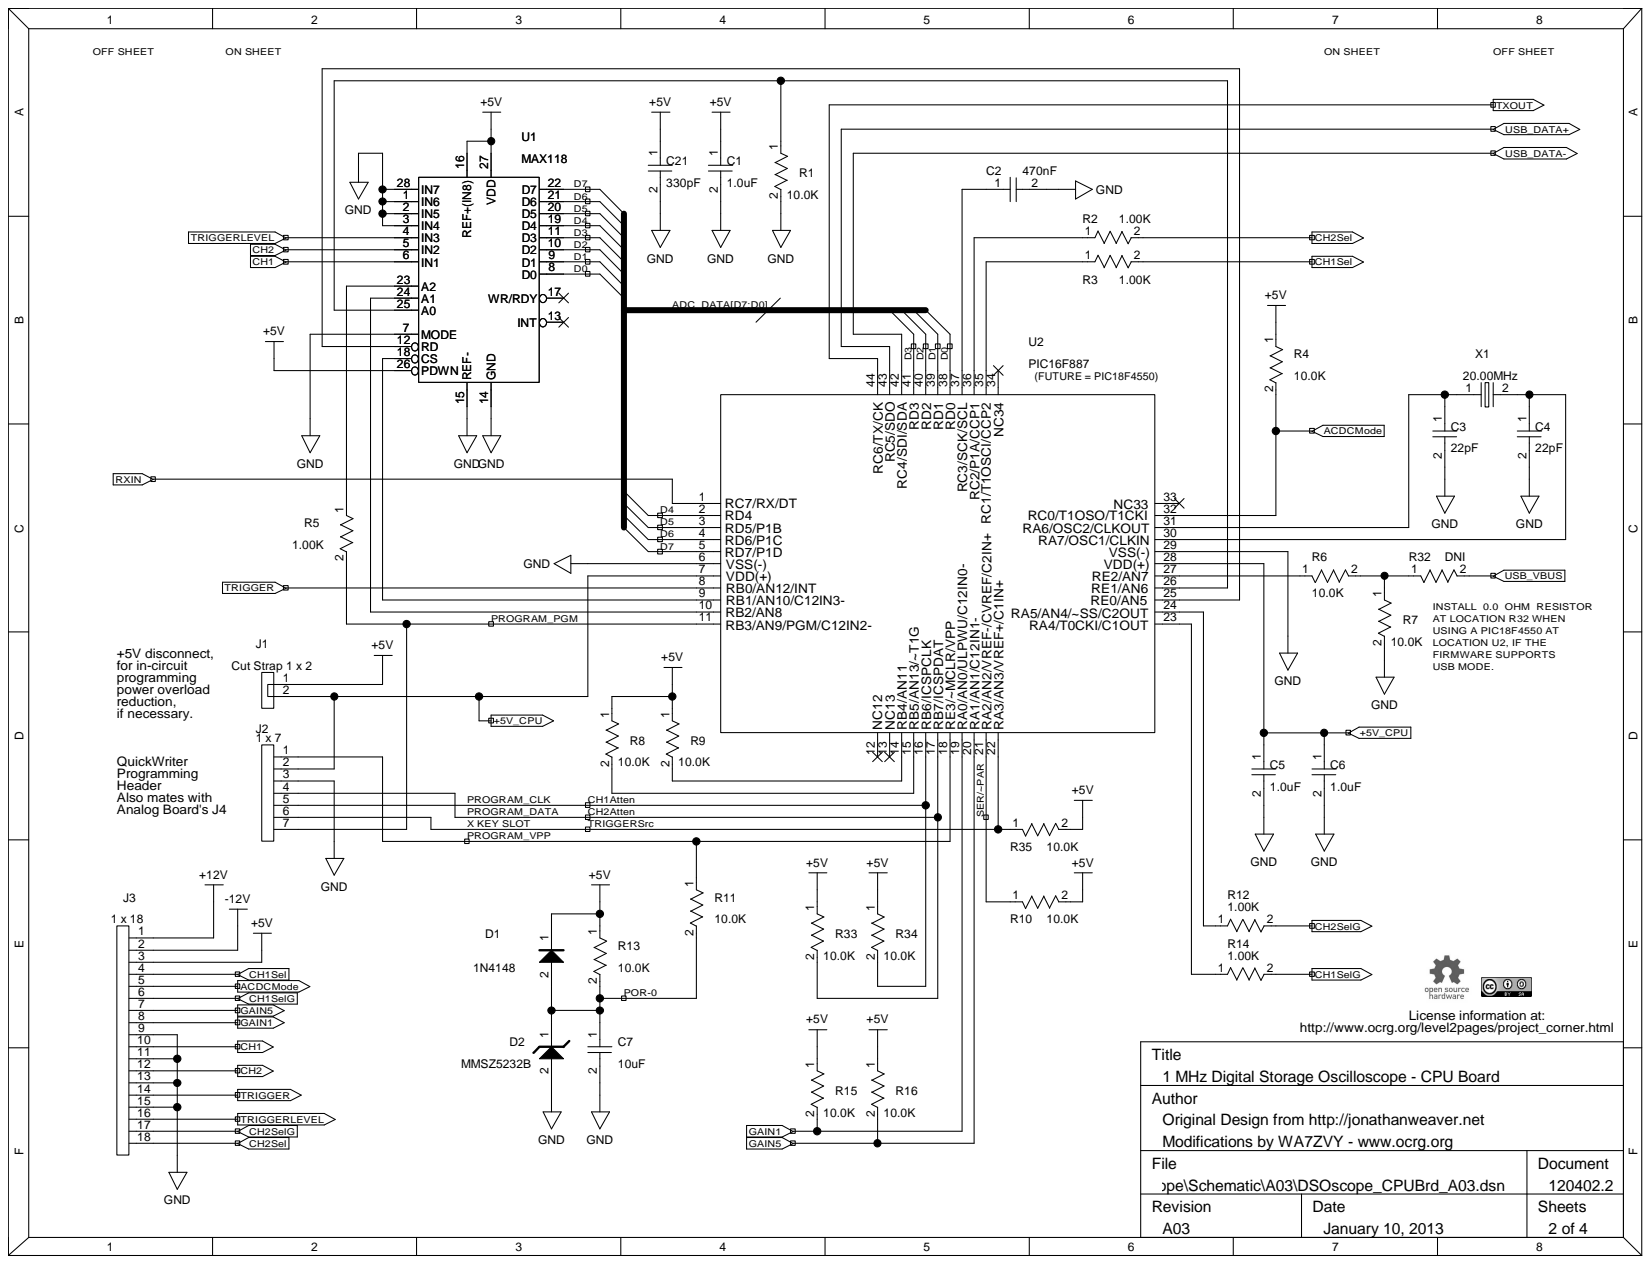
[picture p158: page 2]

TRIGGERLEVEL | 5 5 D2

+5V disconnect,
for in-circuit
programming power overload reduction,

http://www.ocrg.org/level2pages/project_corner.html

Title
1 MHz Digital Storage Oscilloscope - CPU Board
Author
Original Design from http://jonathanweaver.net
Modifications by WA7ZVY - www.ocrg.org
File

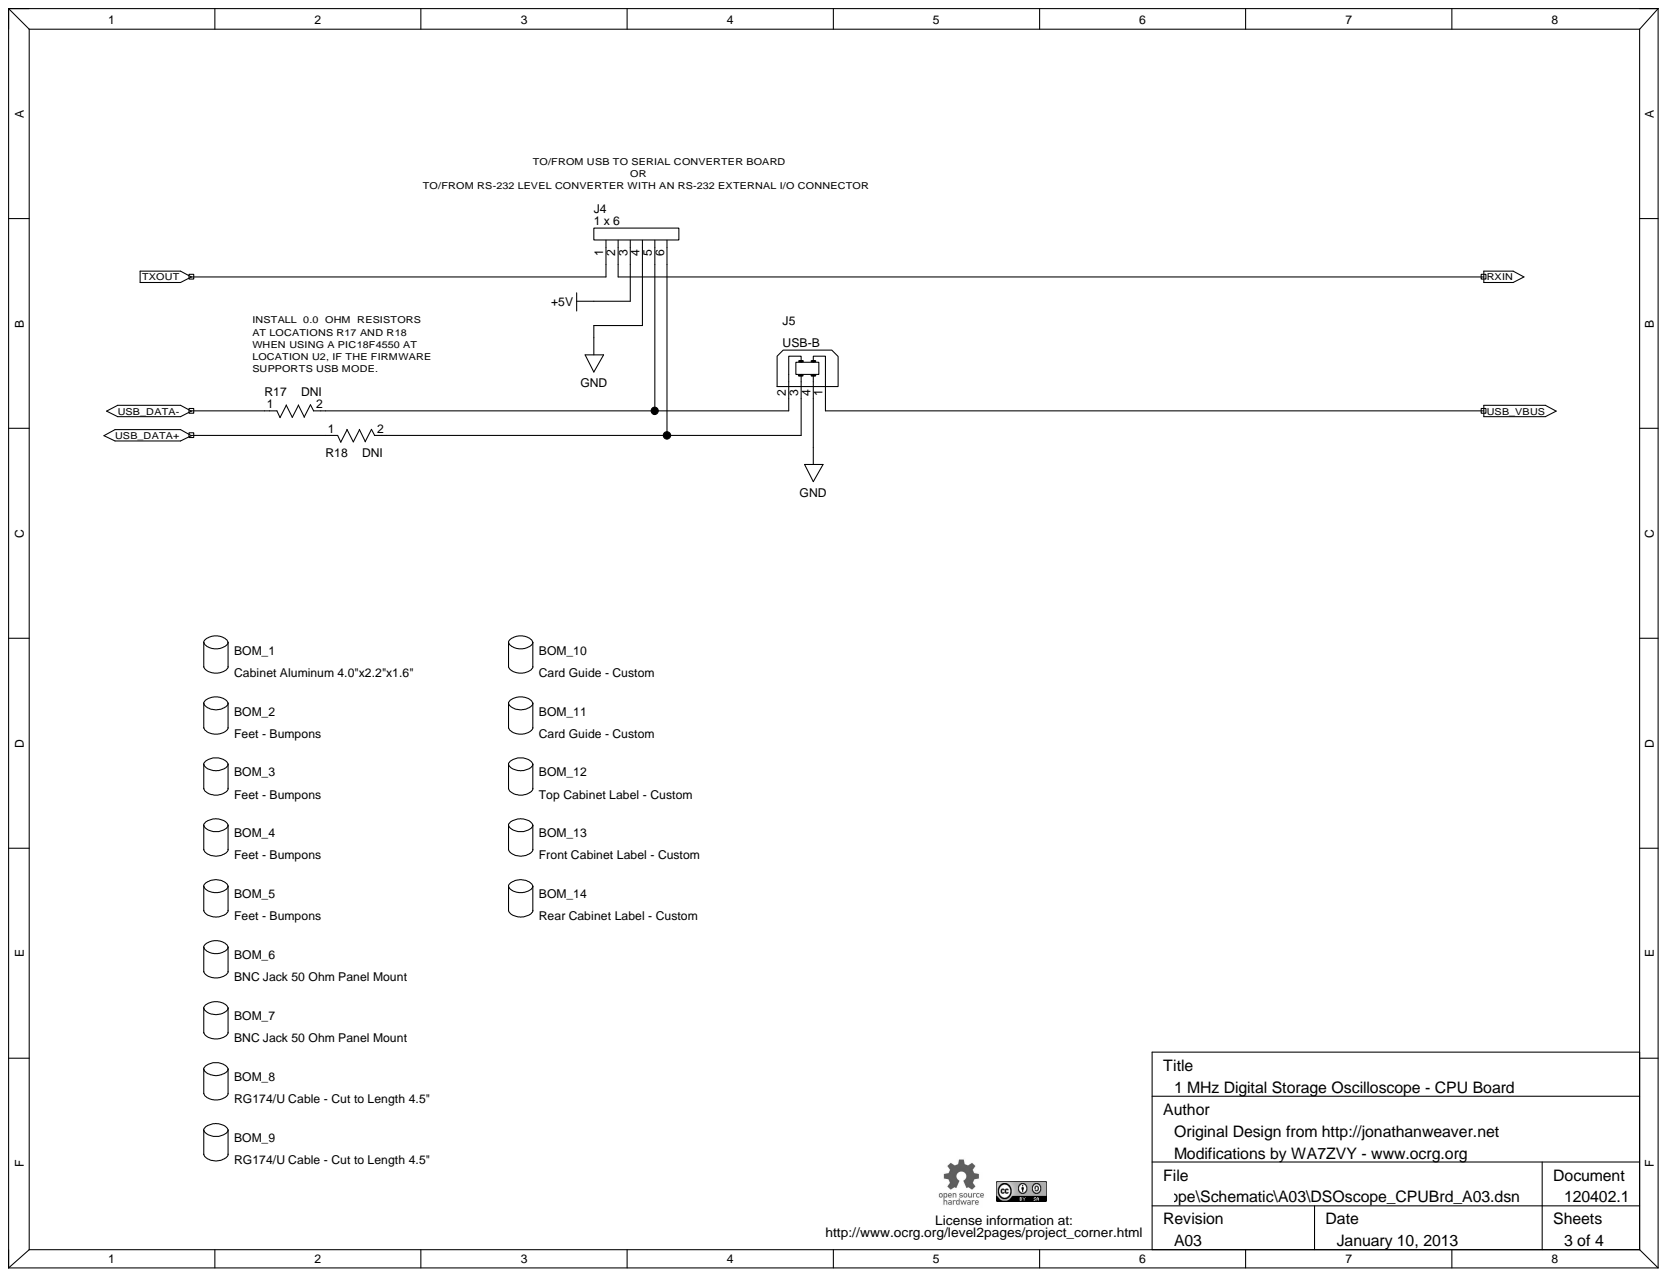
[picture p159: page 3]
GND; USB-B; USB_DATA+; USB_DATA-; USB_VBUS; TXOUT; RXIN; BOM_1; Cabinet Aluminum 4.0"x2.2"x1.6"; BOM_2; Feet - Bumpons; BOM_3; BOM_4; BOM_5; R18 DNI; Document; CPUBrd_A03.dsn

TO/FROM USB TO SERIAL CONVERTER BOARD

TO/FROM RS-232 LEVEL CONVERTER WITH AN RS-232 EXTERNAL I/O CONNECTOR

INSTALL 0.0 OHM RESISTORS
AT LOCATIONS R17 AND R18
WHEN USING A PIC18F4550 AT
LOCATION U2, IF THE FIRMWARE
SUPPORTS USB MODE.
R17 DNI

BOM_10
Card Guide - Custom

BOM_11

BOM_12
Top Cabinet Label - Custom

BOM_13
Front Cabinet Label - Custom

BOM_14
Rear Cabinet Label - Custom

BOM_6
BNC Jack 50 Ohm Panel Mount

BOM_7

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

BOM_8
RG174/U Cable - Cut to Length 4.5"

BOM_9

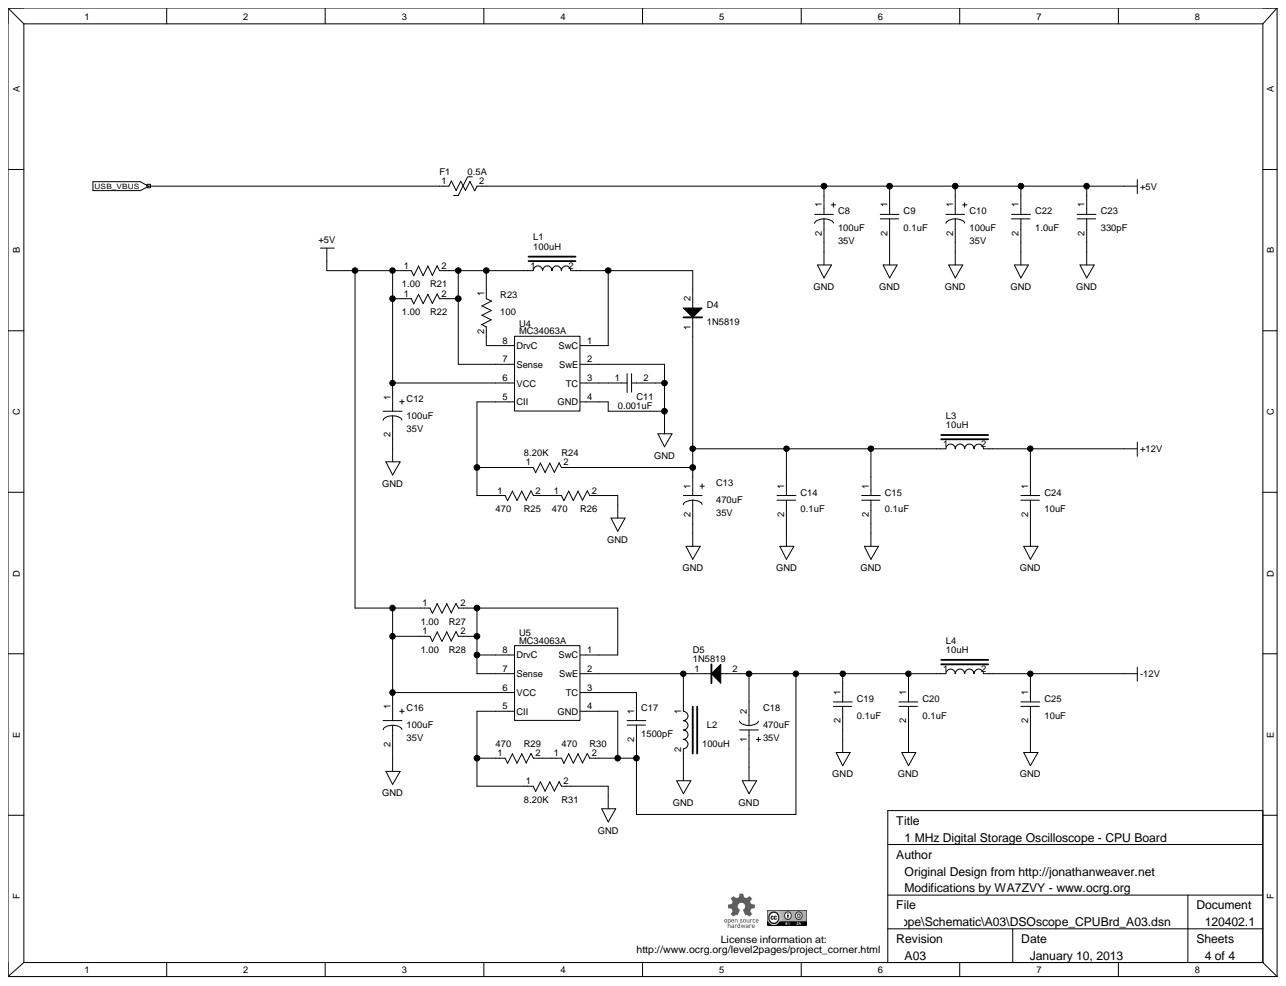
[picture p160: page 4]
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
