jonw0224/PPMScope/Contributions/Paul Messer/DSOscope_A03/DSOscope_Rev_A03_20130113/Schematic/A03/DSOscope_USBBrd_A03.pdf

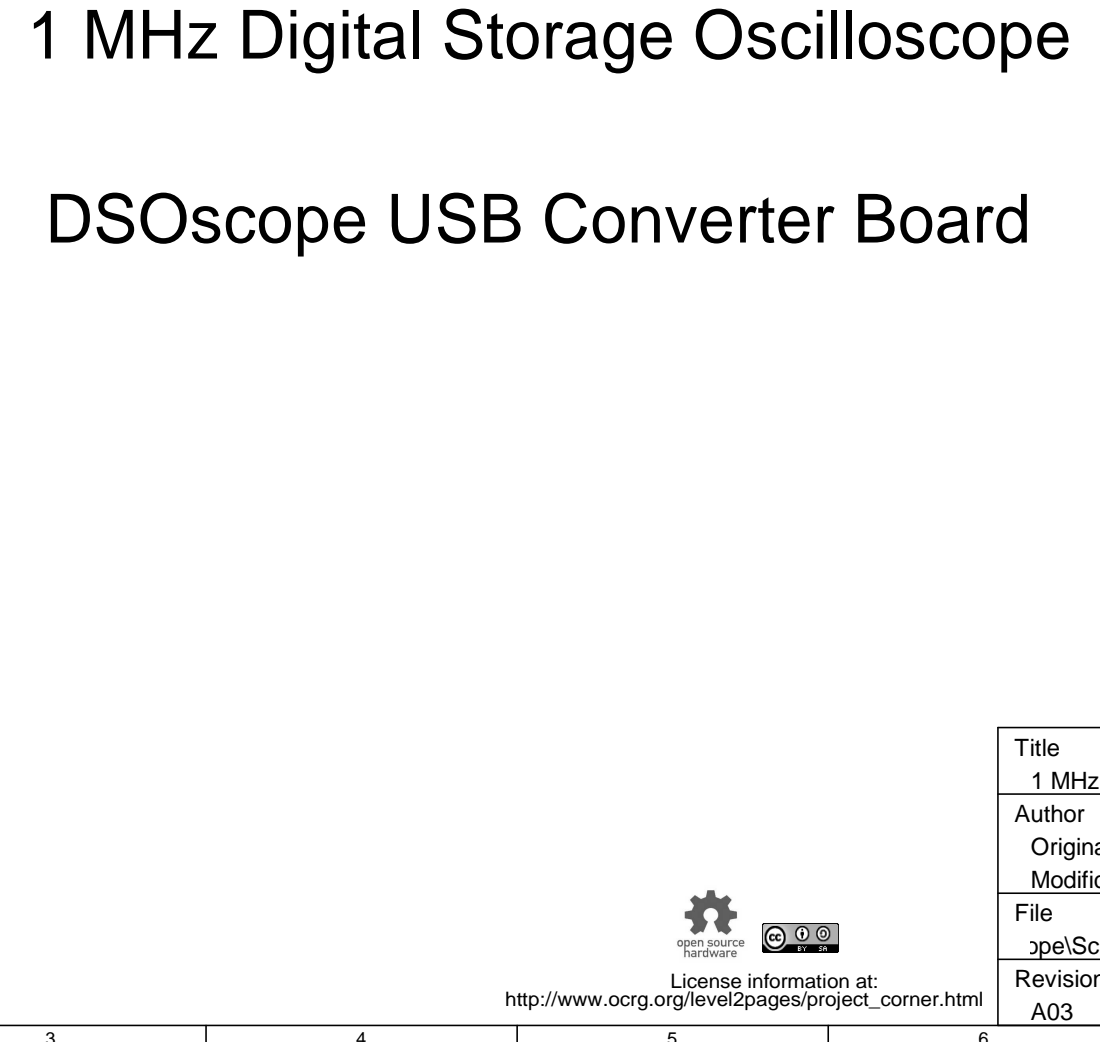
[picture p161: page 1]

1 MHz Digital Storage Oscilloscope

DSOscope USB Converter Board

Title
1 MHz Digital Storage Oscilloscope - USB Converter Board
Author
Original Design from http://jonathanweaver.net
Modifications by WA7ZVY - www.ocrg.org

File USBBrd_A03.dsn | Document 120424.1

License information at:

Revision A03 | Date January 12, 2013 | Sheets 1 of 2

http://www.ocrg.org/level2pages/project_corner.html

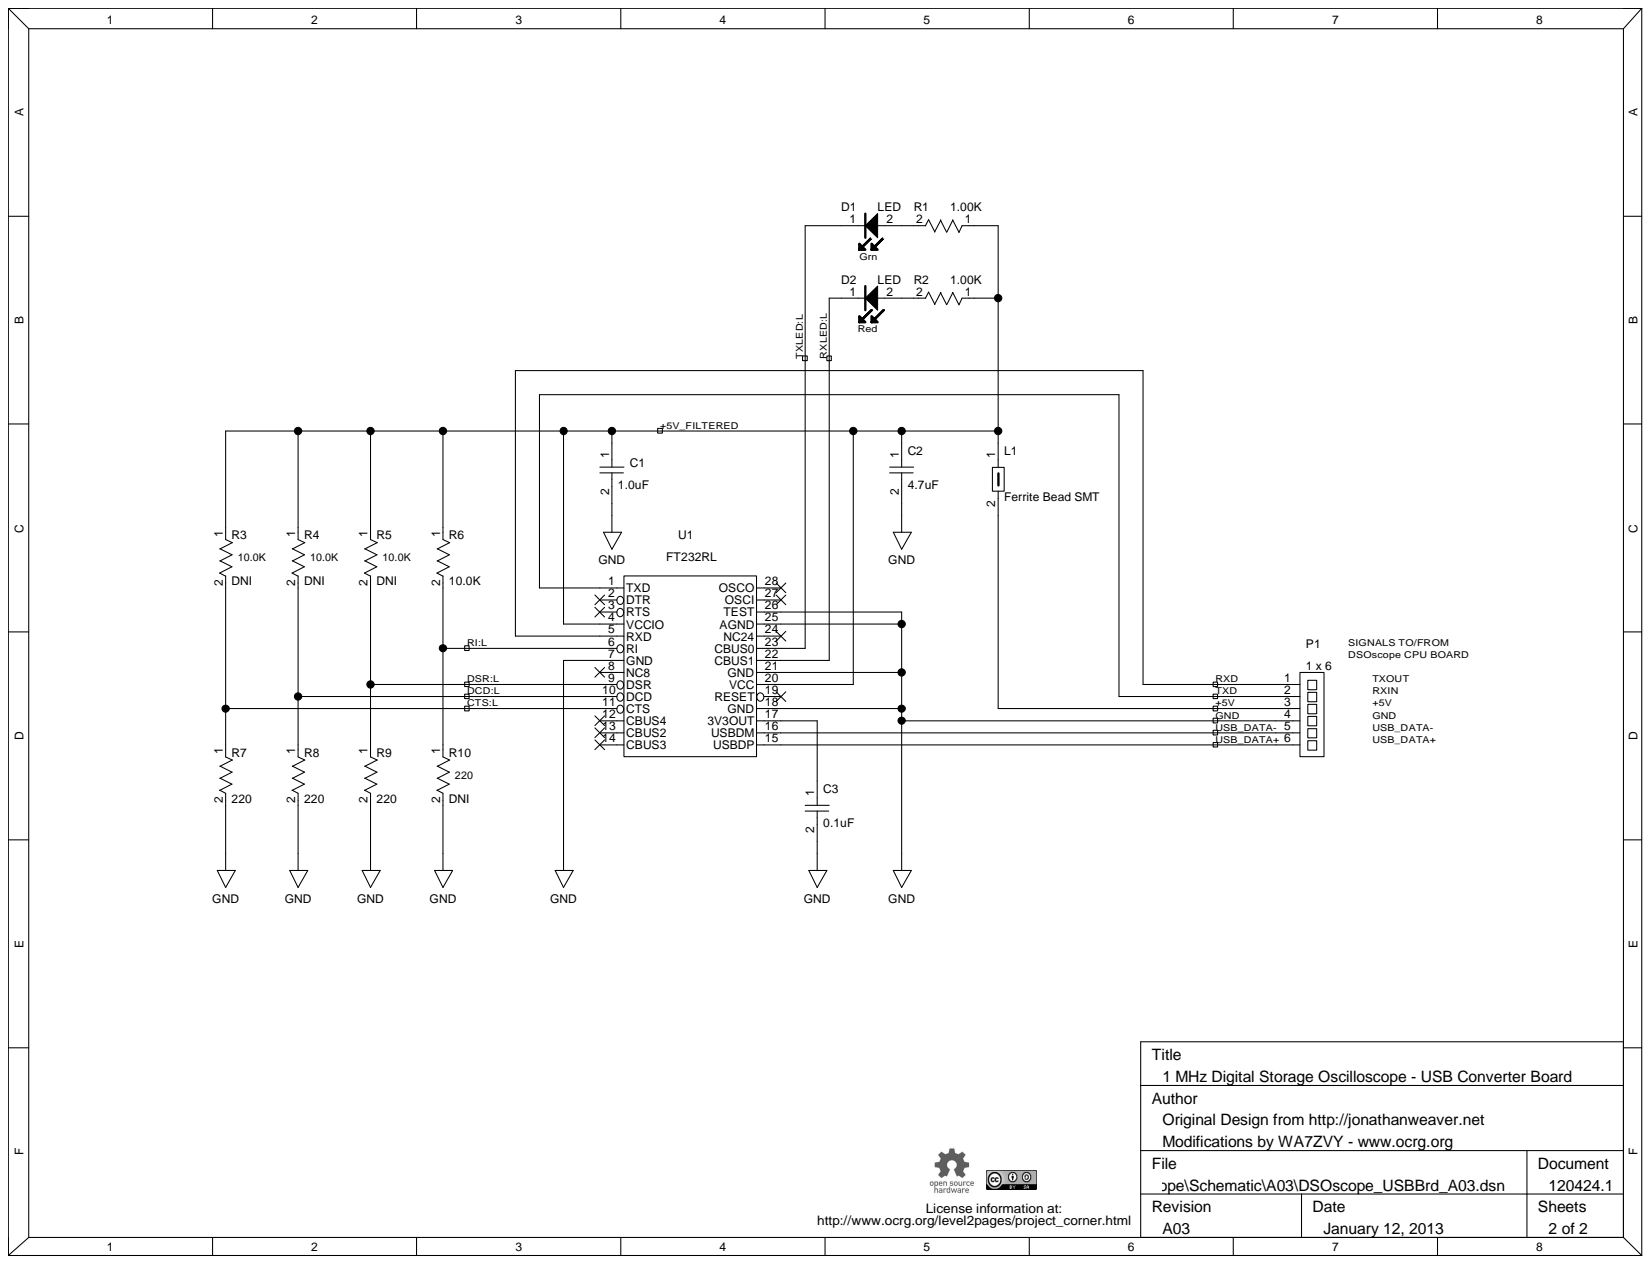
[picture p162: page 2]

+5V_FILTERED

GND

DCD:L
CTS:L

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

File USBBrd_A03.dsn | Document 120424.1

Revision A03 | Date January 12, 2013 | Sheets 2 of 2

http://www.ocrg.org/level2pages/project_corner.html
