jonw0224/PPMScope/Contributions/Paul Messer/CAB-PCB.pdf

CH 1 | CH 2

4.000 in.

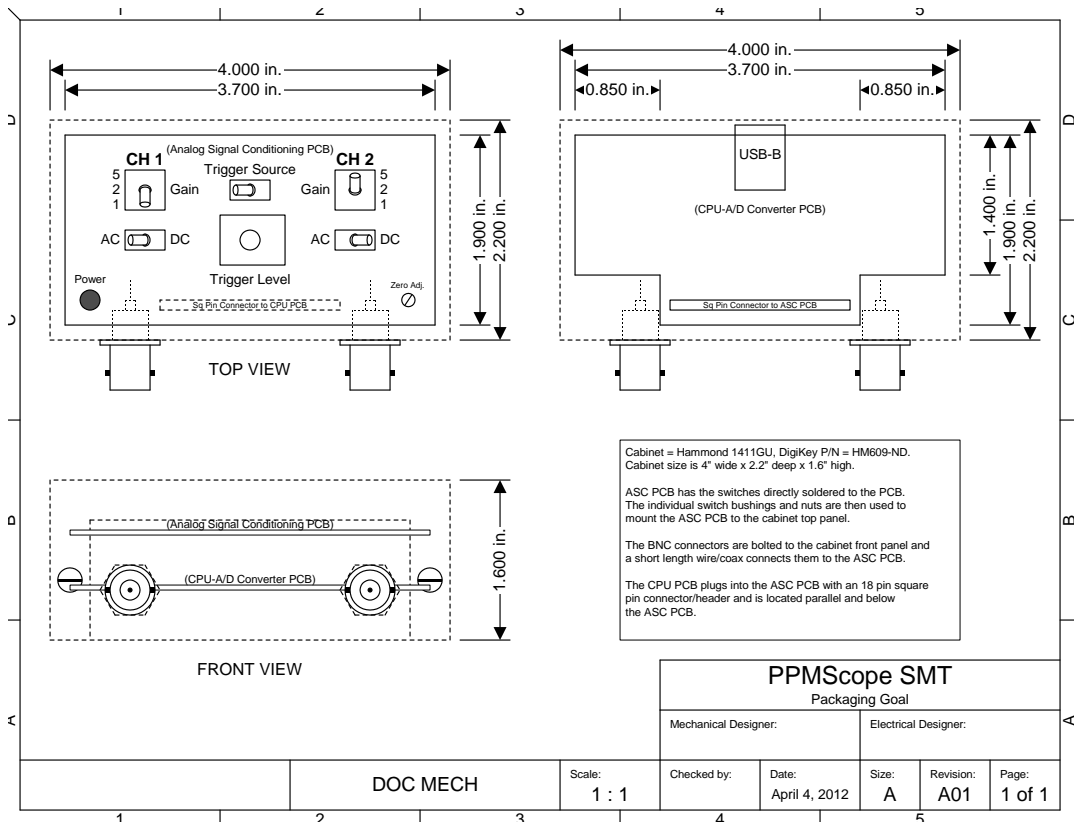
[picture p163: page 1]
Gain; PPMScope SMT; Packaging Goal; Electrical Designer:; Trigger Level; USB-B; TOP VIEW; FRONT VIEW

(Analog Signal Conditioning PCB)
Trigger Source
Gain

(CPU-A/D Converter PCB)

Zero Adj. Power

Sq Pin Connector to CPU PCB

Sq Pin Connector to ASC PCB

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

ASC PCB has the switches directly soldered to the PCB.
The individual switch bushings and nuts are then used to
mount the ASC PCB to the cabinet top panel.

The BNC connectors are bolted to the cabinet front panel and
a short length wire/coax connects them to the ASC PCB.

The CPU PCB plugs into the ASC PCB with an 18 pin square
pin connector/header and is located parallel and below
the ASC PCB.

Mechanical Designer:

Checked by: | Date: April 4, 2012 | Size: A | Revision: A01 DOC MECH | Page: 1 of 1 Scale: 1 : 1
