jonw0224/PPMScope/PCB/USBToSerial Daughterboard/USB_PCBTop_Mirrored.pdf

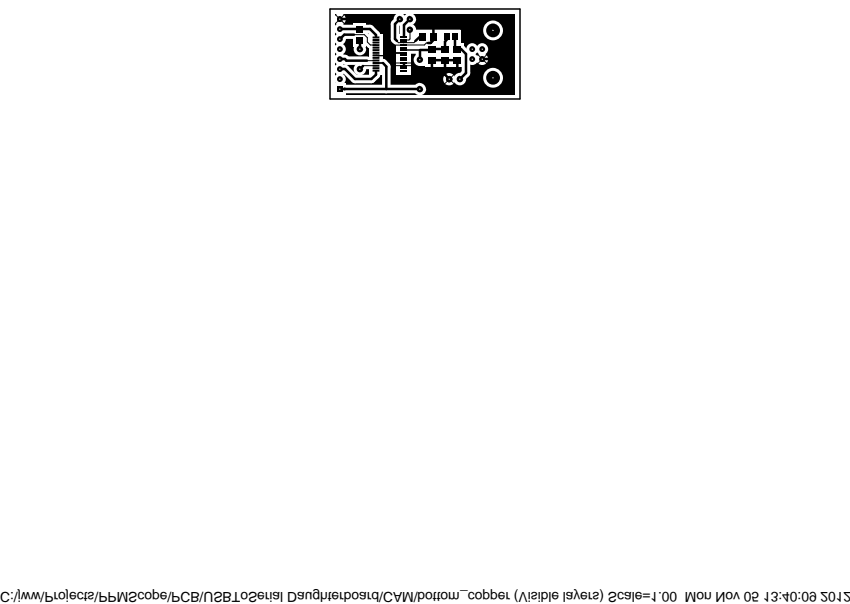
[picture p165: page 1]

C:\jww\Projects\PPMScope\PCB\USBToSerial Daughterboard\CAM\bottom_copper (Visible layers) Scale=1.00 Mon Nov 05 13:40:09 2012
