jonw0224/PPMScope/PCB/Version 1.20/PCB.pdf

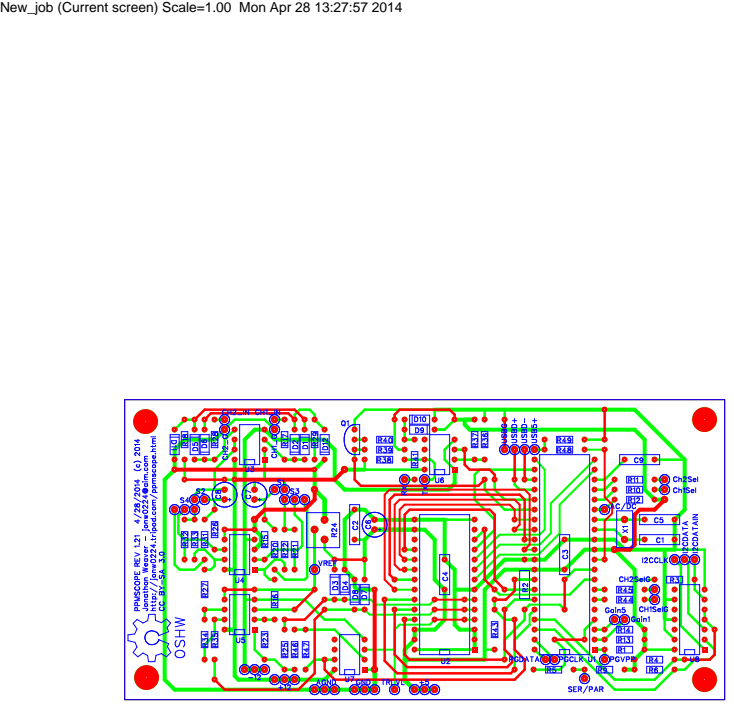
[picture p166: page 1]

New_job (Current screen) Scale=1.00 Mon Apr 28 13:27:57 2014
