jonw0224/PPMScope/PCB/Version 1.20/PCBBottom.pdf

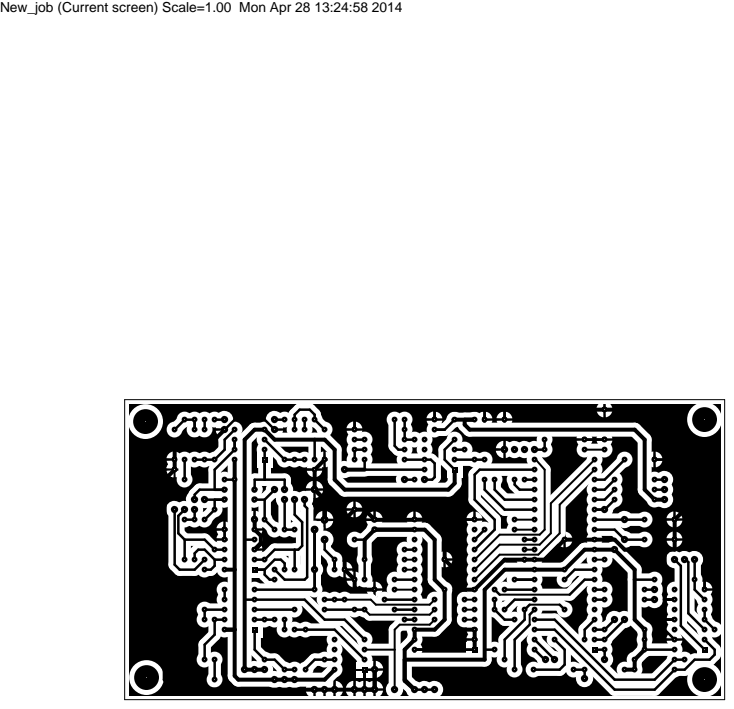
[picture p167: page 1]

New_job (Current screen) Scale=1.00 Mon Apr 28 13:24:58 2014
