jonw0224/PPMScope/PCB/Version 1.20/PCBTop_Mirrored.pdf

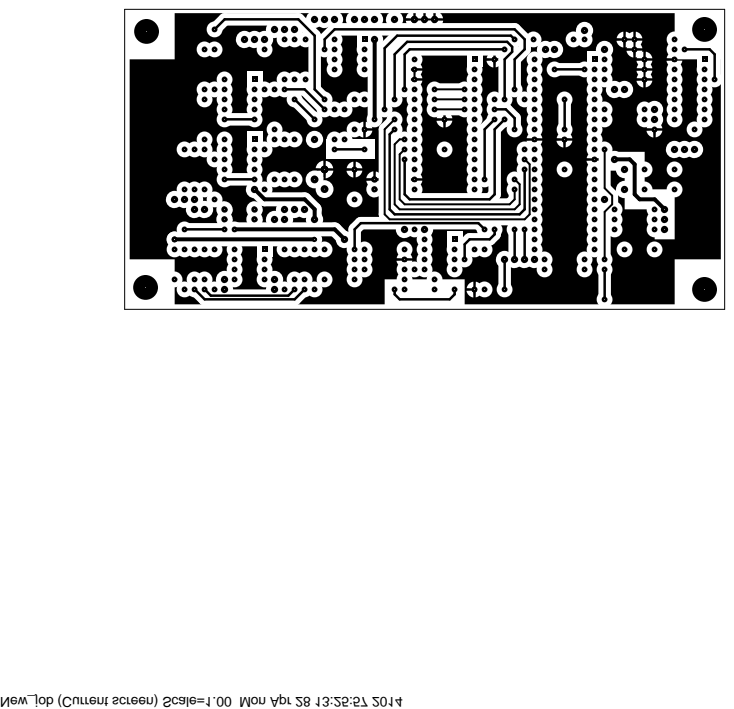
[picture p168: page 1]

New_job (Current screen) Scale=1.00 Mon Apr 28 13:25:57 2014
