jonw0224/PPMScope/PCB/Version 1.20/PCBTopSilk_Mirrored.pdf

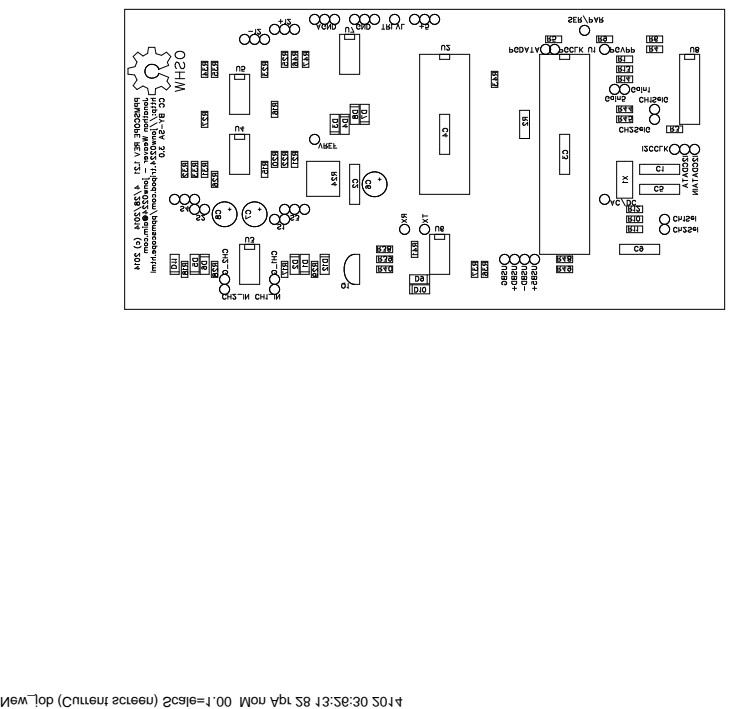
[picture p169: page 1]

New_job (Current screen) Scale=1.00 Mon Apr 28 13:26:30 2014
