jonw0224/PPMScope/Contributions/Chris_PCB/bottom_copper.pdf

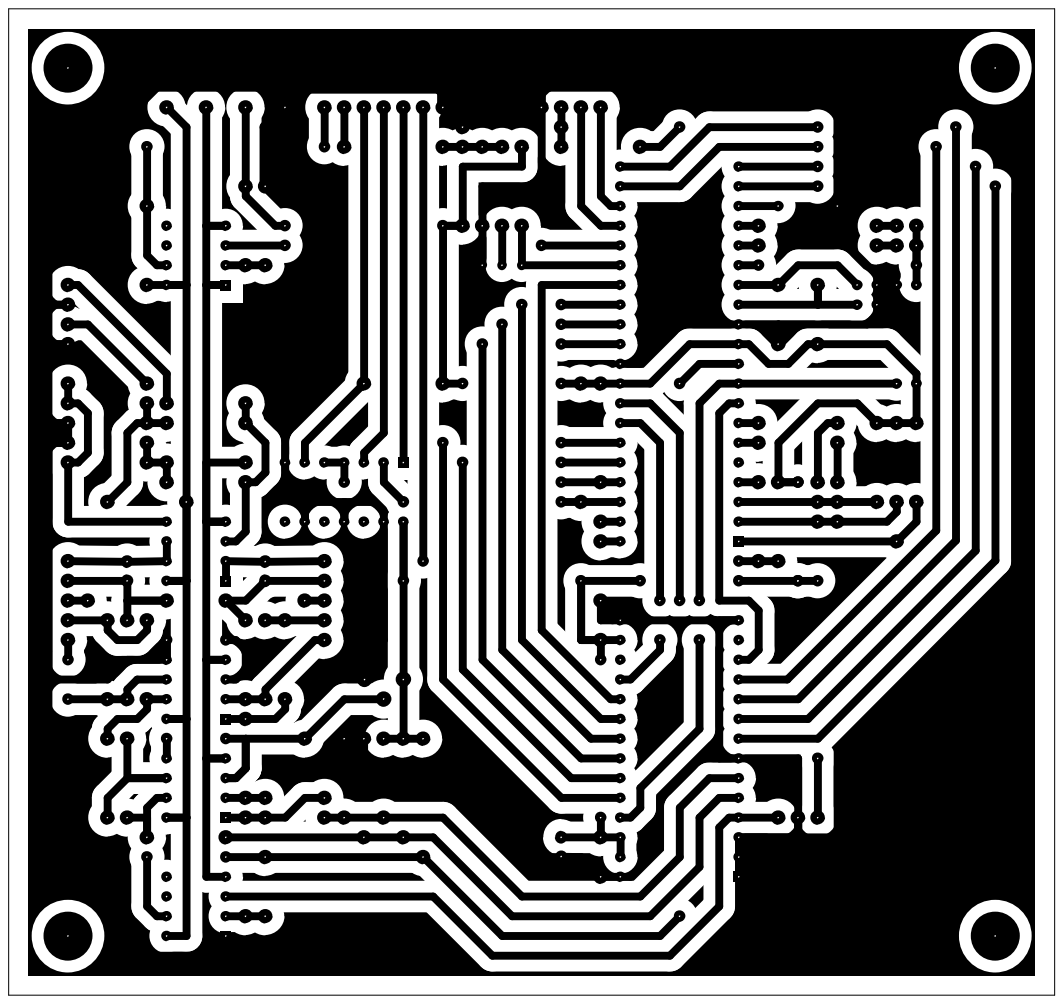
[picture p170: page 1]
