jonw0224/PPMScope/PCB/USBToSerial Daughterboard/USB_PCBBottom.pdf

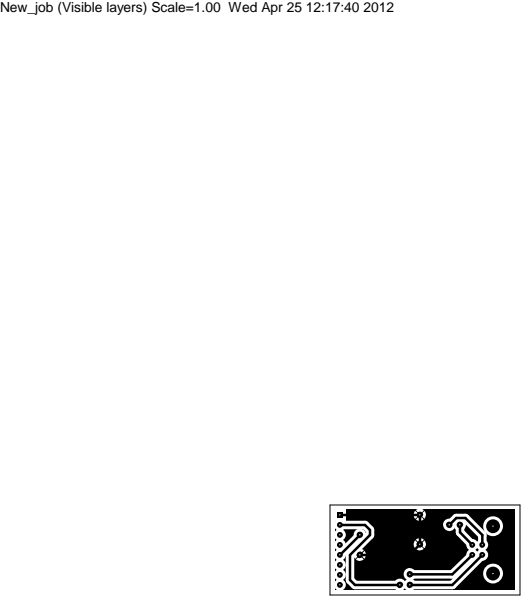
[picture p171: page 1]

New_job (Visible layers) Scale=1.00 Wed Apr 25 12:17:40 2012
