jonw0224/PPMScope/PCsource/Help/PCBtop.pdf

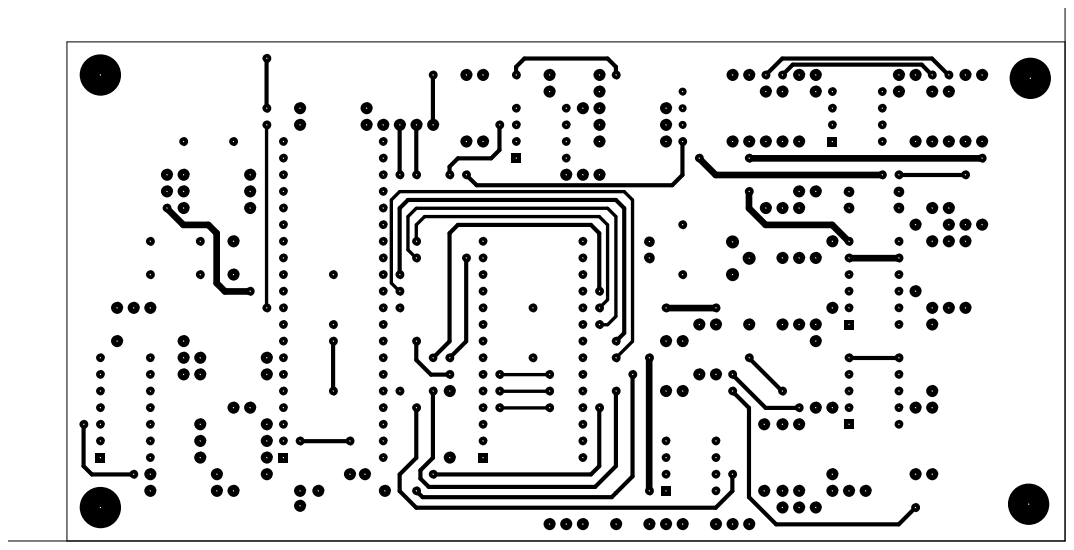
[picture p172: page 1]
