jonw0224/PPMScope/PCsource/Help/PCBTopSilk.pdf

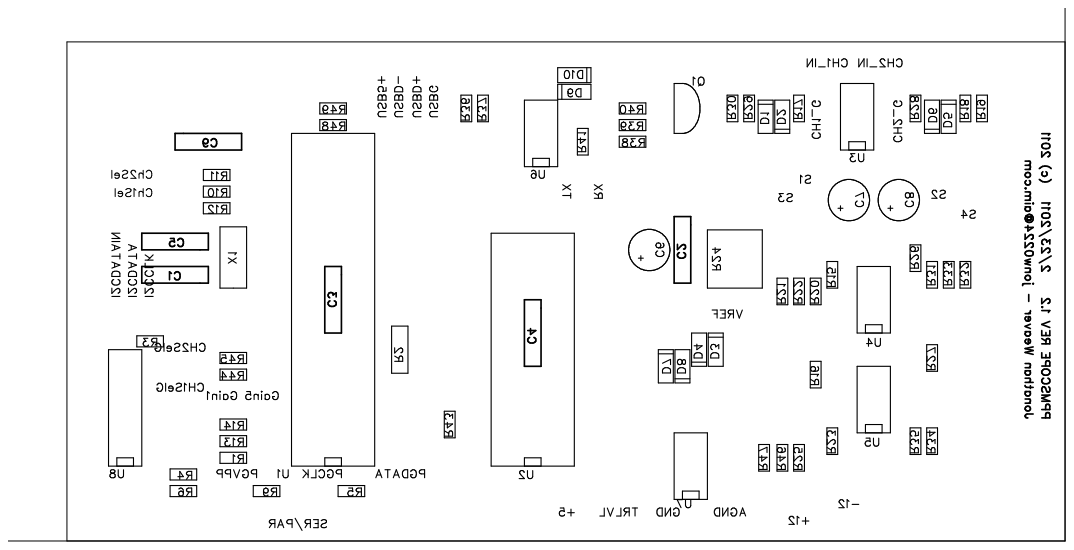
[picture p173: page 1]
