jonw0224/PPMScope/Contributions/Paul Messer/DSOscope_A03/DSOscope_Rev_A03_20130201/PCB/Analog_TopMirrored.pdf

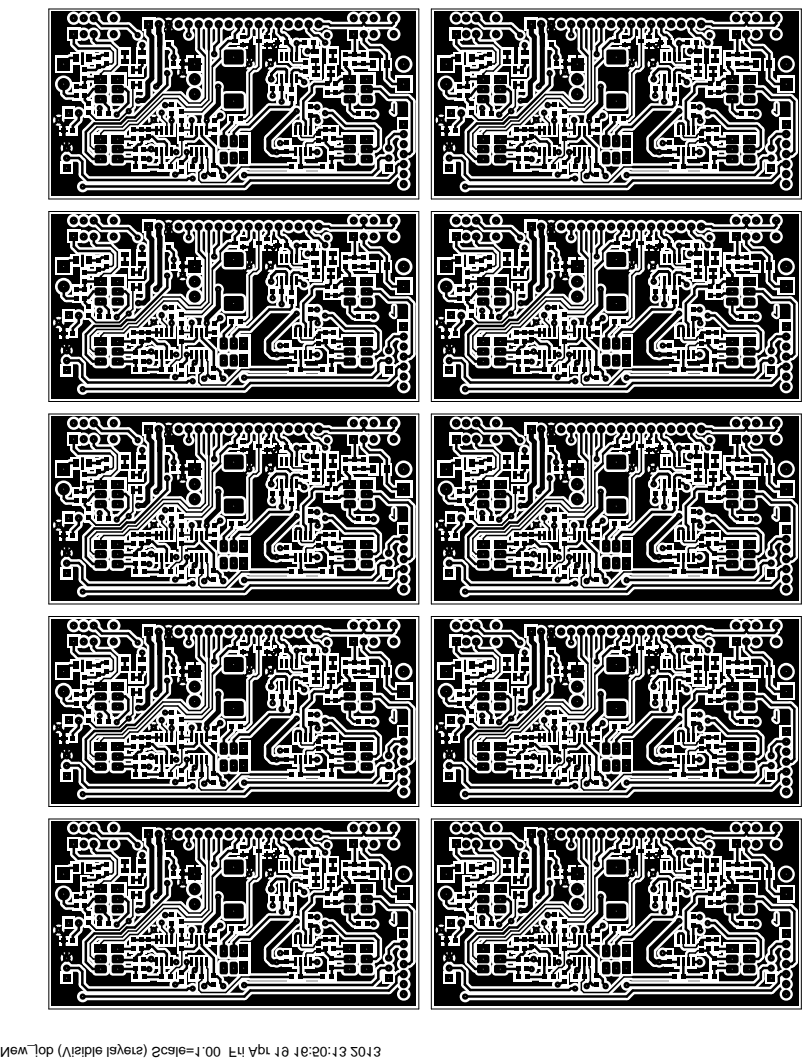
[picture p175: page 1]

New_job (Visible layers) Scale=1.00 Fri Apr 19 16:50:13 2013
