jonw0224/PPMScope/Contributions/Paul Messer/DSOscope_A03/DSOscope_Rev_A03_20130201/PCB/CPU_Bottom1.pdf

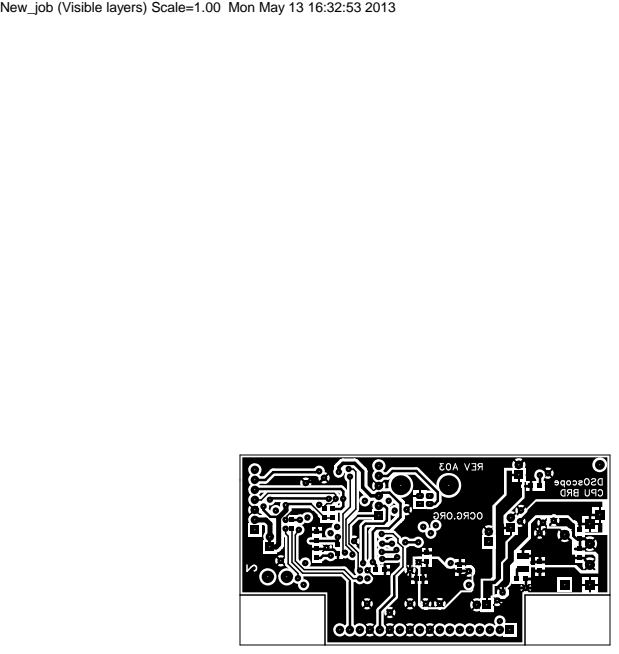
[picture p177: page 1]

New_job (Visible layers) Scale=1.00 Mon May 13 16:32:53 2013
