jonw0224/PPMScope/Contributions/Paul Messer/DSOscope_A03/DSOscope_Rev_A03_20130201/PCB/CPU_TopMirrored1.pdf

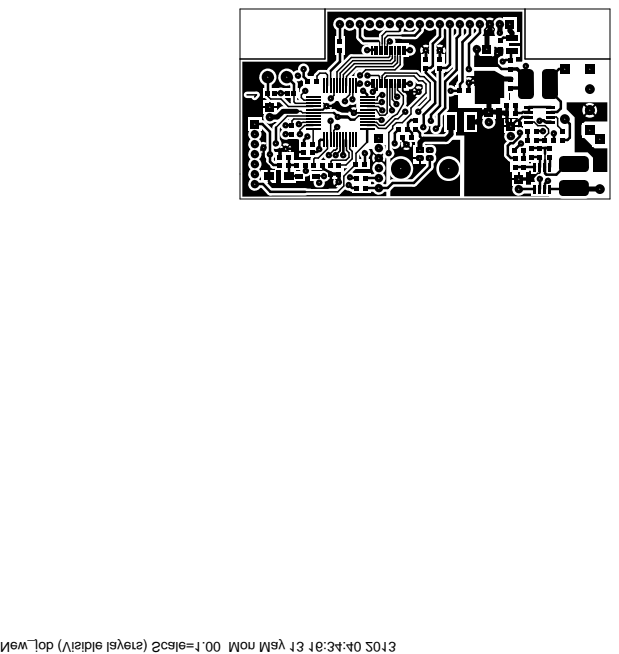
[picture p179: page 1]

New_job (Visible layers) Scale=1.00 Mon May 13 16:34:40 2013
