jonw0224/PPMScope/Schematics/Version 1.05/PPM1MHz.pdf

## Oscilloscope Overview

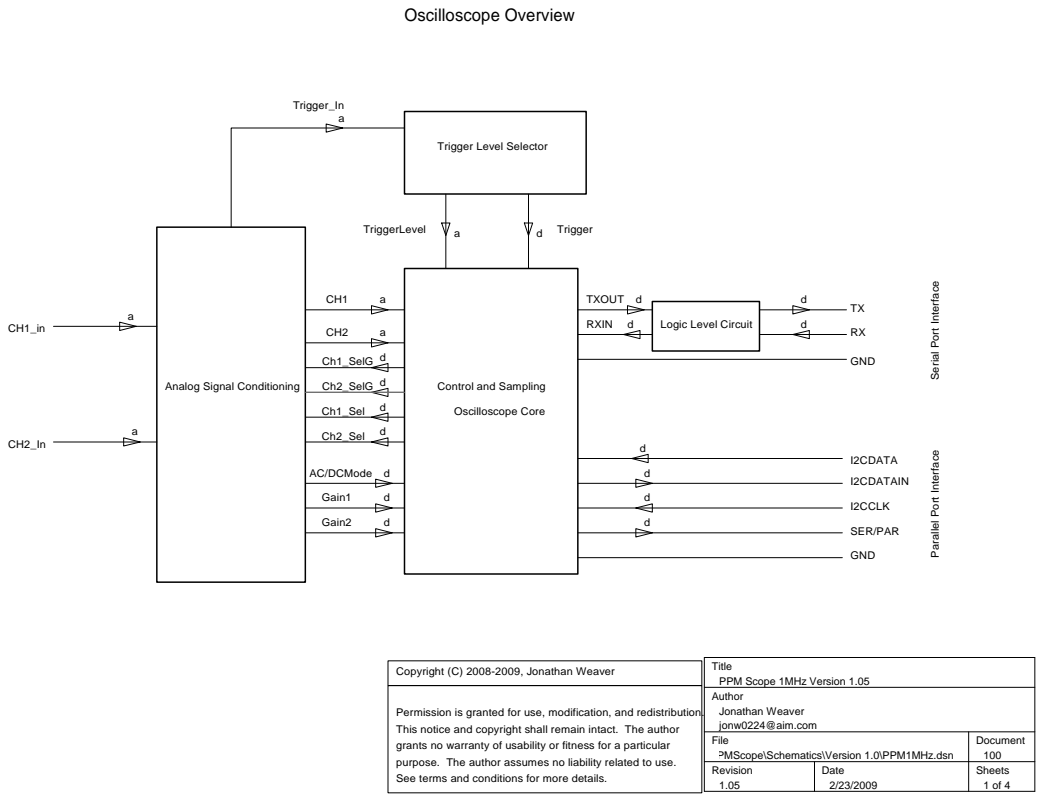
[picture p184: page 1]
Oscilloscope Core; I2CDATA; I2CDATAIN; I2CCLK; SER/PAR; GND; TXOUT; RXIN d; TriggerLevel; Trigger a; Trigger_In; Ch1_Sel; Ch2_Sel; AC/DCMode; Gain1; Gain2; Ch1_SelG; Ch2_SelG

Trigger Level Selector

Serial Port Interface

Logic Level Circuit

Analog Signal Conditioning

Control and Sampling

Parallel Port Interface ddd

Title
PPM Scope 1MHz Version 1.05
Author
Jonathan Weaver
jonw0224@aim.com

Copyright (C) 2008-2009, Jonathan Weaver

Permission is granted for use, modification, and redistribution.
This notice and copyright shall remain intact. The author
grants no warranty of usability or fitness for a particular
purpose. The author assumes no liability related to use.
See terms and conditions for more details.

File | Document

E:\Projects\PPMScope\Schematics\Version 1.0\PPM1MHz.dsn

Revision | Date 2/23/2009 | Sheets 1 of 4

## Control and Sampling - Oscilloscope Core

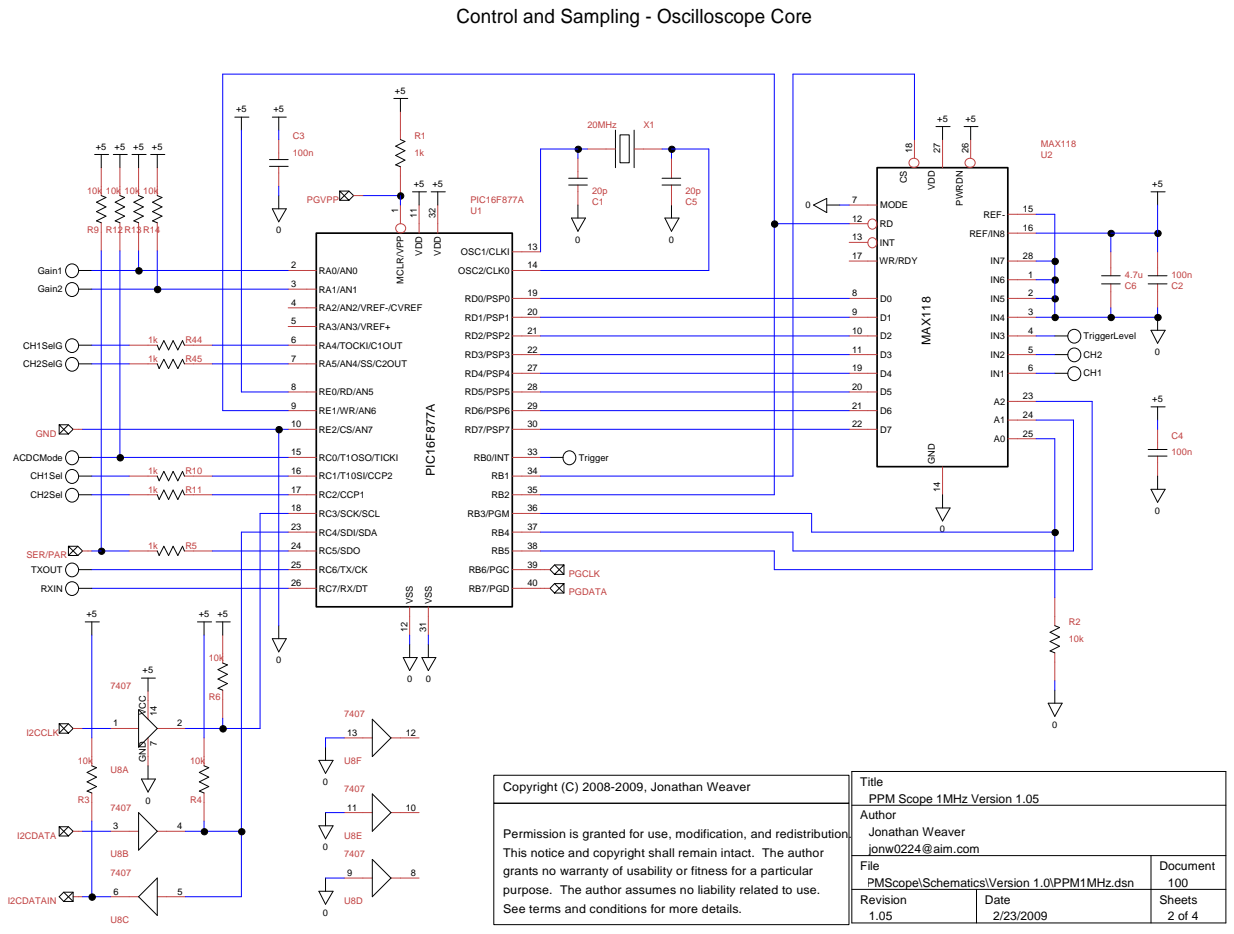
[picture p185: page 2]
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

## Analog Signal Conditioning

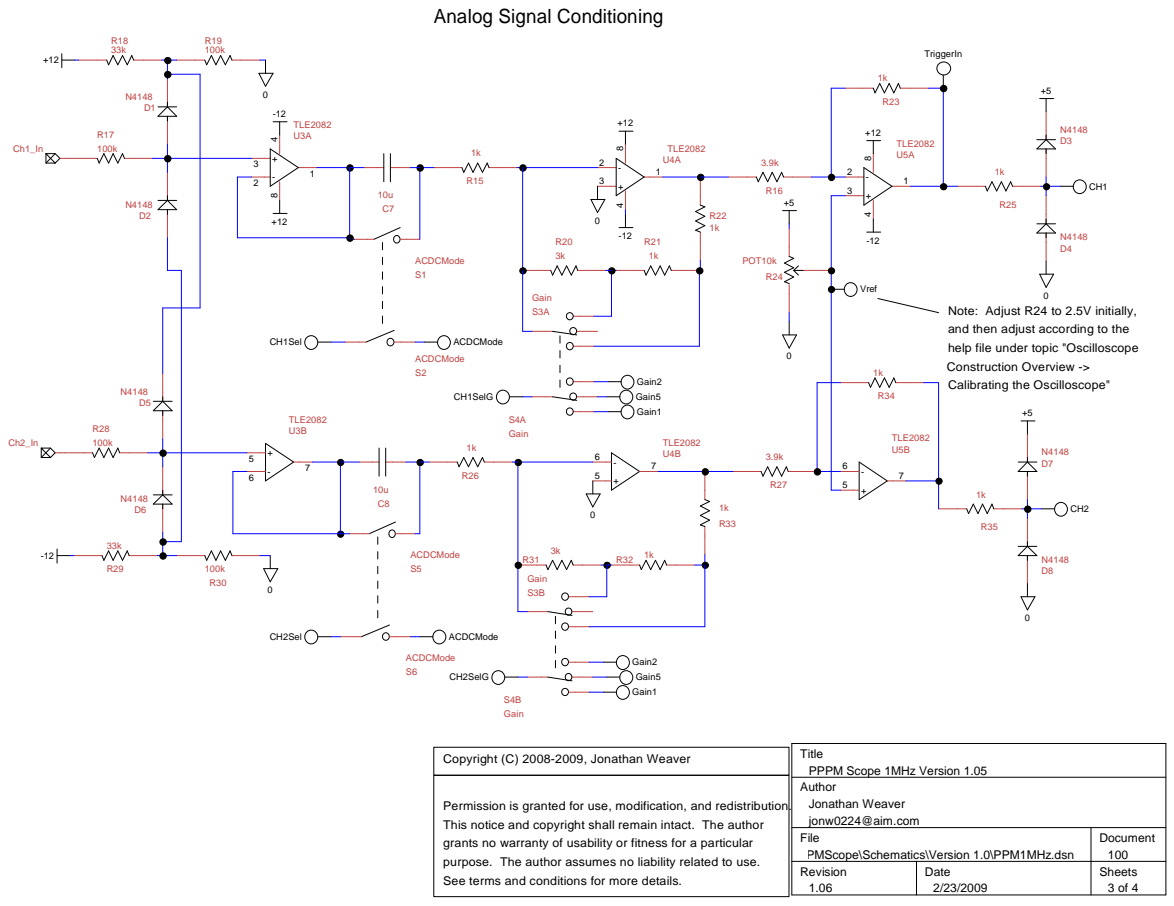
[picture p186: page 3]

Note: Adjust R24 to 2.5V initially,
and then adjust according to the
help file under topic "Oscilloscope
Construction Overview ->
Calibrating the Oscilloscope"

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

Computer Interface - Logic Level Circuits | Trigger Level Selector

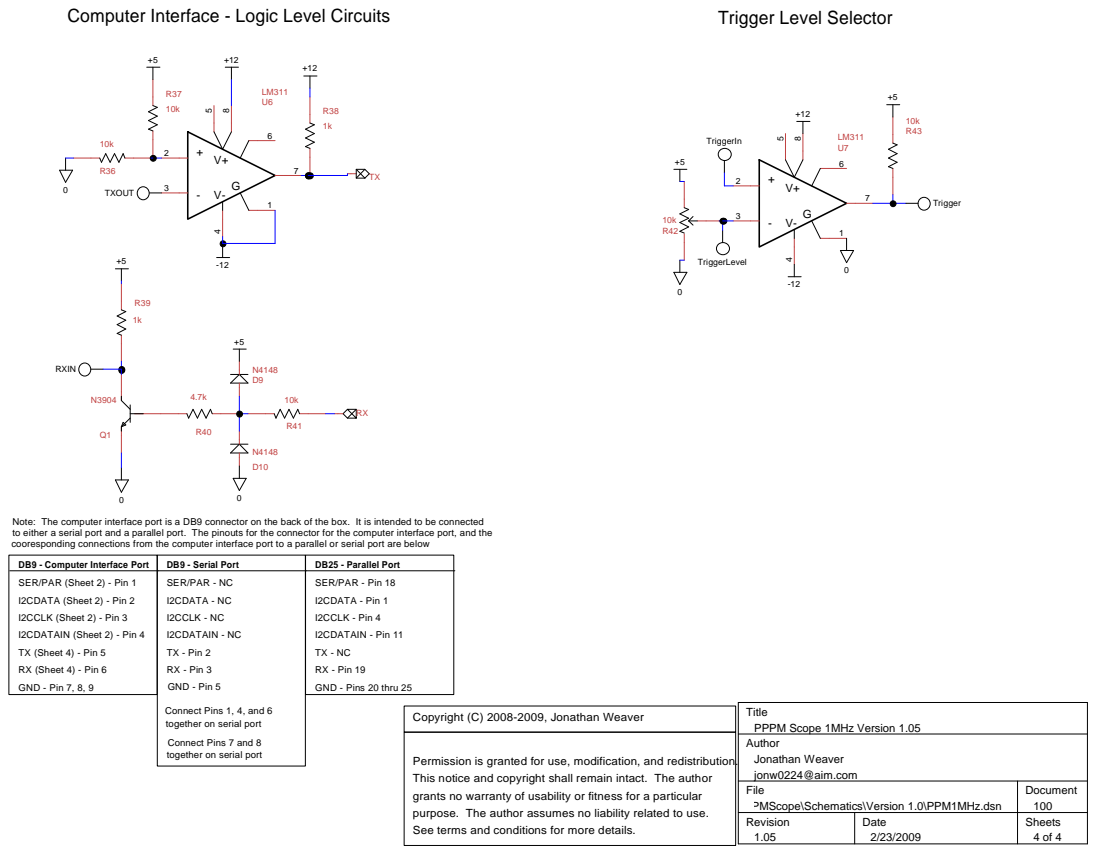
[picture p187: page 4]

Note: The computer interface port is a DB9 connector on the back of the box. It is intended to be connected
to either a serial port and a parallel port. The pinouts for the connector for the computer interface port, and the
cooresponding connections from the computer interface port to a parallel or serial port are below

DB9 - Computer Interface Port
SER/PAR (Sheet 2) - Pin 1
I2CDATA (Sheet 2) - Pin 2
I2CCLK (Sheet 2) - Pin 3
I2CDATAIN (Sheet 2) - Pin 4
TX (Sheet 4) - Pin 5
RX (Sheet 4) - Pin 6
GND - Pin 7, 8, 9

Connect Pins 1, 4, and 6
together on serial port
Connect Pins 7 and 8

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
