jonw0224/PPMScope/PCB/Version 1.05/PCBTopSilkMirrored.pdf

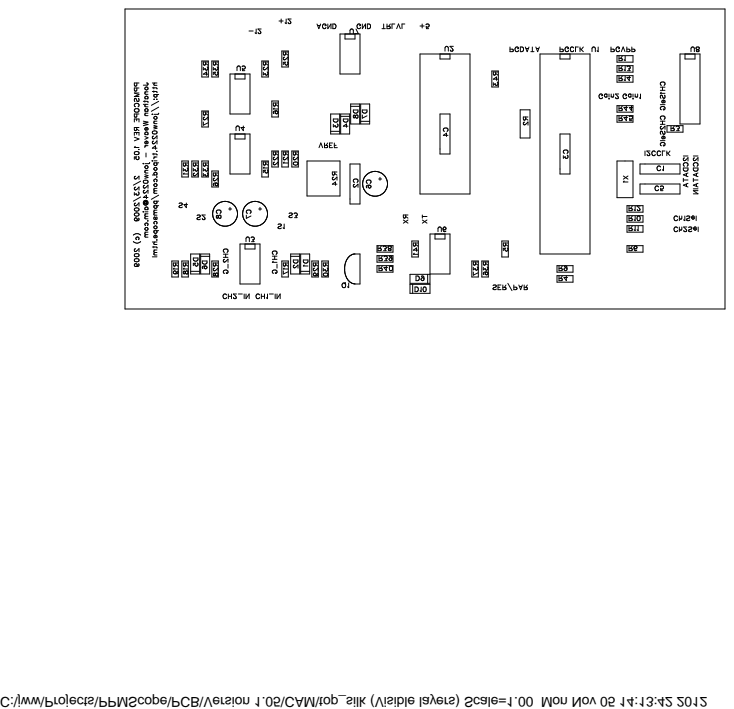
[picture p192: page 1]

C:\jww\Projects\PPMScope\PCB\Version 1.05\CAM\top_silk (Visible layers) Scale=1.00 Mon Nov 05 14:13:42 2012
