jonw0224/PPMScope/Spice/Analog Portion NE5534.asc

C1: cap; 4.7µ
C2: cap; 18p
D1: diode; 1N4148
D2: diode; 1N4148
D3: diode; 1N4148
D4: diode; 1N4148
R1: res; 100k
R2: res; 100k
R3: res; 100k
R4: res; 33k
R5: res; 33k
R6: res; 3.9k
R7: res; 3k
R8: res; 1k
R9: res; 1k
R10: res; 1k
R11: res; 1k
R12: res; 1k
R13: res; 6k
R14: res; 4k; tol=1 pwr=0.1
U1: NE5534
U2: NE5534
U3: NE5534
V1: voltage; SINE(0 5 1k 0 0 0 10); AC 1
V2: voltage; 12
V3: voltage; 12
V4: voltage; 5
Named nets: 0, Vp, Vn, Vin, Vs1, Vs2, Vs3, Vout, Vs
;dc V1 -15 15 0.1
.ac oct 100 1 100Meg
;tran 0 10m 0 100u uic
