jonw0224/PPMScope/Spice/Analog Portion TLE208.asc

C1: cap; 4.7µ
C2: cap; 18p
D1: diode; 1N4148
D2: diode; 1N4148
D3: diode; 1N4148
D4: diode; 1N4148
R1: res; 10k
R2: res; 10k
R3: res; 10k
R4: res; 3.3k
R5: res; 3.3k
R6: res; 3.9k
R7: res; 3k
R8: res; 1k
R9: res; 1k
R10: res; 1k
R11: res; 1k
R12: res; 1k
R13: res; 6k
R14: res; 4k; tol=1 pwr=0.1
U1: TLE2082
U2: TLE2082
U3: TLE2082
V1: voltage; PULSE(0 5 0 40n 40n 6u 12u 100); AC 1
V2: voltage; 12
V3: voltage; 12
V4: voltage; 5
Named nets: 0, Vp, Vn, Vin, Vs1, Vs2, Vs3, Vout, Vs
;dc V1 -15 15 0.1
;ac oct 100 1 100Meg
.tran 0 1200u 0 .1u uic
