jonw0224/PPMScope/Contributions/Paul Messer/DSOscope_A01/Simulation/Analog_Frontend_TLE208.asc

C1: cap; .1µF
C2: cap; 100pF
C4: cap; 10pF
C5: cap; .3pF
D1: zener; BZX84C8V2L
D2: zener; BZX84C8V2L
D3: diode; 1N4148
D4: diode; 1N4148
R1: res; 10
R2: res; 1MEG
R3: res; 100K
R6: res; 3.9k
R8: res; 1k
R9: res; 1k
R10: res; 1k
R11: res; 1k
R12: res; 1k
R13: res; 6k
R14: res; 4k; tol=1 pwr=0.1
R16: res; 110K
U1: TLE2082
U2: TLE2082
U3: TLE2082
V1: voltage; SINE(0 5 1k 0 0 0 10); AC 1
V2: voltage; 12
V3: voltage; 12
V4: voltage; 5
Named nets: 0, Vp, Vn, Vin, Vs1, Vs2, Vs3, Vout, Vs
;dc V1 -15 15 0.1
.ac oct 100 1 100Meg
;tran 0 10m 0 100u uic
AC/DC/GND SW
Short for Gain 1      => Av=1K/3.9K
Unshort for Gain 2  => Av=2K/3.9K
Unshort for Gain 5  => Av=2K/1.6K
3.9K for Gain 1
3.9K for Gain 2
1.6K for Gain 5
Short for 1X Atten
Open for 0.1X Atten
Open for 1X Atten
Short for 0.1X Atten
C5 is
2 parallel
Pin Diodes
back to back
