jonw0224/PPMScope/PCsource/default.cfg

WINDOWPOSITIONX=-8
WINDOWPOSITIONY=-8
WINDOWPOSITIONW=1457
WINDOWPOSITIONH=877
HARDWAREMODEL=DSOSCOPE
PORTTYPE=S
PORTNUMBER=2
PORTADDRESS=0x3BC
TICKCOUNT=10
CONFIGLOC1=-20
TRIGGERDELAY0=-1
TRIGGERDELAY1=-1
TRIGGERDELAY2=-1
TRIGGERDELAY3=123
SAMPLERATE0=0
SAMPLERATE1=0
SAMPLERATE2=21
BUFFERSIZE=256
ALLOWTIMEEQUIV=N
SAMPLEMODE=Stop
CHAVOLTPERDIV=2.000000
CHBVOLTPERDIV=2.000000
CHCVOLTPERDIV=5.000000
CHDVOLTPERDIV=5.000000
CHAOFFSET=1.000000
CHBOFFSET=-5.000000
CHCOFFSET=0.000000
CHDOFFSET=0.000000
CHAENABLED=Yes
CHBENABLED=Yes
CHCENABLED=No
CHDENABLED=No
CHA= Ch1
CHB= Ch2
CHC= Ch1
CHD= Ch1
TIMEPERDIV=5.000000e-004
RECONSTRUCTION=Triangle
SCREENATYPE=VoltTime
SCREENBTYPE=FreqMagn
SCREENCTYPE=Measurements
CHACOLOR=0x7F7FFF
CHBCOLOR=0xFF7F7F
CHCCOLOR=0x7FFF7F
CHDCOLOR=0xFFFF7F
SCRBGCOLOR=0x303030
SCRFGCOLOR=0x9F00
CUR1COLOR=0x30FFFF
CUR2COLOR=0x70FFFF
TRIGGERCOLOR=0x40FFFF
MEASURE1=None
MEASURESOURCE1=ChA
MEASURE2=None
MEASURESOURCE2=ChA
MEASURE3=None
MEASURESOURCE3=ChA
MEASURE4=None
MEASURESOURCE4=ChA
WEIGHTA=2
WEIGHTB=2
WEIGHTC=2
WEIGHTD=2
REFRESHRATE=10
HIGHRESMODE=Yes
PERSISTENCE=150
