jonw0224/PPMScope/PCsource/default2.cfg

WINDOWPOSITIONX=-8
WINDOWPOSITIONY=-8
WINDOWPOSITIONW=1297
WINDOWPOSITIONH=787
HARDWAREMODEL=PPMSCOPE
PORTTYPE=P
PORTNUMBER=0
PORTADDRESS=0x378
TICKCOUNT=10
CONFIGLOC1=-16
TRIGGERDELAY0=0
TRIGGERDELAY1=0
TRIGGERDELAY2=0
TRIGGERDELAY3=0
SAMPLERATE0=0
SAMPLERATE1=0
SAMPLERATE2=1
BUFFERSIZE=256
ALLOWTIMEEQUIV=N
SAMPLEMODE=Run
CHAVOLTPERDIV=5.000000
CHBVOLTPERDIV=4.360000
CHCVOLTPERDIV=2.000000
CHDVOLTPERDIV=5.240000
CHAOFFSET=0.000000
CHBOFFSET=1.744000
CHCOFFSET=-1.600000
CHDOFFSET=-9.432000
CHAENABLED=Yes
CHBENABLED=Yes
CHCENABLED=Yes
CHDENABLED=Yes
CHA= Ch1
CHB= Ch2
CHC= Ch1
CHD= Ch2
TIMEPERDIV=2.550000e-005
RECONSTRUCTION=Spline
SCREENATYPE=VoltTime
SCREENBTYPE=FreqMagn
SCREENCTYPE=FreqPhase
CHACOLOR=0x7F7FFF
CHBCOLOR=0xFF7F7F
CHCCOLOR=0x7FFF7F
CHDCOLOR=0xFFFF7F
SCRBGCOLOR=0x303030
SCRFGCOLOR=0x9F00
CUR1COLOR=0x30FFFF
CUR2COLOR=0x70FFFF
TRIGGERCOLOR=0x40FFFF
MEASURE1=None
MEASURESOURCE1=ChA
MEASURE2=None
MEASURESOURCE2=ChA
MEASURE3=None
MEASURESOURCE3=ChA
MEASURE4=None
MEASURESOURCE4=ChA
WEIGHTA=1
WEIGHTB=1
WEIGHTC=1
WEIGHTD=1
REFRESHRATE=10
HIGHRESMODE=No
PERSISTENCE=255
