jonw0224/PPMScope/DSOscope_SN00003_Weight2.cfg

WINDOWPOSITIONX=235
WINDOWPOSITIONY=140
WINDOWPOSITIONW=785
WINDOWPOSITIONH=590
HARDWAREMODEL=DSOSCOPE
PORTTYPE=S
PORTNUMBER=7
PORTADDRESS=0x35
TICKCOUNT=10
CONFIGLOC1=-91
TRIGGERDELAY0=0
TRIGGERDELAY1=0
TRIGGERDELAY2=0
TRIGGERDELAY3=0
SAMPLERATE0=0
SAMPLERATE1=0
SAMPLERATE2=26
BUFFERSIZE=250
ALLOWTIMEEQUIV=N
SAMPLEMODE=Off
CHAVOLTPERDIV=1.000000
CHBVOLTPERDIV=1.000000
CHAOFFSET=1.000000
CHBOFFSET=-2.000000
CHAENABLED=Yes
CHBENABLED=Yes
CHA= Ch1
CHB= Ch2
TIMEPERDIV=1.000000e-003
RECONSTRUCTION=Triangle
SCREENATYPE=VoltTime
SCREENBTYPE=FreqMagn
SCREENCTYPE=FreqPhase
CHACOLOR=0x7F7FFF
CHBCOLOR=0xFF7F7F
SCRBGCOLOR=0x303030
SCRFGCOLOR=0x9F00
CUR1COLOR=0x30FFFF
CUR2COLOR=0x70FFFF
TRIGGERCOLOR=0x40FFFF
MEASURE1=None
MEASURE2=None
MEASURE3=None
MEASURE4=None
WEIGHTA=2
WEIGHTB=2
REFRESHRATE=10
HIGHRESMODE=No
