jonw0224/PPMScope/PCsource/debug.c

/* ==============================================================================
 * Author:  Jonathan Weaver, jonw0224@aim.com
 * E-mail Contact: jonw0224@aim.com
 * Description:  Debug routines
 * Version: 1.0
 * Date: 11/18/2009
 * Filename:  debug.c, debug.h
 *
 * Versions History:  
 *      1.0 - 11/18/2009 - Added header to files
 *
 * Copyright (C) 2009 Jonathan Weaver
 * 
 * This file is part of PPMScope.
 * 
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
 * ============================================================================== 
 */
 
 #include <stdio.h>
 #include "settings.h"
 
static FILE *debugfile;


//& dOpen opens a file for output for use as a debugging tool
//& *dfile:  a character string for the filename
//& returns:  0 if successful, EOF if fails
int dOpen(char *dfile)
{
#ifdef DEBUGON
    debugfile = fopen(dfile, "w");  
    if(debugfile == NULL) 
        return EOF;
#endif
    return 0;
}

//& dClose closes the debugging stream
//& returns:  0 if successful, EOF if fails 
int dClose()
{
#ifdef DEBUGON
    return fclose(debugfile);
#else
     return 0;
#endif
}

//& dPrStr prints a string to the debug file excluding the terminating null
//& *toPrint:  a pointer to the null terminated string to print
//& returns:  0 if successful, EOF if fails
int dPrStr(char *toPrint)
{
#ifdef DEBUGON
    if(fputs (toPrint, debugfile) != EOF) 
        return fflush(debugfile);
    return EOF;
#else
     return 0;
#endif
}

//& dPrInt prints an inteter to the debug file
//& *toPrint:  an integer to print
//& returns:  0 if successful, EOF if fails
int dPrInt(int toPrint)
{
#ifdef DEBUGON
    if (fprintf(debugfile, "%d", toPrint) >= 0)
        return fflush(debugfile);
    return EOF;
#else
     return 0;
#endif
}

//& dPrFlt prints an float to the debug file
//& toPrint:  an float to print
//& returns:  0 if successful, EOF if fails
int dPrFlt(double toPrint)
{
#ifdef DEBUGON
    if (fprintf(debugfile, "%f", toPrint) >= 0)
        return fflush(debugfile);
    return EOF;
#else
     return 0;
#endif
}
