jonw0224/PPMScope/demo.cfg

WINDOWPOSITIONX=-8
WINDOWPOSITIONY=-8
WINDOWPOSITIONW=1383
WINDOWPOSITIONH=745
HARDWAREMODEL=PPMSCOPE
PORTTYPE=S
PORTNUMBER=2
PORTADDRESS=0x3BC
TICKCOUNT=10
CONFIGLOC1=-27
TRIGGERDELAY0=0
TRIGGERDELAY1=0
TRIGGERDELAY2=19
TRIGGERDELAY3=35
SAMPLERATE0=0
SAMPLERATE1=0
SAMPLERATE2=-118
BUFFERSIZE=255
ALLOWTIMEEQUIV=N
SAMPLEMODE=Run
CHAVOLTPERDIV=5.000000
CHBVOLTPERDIV=5.000000
CHCVOLTPERDIV=10.000000
CHDVOLTPERDIV=5.000000
CHAOFFSET=0.000000
CHBOFFSET=0.000000
CHCOFFSET=0.000000
CHDOFFSET=0.000000
CHAENABLED=Yes
CHBENABLED=Yes
CHCENABLED=Yes
CHDENABLED=No
CHA= Ch1
CHB=-Ch2
CHC= Ch1 * Ch2
CHD= Ch2
TIMEPERDIV=5.000000e-003
RECONSTRUCTION=Triangle
SCREENATYPE=VoltTime
SCREENBTYPE=FreqMagn
SCREENCTYPE=Measurements
CHACOLOR=0x7F7FFF
CHBCOLOR=0xFF7F7F
CHCCOLOR=0x7FFF7F
CHDCOLOR=0xFFFF7F
SCRBGCOLOR=0x303030
SCRFGCOLOR=0x9F00
CUR1COLOR=0x30FFFF
CUR2COLOR=0x70FFFF
TRIGGERCOLOR=0x40FFFF
MEASURE1=PerRMS
MEASURESOURCE1=ChA
MEASURE2=PerRMS
MEASURESOURCE2=ChB
MEASURE3=PerAvg
MEASURESOURCE3=ChC
MEASURE4=Phase
MEASURESOURCE4=ChB
WEIGHTA=2
WEIGHTB=2
WEIGHTC=2
WEIGHTD=2
REFRESHRATE=10
HIGHRESMODE=No
PERSISTENCE=150
